indare/pcb_work/AudioV2.1/review/cursor_neg_01_power_fault.md

# v2.1 否定側査読 — ① 電源と故障の形（Cursor）

- 作成: 2026-09-26（Cursor 並行査読、読み取り専用）
- 対象: `origin/claude/vibrant-cray-axng64` 先端の `AudioV2.1/DECISIONS.md` / `NOW.md`
- 観点: 電源と故障の形
- 読んだもの: `/tmp/v21-claude/DECISIONS.md`（§1〜§6・§10 中心）、`NOW.md`、`design_eval_review.md`、`ds_facts/power.md`・`njw1194.md`・`verify_njw1194.md`、`review/power_budget_v21.md`・`power_budget_v21_review.md`・`ch_ldo_reverse_review.md`・`njw1194_power_impl.md`、リポジトリ側 `review/rail_detect_review.md`（ソケット短絡・22 Ω）、`datasheets/Recom_RS6.pdf`（OLP 字句）・`datasheets/tone/NJR_NJW1194.pdf`（p3・p6・p11）
- 読まなかったもの: `AudioV2/`・`Audio/` の文書、DECISIONS §4（ADC 経路の詳細）・§7 の大半、図を決定の証拠とする読み（図は v2 写し）
- 判定: **支持**／**修正**／**棄却**／**穴**（決定に無い／矛盾）／**確かめられず**
- 重さ: **損傷**／**聴こえる**／**無害**

## 0. 結論（表）
| # | 重さ | 指摘の一行 | 判定 | 確度 |
|---|---|---|---|---|
| 1 | 損傷 | トーン ±7 V に DS 応用の 100 µF 級を載せ、逆流ショットキーは DNP のままでは、主電源断でトーン LDO の OUT–IN が数 V 開く | 修正 | 一次資料＋計算 |
| 2 | 損傷 | 立ち下がりしきい値 ≈10.5 V のままでは、ソケット短絡を `MON` が取り逃しうる。design_eval B1 の整定後 ≈13 V は DECISIONS に無い | 穴 | 計算（design_eval 再現） |
| 3 | 損傷 | ソケット短絡時の 22 Ω は約 1 W で「2 W 連続で開く」帯に入らず、OLP 未測と組で連続過熱の窓が残る | 穴 | 計算＋推論 |
| 4 | 損傷 | 空ソケット禁止は運用のみ。違反時に ch LDO の OUT が +11.5〜12 V で秒残る経路にハードが無い | 穴 | シミュレーション（ch_ldo_reverse） |
| 5 | 損傷 | NJW1194 は「電源 OFF 前 MUTE」を採らず、無電源チップへの入力は未決のまま直列 1 kΩ だけ | 穴 | 一次資料 |
| 6 | 聴こえる | 電源断では Pico／`+5V_COIL` が ±15 V より先に死に、B2／`RAIL_OK` でラッチを戻せない（自覚済み・GND 落としは DNP） | 支持 | 計算（design_eval） |
| 7 | 損傷 | R1 の故障最悪 107 % は OLP 150 % の下で流れ続け、排他はファーム＋手順だけ。OLP の形は未測 | 確かめられず | 一次資料（字句）＋計算 |
| 8 | 損傷 | PD 12 V 枝のチップヒューズは I²t・協調未収集。コイル固着 560 mA 連続では切れないと本文が認める | 確かめられず | 二次（決定本文） |
| 9 | 損傷 | ch LDO「実効 ≈5 µF」は品種の DC バイアス無しでは数値にならない | 修正 | 推論（査読の前提） |
| 10 | 無害 | 1 ch 通電の R1 予算（設計点 63 %、悲観 ≈80 %）の算術自体は崩れていない | 支持 | 計算（査読再現） |

## 1. 指摘詳細

### [損傷] トーン ±7 V の大容量＋ショットキー DNP で、電源断のたびにトーン LDO が OUT–IN 絶対最大を数 V 越えうる
**何が** — DECISIONS §1-6（±7 V は TPS7A49／TPS7A30、逆流ショットキーは置き場のみ・実装しない）。NJW1194 DS 応用回路は V+/V− に各 100 µF〔DS p8、`ds_facts/njw1194.md`〕。TPS7A49 絶対最大 OUT–IN +0.3 V〔`ds_facts/power.md` p5〕。主電源断の ±15 V 傾き 0.26〜0.45 V/ms〔design_eval_review §1.1〕。
**なぜ効くか** — NJW1194 の電源電流 12 mA typ〔DS p3〕が 100 µF を抜く速さは 0.12 V/ms。傾き 0.45 V/ms のとき追随できる容量の上限は \(I/\mathrm{slew}=12\,\mathrm{mA}/0.45\,\mathrm{V/ms}=26.7\,\mu\mathrm{F}\)。100 µF のまま IN が OUT を下回ったあと、IN がさらに 7 V 落ちる間（15.6 ms）に OUT は 1.87 V しか下がらず、OUT–IN は約 +5.1 V。傾き 0.26 V/ms でも約 +3.8 V〔計算〕。ch LDO 側は実効 ≈5 µF に抑えたが、トーン側は ch と同じ「DNP」に寄せただけで、DS の 100 µF 級との両立が無い。
**確度** — 一次資料（NJW・TPS7A の DS）＋計算。傾きの数値は design_eval の〔計算〕を再利用。
**外れる条件** — トーンレール容量を実効 ≲25 µF（0.45 V/ms・12 mA）まで落とす、または OUT→IN ショットキーを実装する、または電源断で ±15 V が ±7 V より遅く落ちる実装になる。
**判定** — **修正**

### [損傷] ソケット短絡を立ち下がり ≈10.5 V が見逃しうるのに、整定後の高いしきい値が決定に無い
**何が** — §5-1 の立ち下がり案 ≈±10.5 V（帯 10.24〜10.79 V、0.1 %）。design_eval_review §0 B1／§1.4: ソケット短絡で娘レール ≈ 親 − 22 Ω × LDO 電流制限 min 0.22 A。
**なぜ効くか** — 親 15.0 V なら娘 10.16 V（帯の下で検出）。親 15.9 V なら娘 11.06 V（帯の上で**検出しない**）〔計算〕。正常整定の最悪は約 13.57 V なので、design_eval が勧めた「整定後 ≈13 V」なら短絡と 1.9 V 離れるが、DECISIONS §5-1・§6-2 のしきい値案は ≈12 / ≈10.5 V のまま。取り逃すと ch LDO は電流制限のまま、22 Ω に約 1 W が載り続ける（次項）。
**確度** — 計算（design_eval の式の再現）。電流制限 min 0.22 A は TPS7A49 DS〔`ds_facts/power.md`〕。
**外れる条件** — 整定後の第 2 しきい値（≈13 V）をファーム必須にする、または親の上限を 15.0 V 付近に縛る、またはソケット短絡を別経路で見る。
**判定** — **穴**

### [損傷] ソケット短絡 ≈1 W は「2 W 連続で開く」22 Ω の守りから外れる
**何が** — §2-4（ヒューズ抵抗、2 W 連続で開く）、§3-14（±15 V 側に枝ヒューズ無し、22 Ω と RS6 OLP・LDO 制限に頼る）。
**なぜ効くか** — design_eval §1.4: 短絡に回せる電流は常時負荷を差し引き約 0.21 A → 22 Ω で約 1 W。品の狙いが「2 W 連続で開く」なら 1 W は溶けずに熱くなる帯。OLP がヒカップなら切れる可能性はあるが形は V21-実測-01 未了。しきい値取り逃し（#2）と重なると、ファームもヒューズ抵抗も止めない連続過熱になる。
**確度** — 計算＋推論（品番の単発／溶断曲線は §10-1 どおり未収集）。
**外れる条件** — 1 W で開く品にする、整定後しきい値で短絡を落とす、OLP が短時間で出力を落とすと実測で分かる。
**判定** — **穴**

### [損傷] 空ソケット禁止が運用約束だけで、違反時の逆流エネルギーにハードが無い
**何が** — §3-7 の運用前提と §6-2「ファームは空ソケットを検出できない」。ch_ldo_reverse_review: 空だと OUT が +11.5〜12 V で 1〜10 s 残る。逆流ダイオードは実装しない（置き場のみ）。
**なぜ効くか** — 空を選ぶと石の電流が無く、COUT 実効 ≈5 µF でも帰還分圧だけで抜ける。主電源断・PRST で IN が先に落ちると OUT–IN が数 V（査読の空ケース）。決定は「選ばない」と書くが検知もインターロックも無い。
**確度** — シミュレーション（ch_ldo_reverse）＋決定本文。
**外れる条件** — ソケット有無の検知、空選択のハード禁止、または OUT→IN ダイオードを実装する。
**判定** — **穴**

### [損傷] NJW1194 の無電源入力は DS 上未規定のまま未決で、DS の予防（OFF 前 MUTE）を採っていない
**何が** — §1-6: 入力直列 1 kΩ 既定、電源の無いチップへの入力は**未決**。電源断前 MUTE は狙わない（3 線経由 ≈4 ms、Pico 停止 ≈2 ms）。DS: 絶対最大入力 VIM＝V+/V−〔p3〕、電源 ON 前の入力で初期状態異常、**電源 OFF 前に MUTE で防ぐ**〔p11〕。等価回路でクランプはパッド直下・200 Ω の手前〔p6〕。
**なぜ効くか** — 電源が 0 のとき字面どおりなら入力許容は 0 V。直列 1 kΩ・上限 2.3 Vrms（3.25 Vpk）ならクランプ電流 ≈(3.25−0.6)/1 kΩ＝2.65 mA〔計算〕。±7 V の 100 µF へ 20 ms で約 0.5 V 押し上げうる〔計算〕。§1-6 の「約 ±0.6〜0.8 V」と同桁。異常の中身は DS に無く、投入後の全レジスタ書き直しで足りるかは不明。0 Ω に替えられる足場がある。
**確度** — 一次資料。押し上げは推論＋計算。
**外れる条件** — 無電源時に入力をリレー等で切る、OFF 予告で MUTE が間に合う保持を足す、実測で異常が無害と出る。
**判定** — **穴**

### [聴こえる] 電源断でラッチが最後の状態のまま残る（決定が受容している故障の形）
**何が** — §2-10（電源断ポップ、GND 落としは足場・DNP）、§5-4 B2、§5-7。design_eval §1.1: `PD_12V_SW`／Pico 3V3 は約 2 ms で失われ、娘 ±15 V は 10.5 V まで 9〜15 ms、7 V まで 17〜29 ms。B2 の電源もコイルも先に死ぬ。
**なぜ効くか** — 音声リレーが SET のまま ±15 V が数十 ms かけて落ち、HP／LINE に過渡が出る。次の規則①全リセットまでラッチは残る。決定は戻さない側（B6）を採っているので矛盾ではないが、①の故障連鎖として閉じない。
**確度** — 計算（design_eval）。
**外れる条件** — 電源断用 GND 落としを実装し、検知立ち下がりから保持容量でリセットパルスを出し切る。
**判定** — **支持**（受容として記録は正しい。残リスク）

### [損傷] R1 の故障 107 % と OLP「150 % continuous」の関係は、OLP 未測のまま予算の外の前提になっている
**何が** — §3-13（故障 4 枚×1 ch で 107 %、OLP は働かない読み）、§3-1／V21-実測-01。RS6: "OLP 150% load, continuous, automatic recovery"〔p5〕。合計か出力ごとか、しきい値か耐量かは DS に無い〔`ds_facts/power.md`〕。
**なぜ効くか** — 1 ch 設計点 63 % は足りる（#10）。壊れる形は「基板またぎ排他が外れたとき」。ジャンパ重複・衝撃で電源リレーが複数 SET、などで 107 % が継続しうる。OLP が定電流なら熱で壊れるまで流れ、ヒカップなら可聴の断続。どちらも基板前実測待ちのまま R1・§3-14・22 Ω 電力が決まる。
**確度** — 一次資料（字句）＋予算の計算。動作形は確かめられず。
**外れる条件** — V21-実測-01 で OLP 形が分かり、107 % で保護が働く／働かないが確定する。ハードで電源 SET 1 本だけを保証する。
**判定** — **確かめられず**（決定の「働かない」読みは保守として支持できるが、実装判断の根拠には未測）

### [損傷] PD 12 V 枝ヒューズは定格未決で、コイル固着では切れない
**何が** — §3-14・§3-8（速断チップヒューズ、コイル最悪 560 mA・30 ms で切れない値、固着 560 mA 連続ではヒューズは切れず L7805C 過熱保護が先〔推論〕）。§10-1: チップヒューズ DS 未収集。
**なぜ効くか** — 短絡で切れることとパルスで生き残ることの窓は品番の I²t が無いと閉じない。クランプ＋ヒューズの協調（L7805 短絡で 12 V 素通し）も同じ。±15 V 側を「置かない」判断は #3・#7 に依存。
**確度** — 決定本文の自己申告。DS 無し。
**外れる条件** — 各枝のふつう／パルス／短絡電流を決めて DS 付きで選定する。固着検知でソフト遮断する。
**判定** — **確かめられず**

### [損傷] ch LDO「実効 ≈5 µF」は、セラミックの DC バイアスを決めないと 5 µF にならない
**何が** — §3-7（実効 ≈5 µF、公称 10 µF は 12 V で下がるので実効で選ぶ）。ch_ldo_reverse_review: OPA2140 相当 3.6 mA で COUT 10 µF なら主電源断 +2.8 V、PRST +1.9 V。実効 4.7 µF なら尾 +0.6 V 級。
**なぜ効くか** — 「約 5 µF」は目標で、品種・定格電圧・DC バイアス曲線が無い。公称 10 µF／16 V を載せて実効 7 µF なら低電流石で再び数 V 開く。逆流ダイオードは DNP のままなので、容量選定が唯一の常時手当て。
**確度** — シミュレーション＋推論（バイアス曲線は未収集）。
**外れる条件** — 実効容量の測り方／候補品のバイアス表を決定に書く、またはショットキーを実装する。
**判定** — **修正**

### [無害] R1 の 1 ch 通電予算そのものは否定できない
**何が** — §3-13（設計点最悪 +127/−125 mA、定格 63 %）。power_budget_v21_review が算術を再現、漏れ・二重は 1〜5 mA、悲観重ねでも ≈80 %。
**なぜ効くか** — 容量不足で R1 を棄却する材料は無い。壊れるのは故障・電源断・短絡・逆流の形（#1〜#8）。
**確度** — 計算（査読再現）。
**外れる条件** — HP ソケットに重い石、同時多 ch、ADC を ±15 V に戻す、など前提崩壊。
**判定** — **支持**

## 2. 見たが問題を見つけられなかったところ
- EN を LDO の IN 分圧から作り FET で落とす形（§2-9）— USB のみ起動で EN>IN を構造で避ける筋は、読んだ範囲で崩れていない。
- B1（レール無の娘は音声 SET 不可）と音声 SET 共通 1 本（§2-6）の組み合わせ — 指令経路では電源無の娘をバスに繋がない、という主張は一貫している（衝撃・ARST 単一故障は別）。
- `PD_12V_SW` 検知＋規則①（起動時に既に検知あり）②③（§5-7）— 09-25 の「USB 先挿しで全リセットが走らない」「`MON` 兼用の誤良」への書き換えは、読んだ範囲で穴を塞いでいる。
- 娘バルク削除＋直列 22 Ω（§3-5・§2-4）— 共振・突入の議論は査読どおりで、電源故障の新しい主因にはなっていない。
- ch LDO の CNR/SS 必須（§3-7）— 起動落ち込みでしきい値を殴る経路を抑える判断は、今回の否定材料では覆らない。

## 3. 確かめられなかったこと
- RS6 OLP／SCP の実動作（出力ごと／合計、定電流／ヒカップ、短絡時入力電流）— V21-実測-01。#3・#7・22 Ω の連続電力がここに懸かる。
- NJW1194「初期状態の異常」の中身と、投入後の全書き直しで消えるか — DS に現象の定義が無い。
- トーン ±7 V を何 µF で実装するか — 決定に値が無く、DS 応用 100 µF との差分が未記入。
- チップヒューズ・22 Ω ヒューズ抵抗・B1 の PMOS／ツェナーの品番 DS（I²t・溶断・しきい値）。
- 電源断時に入力クランプが ±7 V をどこまで押し上げるか（1 kΩ・結合 C・源 Z の実測）。
- 図の現物ネット（写しの v2）を決定の証拠にする読み — 依頼どおり未使用。
