indare/pcb_work/AudioV2.1/review/cursor_neg_03_audio_path.md

# v2.1 否定側査読 — ③ 音声の経路の品質（Cursor）

- 作成: 2026-09-26（Cursor 並行査読、読み取り専用）
- 対象: `/tmp/v21-claude/DECISIONS.md` §1-5, §1-6, §2-3, §2-8〜2-11, §2-14, §4-*、`NOW.md`；`review/njw1194_io_review.md`, `direct_bypass_review.md`, `njw1194_alternatives_review.md`, `design_eval_review.md`；`ds_facts/njw1194.md`, `verify_njw1194.md`, `tap.md` / `verify_tap.md`, `switch_control.md`（必要箇所）
- 観点: ③ ライン入力〜NJW1194〜娘選択〜ch〜`AMP_SEL`〜ポット〜DEST/HP/LINE、DIRECT/スルー、結合C、ポップ・クリック、バス負荷、ADCタップが本線を汚すか、レベル整合。否定側。結論防衛しない
- 図: 文書上「写したまま（v2）」と明記。本査読は決定・査読・DS事実に限定（`AudioV2/`・`Audio/` 文書は未読）

## 0. 結論（表）

| # | 論点 | 判定 | 重さ | 一行 |
|---|---|---|---|---|
| 1 | 入口直列 1 kΩ（既定） | **支持**（代償は記録不足） | 無害〜聴こえる | クランプがパッド直下〔verify〕で外側だけが電流を決める。平坦 −0.42〜−0.56 dB、L/R 差最大 0.14 dB〔io査読〕 |
| 2 | 入口・出口 4.7 µF フィルム | **支持** | 聴こえる（段の角）／無害（低域） | 出口オフセット規定無し・入口は DC 利得 1。20 Hz 最悪 −0.10 dB。角は C でも残る |
| 3 | DIRECT＝スルー、MUTE→TSW | **修正** | 聴こえる | 音楽の硬い端は消えるが、TSW は音量**後ろ**。MUTE は出力 DC を消さない〔io査読〕。全リセット控えの条件が未実測 |
| 4 | 無電源チップへ源が来る | **穴** | 損傷（LDO）／聴こえる（投入異常） | §1-6 未決のまま 1 kΩ・ショットキー置き場（実装しない）で先へ進んでいる。源無しでも電源断の OUT–IN が越えうる〔io査読 §6.3〕 |
| 5 | `TONE` 100 kΩ | **支持**／値は**修正候補** | 聴こえる（待ち） | DC 基準は要る。4.7 µF×100 kΩ の 5τ≈2.4 s。TSW を全リセットに下げると ch 切替 0.25〜0.75 s の 3〜10 倍 |
| 6 | ch 入力 220 kΩ | **支持**（役割は変わった） | 無害 | IS(OFF) 漂流の保険は妥当。入出力同時切替では「聴こえる前に吸収」は取れず、全リセット待ちに吸収〔§2-14〕 |
| 7 | `AMP_SEL OUT`→DEST 直前（§4-14） | **支持** | 無害 | ミュート足場の内側。計測タップは前のまま。足場が 0 Ω/DNP なら端子も切替過渡を見うる（全リセット中は `AMP_SEL` は 100 kΩ で GND） |
| 8 | 差動 ADC（Q2）・本線汚れ | **支持（保険）**／本線副作用は**確かめられず** | 無害〜聴こえる | 本線に触るのはバッファだけ〔§4-1〕。グランド差の実効は未測（V21-実測-07）。縦積みの段間降下はセンスしない |
| 9 | 公称 2 / 上限 2.3 Vrms | **修正** | 聴こえる | 数字の算術は合う。2.3 の出自は旧 PT の THD=1% min。NJW 後は天井が ADC/石/TMUX に移ったが「きれいに通る上限」としては根拠が薄い |
| 10 | TMUX／リレー接点・47 Ω・コールド | **穴**（継-17）／構造は**支持** | 損傷（故障時）／聴こえる（ラッチ残） | コールド＋境目リレーは筋が通る。`V21-継-17`（出力 47 Ω）は理由が空。電源断で音声 SET 残存→無電源 TMUX へ源〔旧 DIRECT 査読の筋がラッチに残る〕 |

## 1. 指摘詳細

### [穴] 無電源の NJW1194 に源が来ることを「未決」のまま、入口 1 kΩ・ショットキー未実装で経路を固定している

**何が** — §1-6 状態欄末尾「未決: 電源の無いチップの入力に源が来ることを受けるか」。同時に入口直列 1 kΩ 既定・±7 V LDO の OUT→IN ショットキーは「置き場・実装しない」。DS: 電源断時の入力扱い無し；クランプはパッド直下でチップ内直列制限無し〔`verify_njw1194` 行 97・118〕。p11 は投入前入力→初期異常の注のみ。  
**なぜ効くか** — (a) 源あり: 1 kΩ でもレール押し上げは約 ±0.6〜0.8 V 見込みで LDO の OUT–IN 絶対最大 +0.3/−0.3 V を越える〔io査読〕。(b) **源無しでも** ±15 V が ±7 V より速く落ちれば毎回 OUT–IN が数 V まで開きうる〔同 §6.3〕。ショットキー未実装なら (b) は未決と無関係に残る。(c) 投入前信号は p11 どおり乱れうる；規則①の全レジスタ書き直しは「乱れのあと」の回復で、壊れ・ラッチアップを保証しない。  
**確度** — DS・絶対最大は一次；押し上げ電圧・落ち方の速さは推論＋要実測。  
**外れる条件** — ショットキーを実装し Vf≤0.3 V を使う電流で満たす／源を電源断中に切る／実測で OUT–IN が常に内側。  
**重さ** — 損傷（LDO・場合によりチップ）／聴こえる（投入時の異常状態）。

### [修正] 「MUTE してから TSW」は音楽の切断端だけを消し、DIRECT⇄トーンの DC 段と切替点のクリックは残しうる

**何が** — §1-6: DS p8「TSW 切替時は MUTE」、音量 MUTE→TSW。TSW は減衰器の**後ろ**〔njw1194 p8／io査読〕。出口オフセット規定無し；MUTE は DCCAP による DC 利得 1 のオフセットを消さない〔io査読〕。出口 4.7 µF は「居座らない」だけで、動いた瞬間の角はバスへ出る。  
**なぜ効くか** — 聴取中（音声リレー SET）に TSW すると、角は `TONE`→娘→利得 2→`AMP_SEL`→ポットへ出る。控えの「全リセットの中で書く」は段の実測待ちで、手順・待ち（§5 の 2.4 s 問題）が未固定。初期値 TSW=0（スルー）〔p11〕なので電源投入直後は DIRECT 側。  
**確度** — ブロック図の並びは DS；段の大きさは DS に無く未測。  
**外れる条件** — 実測で段が聴感下／常に全リセット窓で TSW＋十分な整定。  
**重さ** — 聴こえる。

### [修正] 上限 2.3 Vrms は NJW1194 採用後も数字だけ引き継ぎ、「経路品質の天井」としては根拠が腐っている

**何が** — §1-5: 公称 2・上限 2.3、両経路共通。旧 `direct_bypass_review`: 2.3＝PT2314E VOMAX（THD=1% min）で、typ では 2 Vrms でも約 0.1 % 級。§1-5 自身「NJW スルー max 3.6 Vrms min はもう天井にならず、先に頭を打つのは ADC 2.73 → 石 2.8〜 → TMUX 2.9〜3.5〔仮定〕」。V21-継-08 は 2.3×2＝4.6 Vrms を ADC FS の −1.5 dB に合わせるだけ。  
**なぜ効くか** — (1) 2.3 は「きれいに通る」上限ではない（旧査読の修正が DECISIONS 本文に残っていない）。(2) 本線の最初の制約は ADC より石の出力（約 2.8 Vrms）に近く、2.3 運用でも石しだいで肩に乗る。(3) スルーとトーン 0 dB の THD/雑音差はグラフ typ（約 0.005/0.01 %、1.41/2.2 µV）で、保証は最大出力・利得・分離だけ〔§1-6 前提〕—「両経路で同じ上限」は振幅の話であって品質の等価を意味しない。  
**確度** — 算術は再現済み；2.3 のユーザー判断は文書上の決定。  
**外れる条件** — 2.3 を「運用の都合（ADC VU の余白）」と明示し、本線品質の物差しから外す。  
**重さ** — 聴こえる（歪みの肩・経路差の誤読）。

### [修正／穴] 出口 4.7 µF × `TONE` 100 kΩ の整定を 5τ≈2.4 s に置くと、DIRECT 切替を全リセットに下げた瞬間に手順が破綻する

**何が** — §1-6.7: 100 kΩ のまま、長ければ 47 kΩ。io査読: 5τ=2.35 s；§6-2 の ch 切替 0.25〜0.75 s。投入時の支配は出口 C より DCCAP 100 µF 側の可能性〔io査読〕。  
**なぜ効くか** — TSW 段が聞こえて控えに落とすと、DIRECT 一回ごとに数秒無音になり、ch 聴き比べのテンポと噛み合わない。固定 5τ は段／許容から決めるべき〔同〕。  
**確度** — τ の算術は計算；DCCAP 支配は推論。  
**外れる条件** — 聴取中 MUTE+TSW で段が無視できる／47 kΩ＋実測待ちで 1 s 未満。  
**重さ** — 聴こえる（操作ギャップ）。UX としては損傷に近い。

### [穴] `V21-継-17`「出力側スイッチは 47 Ω の後ろ」が理由空のままコールド設計の前提に残っている

**何が** — §7 継-17 は決定文だけで理由・出典・ネット位置の再記述が無い。`design_eval_review` は「47 Ω 越しに娘の容量を充電」「ミュート時 τ＝2.2 µF×(R+47 Ω)」等で図の 47 Ω を引用するが、v2.1 の「入力も切る TMUX×2・全リセット」での役割の再確認が DECISIONS に無い。  
**なぜ効くか** — 47 Ω は (a) 出力 TMUX の容量負荷・短絡電流、(b) 無電源クランプ時の電流制限、(c) 雑音／分圧、のどれを主目的にしたかが不明だと、コールド故障（音声リレーが SET のまま電源喪失）で IIK ±30 mA〔TMUX DS〕を割るか判断できない。旧 DIRECT リレー案では Zs 50 Ω で越えうる〔direct_bypass_review #24〕— NJW スルー後も**ラッチ残存＋源**の形は娘側に残る。  
**確度** — 継項目の空疎は文書事実；電流超過は条件つき推論。  
**外れる条件** — 継-17 を v2.1 回路で再記述し、SET 残存時の制限抵抗として足りると示す。  
**重さ** — 損傷（故障・電源断の窓）／通常聴取では無害。

### [支持（条件つき）] 入口 1 kΩ・両側 4.7 µF 自体の低域・駆動は問題になりにくい

**何が** — 中域負荷約 40.7 kΩ、DS p24 は約 400 Ω まで振幅維持〔io査読〕。20 Hz −0.10 dB（最悪直列 0 Ω）。端子側 1 MΩ 置き場で浮き対策。  
**なぜ効くか（否定しきれない点）** — 容量負荷安定は DS に無し（出口直列 0 Ω 置き場は保険）。film 4.7 µF×4 の外形は未確認〔io査読〕。1 kΩ の L/R 差 0.14 dB はステレオ像では境界、ch 比較（共通経路）では無害。  
**確度** — 計算＋DS グラフ。  
**重さ** — 無害（低域・駆動）／聴こえる（L/R 差・安定は未確認）。

### [支持] `TONE`/`AMP_SEL` の NC 10 kΩ・バス 100 kΩ・全リセット無音の骨格

**何が** — §2-3 COM＝娘／NO＝バス／NC＝抵抗→GND。逆向きはバスを並列負荷〔査読〕。§2-10 は全リセット中に TMUX・LDO・結合整定を閉じ込め、ポット前 GND 落としは切替に使わない。  
**否定側の残り** — 「SET 瞬間が静か」は推論・未査読〔§2-10〕で V21-実測-12 待ち。電源断ポップと HP バッファ自身の崩れは消えない〔同〕。音声 SET 共通 1 本＋衝撃ラッチで別娘の電源が入る形はバスには出ないが RS6 負荷は増える〔§2-6〕。  
**重さ** — 通常切替は無害〜聴こえる（実測待ち）；電源断は聴こえる。

### [支持] ch 入力 220 kΩ（役割変更を明示せよ）

**何が** — §2-14: IS(OFF) max 0.15 nA で結合 C が 9 mV/分漂流→220 kΩ で 33 µV。入出力 TMUX 同時切替では旧「入力先閉じ待ち」は取れず、段差は全リセット整定へ〔§2-14〕。  
**否定側** — 選中は `TONE` 負荷に 220 kΩ が並ぶが、中域 40.7 kΩ 支配で駆動余裕は残る〔io査読〕。  
**重さ** — 無害。

### [支持／確かめられず] ADC タップは本線負荷としては軽い設計。差動は未実証の保険

**何が** — §4-1/4-2: 触るのは OPA1656 フォロワ；品質より本線非汚染優先。§4-3 Q2: INA1650、センスは娘→母の `A_GND` ピン際。§4-6: ADC 手前 47→100 Ωは**計測枝**（本線外）で電源断窓のクランプ電流対策。§4-7: `±15V_AFE` 22〜33 Ωでリップルの `A_GND` 注入を抑える。  
**否定側** — (1) グランド差の実効未測（V21-実測-07）；効かなければ Q2 は部品増のみ。(2) 縦積みで段間コネクタ降下はセンス外〔§4-3〕。(3) I²S／ADC デジが音声に漏れるかは V21-実測-06。(4) 100 Ω は ADC 精度 −0.09 dB と DS 推奨からの逸脱—本線には非該当。  
**重さ** — 本線汚れ: 確かめられず（設計意図は無害側）。計測の誤表示: 聴こえないが運用ノイズ。

### [支持] §4-14 `AMP_SEL OUT` を DEST 直前へ

**何が** — ポット前ミュート足場の後ろ、DEST 直前；HP/LINE ポット入口と同じ。タップは従来どおりミュート前。  
**否定側** — 足場直列が 0 Ω の間は端子インピーダンス＝`AMP_SEL`。ミュート実装時は 470 Ω〜1 kΩ で −0.17 dB（50 kΩ ポット）〔§2-10〕。外出しを「常時クリーンなラインアウト」と読むと、DEST/ポット前の信号であることの説明不足。  
**重さ** — 無害。

### [修正] DIRECT＝チップ内スルーにした結果、「トーンを通さない経路」の語義が変わったまま品質比較に使われている

**何が** — §1-5 見出しは「トーン段を通さない」。実装は音量段＋スルースイッチは通る（トーン EQ のみバイパス）。`njw1194_alternatives_review`: 同等単体は他に無く、代替は音量 IC 追加か旧リレー形。  
**なぜ効くか** — 石の差を聴く目的に対し、共通床が NJW の音量／スルー雑音・THD（typ／グラフ）になる。旧リレー DIRECT の「硬い端が本質」問題は消えたが、代わりに全 ch 共通の IC 床が乗る（PT 却下理由と同型）。  
**確度** — 構成は決定事実；床が聴き比べを潰すかは未測。  
**外れる条件** — ユーザーが「EQ 以外は共通でよい」と明示（NOW はそれに近い）。  
**重さ** — 聴こえる（比較の分解能）。

## 2. 見たが問題なし

- **COM＝娘／NO＝バス／NC＝抵抗**（§2-3）— 逆向きよりバスを汚さない。音声 10 kΩ・レール 2.2 kΩの算術は査読と一致。
- **娘の TMUX は切られた ±15 V、ソケットだけ ±12 V LDO**（§2-8・§3-3）— 膝を下げない／電源無し石をバスに繋がない、の筋は DS（入力保護・スイッチクランプ）と整合。
- **選んだ娘の TMUX は ch EN で切らない**（§2-8・継-16）— バス接続中の通電要求と一致。
- **NJW 中域駆動余裕**（約 40.7 kΩ vs 400 Ω級）— 出口バッファ不要の判断は DS グラフと整合。
- **ADC 前 100 Ω・AFE 直列 22〜33 Ω・RCOM 0 Ω** — 本線ではなく計測枝の自己防衛／戻り電流の話として一貫（本線汚染の主因にはならない）。
- **DEST＝機械スイッチ、音量＝手回しポット**（継-02〜04）— ファーム接点を出口に増やさない方針は経路品質にプラス。
- **PT2314E 却下＋スルー無し DSP 却下** — 全 ch 共通歪み／常時クロックを避ける否定側理由は妥当（NJW 床は上の修正で別問題）。

## 3. 確かめられず

- TSW／音量段切替の**実段電圧**、MUTE 中でも残る出力 DC、ゼロクロス有無の効き（Features 名のみで仕様無し〔verify 足すべき項目〕）
- 電源断時の ±15 V 対 ±7 V の落ち方、OUT–IN 最大、源あり／無しの入力電流（§1-6 実測リスト・io査読）
- 音声 SET 瞬間のポップ実測（V21-実測-12）、バウンス時間（AZ850 DS に無し）
- 縦積み 4 段の `TONE`/`AMP_SEL`/`A_GND` の接触抵抗・容量・段間降下が聴感・ADC に効くか
- Q2 が Q1 より本線／表示を良くするか（V21-実測-07）；I²S 漏れ（V21-実測-06）
- film 4.7 µF×4 の実装可能性；出口 C を入口のみに落とせるかのオフセット実測
- 公称 2 Vrms の出典（旧査読「リポジトリに無い」）；手持ち最悪石の実出力天井
- `V21-継-17` の 47 Ω の正確なネット位置と、v2.1 コールド故障電流での必要性
- NJW 3 線を UI MCP 3.3 V 直結で VIH 2.5 V を満たすか（余裕 0.1 V、AHCT 置き場）— 制御だが書き込み失敗は MUTE/TSW 失敗＝聴こえる経路事故

---

**総評（否定側）**: 結合 C・1 kΩ・バスプルダウン・全リセット無音・コールド＋境目リレーは、文書と DS が噛み合っている限り**本線を意図的に汚す決定ではない**。壊れているのは (1) **無電源入力／LDO 逆バイアスが未決・未実装のまま経路が固定されていること**、(2) **MUTE+TSW＝クリック無しという読み過ぎ**、(3) **2.3 Vrms と「DIRECT」語義が NJW 後に更新不足**、(4) **継-17 と整定待ちが手順と衝突しうること**。実装前に潰すべきは (1) と TSW 段の実測→手順分岐の固定。
