indare/pcb_work/AudioV2.1/review/cursor_neg_06_mech_stack.md

# v2.1 否定側査読 — ⑥ 機械・縦積み・筐体・手の届き（Cursor・追加観点）
- 作成: 2026-09-26（Cursor 並行査読、読み取り専用）
- 対象: `/tmp/v21-claude/DECISIONS.md` §1-4・§2-5・§2-13・§10（V21-未決-20 ほか）／同 NOW の装置・PCB 節。写しの PCB・配置スクリプトは現況の参照のみ（決定の証拠にしない）。`AudioV2/`・`Audio/` 文書は未読。

## 0. 結論（表）

| 重大度 | 件数 | 要旨 |
|---|---|---|
| 重大 | 2 | 装置目的の制約（DIP 手の届き）を未検証のまま 4 枚縦積みをいったん決めている／手の届きと「電源断してから抜き挿し」がサービス手順として衝突しうる |
| 要確認 | 5 | 2×12 のピン配置・キーイング未決／段間 5 mm＋部品高さ＋基板間距離が未設計／ラッチ誤動作の機械経路がソフト頼み／スタック接点定格未収集／シャーシ 1 点とパネル閉路が未決 |
| 軽微 | 2 | 写し PCB は横 3 スロットのまま／ジャンパ重複は「聴こえる」止まりで機械対策が後回し |

**総評:** 電気の木（縦積み・2×12・4 枚）は先に閉じ、機械の成立条件は §10 と統合リスト C3 に残したまま。装置の定義（DIP 差し替えで音を楽しむ）に対し、機械側が先に破綻する形になっている。

## 1. 指摘詳細

### [重大] 4 枚縦積み（§2-13）を、DIP 手の届き（V21-未決-20）の前にいったん決めた

**何が** — V21-継-22 は「DIP ソケットに手が届くこと」を装置目的上の最大の制約とし、縦積みでの確認を V21-未決-20 に委ねる。§2-13 は娘 4 枚をいったん決め、前提に「手が届くかは段の数で決まる（V21-未決-20）」と書くだけ。NOW も「残る未決: -20（縦積みの DIP の手の届き、模型）」と残す。統合リスト C3 は原寸模型を「先に測る」に置き、重さを「無害」とする。  
**なぜ効くか** — 1 枚 4 ch・4 枚＝16 ソケットが縦に重なる。下段の DIP に指・抜去具が届かなければ、採用した電気構成（1 種類・縦積み・§1-4）が装置目的と両立しない。枚数決定は接続ピン数（PSET×4）の帰結であり、手の届きの帰結ではない。  
**確度** — 一次資料（DECISIONS・NOW・design_eval_review C3）。到達可否の実測は無い。  
**外れる条件** — 原寸模型で 4 段まっすぐでも全ソケットに届く／階段・引き出し・上から抜く手順で届きが保証される、のいずれかが先に閉じた場合。

### [重大] 「DIP を挿し替える」運用と「活線で抜かない」運用が、積み上げたままでは両立しにくい

**何が** — §6-2 運用: 娘は電源を切ってから抜き挿しし、挿したら起動し直す（V21-未決-25 をいったんの決め）。装置はソケット差し替えが主作業（NOW 装置節・V21-継-22）。下段に届かないなら板を外す必要があり、外すたびに電源断＋再起動が必須。  
**なぜ効くか** — サービス 1 回のコストが「石を抜く」から「スタックを解体 → 電源断 → 再組立 → 全リセット起動」に膨らむ。目的が「切替で聴き比べ」なら、機械手順が比較の頻度を律速する。  
**確度** — 一次資料（§6-2・§2-13・V21-未決-20）。手順の所要時間は未計測。  
**外れる条件** — 積んだまますべての DIP に届く／差し替え専用の抜き出し機構が決まる、のいずれか。

### [要確認] 2×12 は本数だけ閉じ、ピン配置・キーイング・音声 2×5 との関係が未決のまま PCB 前提になっている

**何が** — §2-5: 制御・電源コネクタは 2×12（24 本）いったんの決め。内訳は並べたが「ピン配置は未確定」。V21-未決-22 は内訳を閉じた扱い。NOW PCB 節は「本数は v2.1 で 2×12」としつつ、写しは 2×8＋2×5・キーイング規則を「維持」。査読記録側には「電源・制御は 2×12、音声は 2×5（今のまま）」の整理案があるが、§2-5 本文は音声コネクタを明示しない。  
**なぜ効くか** — 4 段素通しでは 1 ピンの取り違えが全段に効く。キー無し・配置未決のまま外形・M3・南北辺だけ引き継ぐと、引き直しで電気決定と噛み合わない穴あけになる。音声と電源を別コネクタにするなら、両系の芯出し・嵌合順序・誤挿入も機械要件になる。  
**確度** — 一次資料（§2-5・NOW）。写し PCB は v2 幾何の参照のみ。  
**外れる条件** — ピンマップとキーイング（電源／音声の取り違え不可）が DECISIONS に決まり、外形規則がそれに合わせて書き直された場合。

### [要確認] 段間リレー 5 mm・部品高さ・基板間距離・冷却が、どの決定にも寸法として閉じられていない

**何が** — §2-1／V21-未決-19: 上下・隣のリレーは 5 mm 以上。AZ850 本体高さは約 5 mm（ds_facts）。写し生成コメントは基板間 15 mm・ロングテール約 11 mm（決定ではない）。v2.1 娘は電源用＋音声用で 1 枚 3 個のラッチ、DIP-8×4、LDO・デコーダ等が乗る。箱の外形・通風・ヒートシンクは未決。  
**なぜ効くか** — 基板間を狭めると (a) 上下リレーの 5 mm、(b) DIP／変換モジュールの背丈、(c) 指の侵入空間が同時に競合する。広げるとスタック全高が筐体に入らない。冷却は板間で対流が止まり、親の L7805C（パルス時 (12−5)×約 0.56 A ≈ 3.9 W 級〔計算〕）と HP バッファ（別査読で箱内熱が論点）の熱経路が未設計のまま残る。  
**確度** — DS・決定の制約は一次。15 mm は写しスクリプトの仮定。熱の箱内分布は未実測。  
**外れる条件** — 段間クリアランス表（リレー／DIP／電解／コネクタ嵌合）と筐体高さ・通風が決まり、模型で干渉ゼロが示された場合。

### [要確認] ラッチ誤動作の機械経路を、ファーム全リセットと B1 に寄せすぎている

**何が** — §2-1: 衝撃・前歴で状態が変わりうる（根拠は主に G6K・TQ。AZ850 本体 DS にラッチ反転の明文は無い〔bnd〕）。採用石は AZ850P2-5（§2-2）。§2-6: 聴取中に別娘の電源リレーが衝撃でラッチすると、その娘のレールと共通 ch 選択で LDO まで入り、「厳密に 1 ch」が電気的に破れる（音声はバスに出ない）。対処は次の切替の全リセット。同一パネル上の他リレー振動を警告するのは G6K 系。4 枚×3＝12 個が近接。  
**なぜ効くか** — 縦積みはリレー動作の衝撃・磁気が隣段に伝わりやすい。電気的ミュート／B1 は「バスに音が出ない」を守っても、「同時に温まる ch が 2 つ」や RS6 負荷の一時悪化は残る。機械ダンパ・スペーサ剛性・動作タイミングの分散が無い。  
**確度** — 一次資料＋DS。AZ850 での衝撃反転は「同種ラッチの一般論」〔推論〕。  
**外れる条件** — AZ850 実機でスタック実装の衝撃試験が通り、または非ラッチ／間隔・固定法で機械誤動作が消える場合。

### [要確認] スタックヘッダの接点定格（突入 0.68 A・コイル 560 mA パルス）が §10 の「DS を取るもの」のまま

**何が** — V21-継-23: 挿抜寿命は制約にしないが、電流は縦積みで上記パルスが乗るので品番 DS で確かめる。§10 本文も 2.54 mm スタックヘッダの接点定格を未収集と列挙。  
**なぜ効くか** — 4 段直列の接点は抵抗と劣化が段数で積む（spice 仮定 HOP_R 等）。電源メイクの繰り返しは接点溶着・接触圧低下の機械故障モード。電気の 22 Ω 設計が接点側で破綻しうる。  
**確度** — 決定・§10 の一次。品番未定のため数値は未照合。  
**外れる条件** — 採用ヘッダの DS でパルス電流・接触抵抗が余裕込みで合格し、金メッキ音声側の方針が固定された場合。

### [要確認] シャーシ 1 点（V21-継-20）の落とし先（V21-未決-15）が未決のまま、パネル配線が先行している

**何が** — NOW: FP は垂直実装→パネルネジ止め、HP/LINE は XH でパネルジャックへ、GND は XH 系統分離。§3-9: 木が成り立つのはシャーシを 1 点で落とすときだけ（パネル金属・ジャックスリーブ・PD シェルの閉路）。V21-未決-15 は未決のまま。  
**なぜ効くか** — パネル部品を先に仮組みすると、意図せず 2 点アースやスリーブ経由ループができ、電気決定（b-1・ADC の木）が筐体配線で壊れる。サービス（パネル脱着）のたびに再現しうる。  
**確度** — 一次資料。現物箱は未製作。  
**外れる条件** — 落とし先と絶縁／導通の部品表が決まり、パネル図がそれに従う場合。

### [軽微] 写し PCB は「横 3 スロット」のまま。縦積み 1 塔の親ラフが無い

**何が** — `place_a2_slot_connectors.py` は母板スロット 3 口横並び。NOW も中央＝娘タイルと書く。v2.1 決定は縦積み 4 枚・親スロット 1 系統。  
**なぜ効くか** — 決定と写しが食い違うと、ゾーン・ Edge・配線の教訓を「維持」と読んだ実装が横並び前提に戻る。  
**確度** — 写しは現況参照。決定の証拠ではない。  
**外れる条件** — 親を 1 塔用に引き直す前提が NOW／生成方針に明示された場合（すでに「引き直し」と書いてあるなら、横並び維持を明示的に捨てること）。

### [軽微] ジャンパで段選択（§2-5）の重複事故を、機械では潰していない

**何が** — §2-6 前提: ジャンパ重複で 2 枚が同じ段を選ぶ弱点は残る。design_eval C3: 階段にすれば線の回しでジャンパ不要、まっすぐならジャンパのまま。重さは「無害（ジャンパの重複は聴こえる）」。  
**なぜ効くか** — サービス時の設定ミスが電気排他（§1-2）を破る。聴こえる／電源余裕の話に落とすと、組み立て検査項目が消える。  
**確度** — 一次資料。  
**外れる条件** — 物理キー・1 箇所しか挿さらないジャンパ・段ごとに配線をずらす階段実装などで重複が構造的に不可能な場合。

## 2. 問題なし

- **§1-4（1 種類・1 枚 4 ch・切替素子の聴き比べなし）** — 機械的には同一カードの縦積みを可能にする方向。2 種 PCB の嵌合差を増やさない。否定側から見て、ここ自体が機械破綻の原因ではない。
- **音声／デジ／電源の XH 分離と FP 集約（NOW）** — パネル配線の系統分離方針は、シャーシ落とし先さえ決めれば機械と整合しうる。方針自体は機械否定の材料にならない。
- **活線挿入を運用で禁じる（§6-2／旧 V21-未決-25）** — コネクタ溶着・前歴持ち込みを避ける向きは機械・接点の安全側。禁じること自体は妥当（届き問題との衝突は別指摘）。
- **リレー隣接 5 mm を DS 制約として文書化したこと（§2-1／V21-未決-19）** — 制約の認識はある。未充足なのは寸法設計の側。

## 3. 確かめられず

- 原寸 4 段スタックで、下段 DIP-8（および変換モジュール）に指・工具が届くか（V21-未決-20・模型未実施）。
- 採用する基板間距離・スタッキングヘッダ品番・嵌合長・M3 スペーサの有無と剛性。
- AZ850P2-5 を 12 個近接実装したときの、動作衝撃によるラッチ誤遷移の有無（AZ850 DS に反転明文なし）。
- 2×12／2×5 の最終ピンマップ・キーイング・誤挿入試験。
- スタック接点の許容パルス電流・接触抵抗の段数積み（§10 未収集 DS）。
- 筐体外形・通風・L7805C／HP バッファ／RS6 の熱経路と箱内気温。
- シャーシ落とし先とパネル金属部の実配線（V21-未決-15）。
- 「階段積み」案のコネクタ芯ずれ・ケーブル／ピン曲げ応力（C3 の代替案の機械成立）。
