indare/pcb_work/AudioV2.1/review/adc_gnd_retree.md

# AudioV2.1 — ADC グランドの木の組み替え（回路図レベルの提案）

- 作成: 2026-09-25（エージェント。**リポジトリのファイルは変えていない**。出力はこのファイルだけ）
- 対象: `AudioV2.1/`（`MeasureControl` とルート `AudioV2Case`）。v2（`AudioV2/`）は見ていない
- ユーザーの決定（前提。ここでは蒸し返さない）: タップは `AMP_SEL_L/R` のまま／結合は Q2（`U1611` の後ろに INA1650、0 Ω・ジャンパで Q1 に戻せる）／
  ADC 経路は絶対品質不要、**本線を汚さないのが最優先**／ADC の LDO（`U1603`→`+3V3_A`、`U1606`→`+5V_A`）は PD 12 V から取る

## 出典の記号

| 記号 | 意味 |
|---|---|
| **[SF all]** / **[SF pin X]** / **[SF nets N]** / **[SF bom]** | このセッションで回した `python3 AudioV2.1/scripts/sch_facts.py all / pin X / nets --net N / bom --json` の出力 |
| **[SF gnd]** | `sch_facts.Design` を読み取り専用で回し、グランド 5 ネット（`A_GND` `D_GND` `PD_GND` `ADC_GND` `GND_COIL`）の 2 つ以上にピンを持つ部品を列挙したもの |
| **[G MC]** / **[G root]** | `MeasureControl.kicad_sch` / `AudioV2Case.kicad_sch` を読んだもの（シンボルの Description・図上の座標・テキスト注記・`lib_symbols` のピン名・シートピン一覧） |
| **[PCB]** | `AudioV2.1/AudioV2Case.kicad_pcb` のフットプリント座標（親ラフ段階） |
| **[RB]** / **[RB-pd]** | `python3 AudioV2.1/scripts/rail_budget.py`（無印）/ `--adc-from-pd` の出力 |
| **[tap:L]** **[pow:L]** **[sc:L]** **[op:L]** | `AudioV2.1/ds_facts/tap.md` / `power.md` / `switch_control.md` / `opamps.md` の行（照合済み） |
| **[PDF ファイル pN]** | このセッションで `pdftotext -layout` で開いた一次資料のページ（PDF ページ番号） |
| **[DEC:L]** / **[NOW]** | `AudioV2.1/DECISIONS.md` / `NOW.md` の記録（履歴であって事実の正ではない。引くときはそう書く） |
| **[計算]** | 上の出典の数値からの算術 |
| **〔推論〕** | 出典から直接は言えない、このエージェントの判断 |

---

## 0. 結論と、前提の照合結果

### 0.1 提案の木（要約）

```
Q2（差動・既定）                                   Q1（片側・戻し）
GND_COIL ─NT101─ D_GND ─NT1602─ PD_GND            GND_COIL ─NT101─ D_GND ─NT1602─ PD_GND
                  ├──NT1603── A_GND ─NT102─ AGND_SNS               ├──NT1603── A_GND ─NT102─ AGND_SNS
                  └──JP1601(2-3)── ADC_GND                         │            └──JP1601(1-2)── ADC_GND
                                                                   （ADC_GND–D_GND の直結は無い）
```

- **`NT1601`（`ADC_GND`–`A_GND`）を消し、3 ピンの選択子 `JP1601`（1=`A_GND` / 2=`ADC_GND` / 3=`D_GND`、1×3 ピンヘッダ＋シャント 1 個）に置き換える。**
  Q2 は 2-3、Q1 は 2-1。シャントは 1 個しか載らないので**両方同時（＝閉路）は機械的に起きない**。
  シャント無し（＝`ADC_GND` 浮き）は `ADC_GND`–`D_GND` の逆並列ショットキ（`D1612`/`D1613`）で受ける
- **GND センスは新ネット `AGND_SNS`**。ルートで `J_ANA101` pin 9（`AMP_SEL_L` の隣の `A_GND` ピン）に `NT102` で 1 点だけ結び、
  `MeasureControl` に新しいシートピンで入れて INA1650 の両 ch の IN− へ
- INA1650（新 `U1612`）の **REF は `ADC_GND`**（`VCOM` ではない）、COM は 1 MΩ で `ADC_GND`、電源は ±15 V、出力は既存の鎖（`U1602` 反転＋10 µF＋`U1608`/`U1601` の VCOM 基準反転ドライバ）の入口へ。**`U1602` は残し、+IN を `A_GND` → `ADC_GND` へ固定で移す**
- ADC 側のオペアンプ（`U1612`/`U1602`/`U1601`/`U1608`）の ±15 V デカップリングは**全部 `ADC_GND` に揃える**（RC で分けた `±15V_AFE` 経由を推奨）。`U1611` だけは `A_GND` のまま
- LDO の入力は `PD_12V_SW`（シートピン `ADC_V_IN` として既に `MeasureControl` に来ている）から **新しい PPTC＋RC** を通した `PD_12V_ADC`

### 0.2 前提の照合（ユーザーの記述 vs 回路図）

| 前提 | 回路図 | 判定 | 出典 |
|---|---|---|---|
| 今の木 `ADC_GND─NT1601─A_GND─NT1603─D_GND─NT1602─PD_GND`、`GND_COIL─NT101─D_GND` | `NT1601` = `ADC_GND`/`A_GND`、`NT1602` = `PD_GND`/`D_GND`、`NT1603` = `A_GND`/`D_GND`、`NT101` = `GND_COIL`/`D_GND` | **一致** | [SF pin NT1601/NT1602/NT1603/NT101] |
| グランドを跨ぐ部品は NetTie だけ | NetTie 4 個・コネクタ（ピンごとに別ネット）・`U201`（`A_GND`/`PD_GND`、絶縁 DC-DC）だけ | **一致**（5 ノード・4 辺の木） | [SF gnd] |
| ±15 V の帰りは `A_GND`（DC-DC） | `U201`（REC20K-2415DZ）: .6=`+15V`、.5=`A_GND`、.4=`-15V`、.2=`PD_GND`、.1=`F201` の後 | **一致** | [SF pin U201]、[SF bom] |
| DC-DC は RS6-1215D（±200 mA） | **回路図の `U201` はまだ `REC20K-2415DZ`**。RS6-1215D は [NOW] の「第一候補」で未実装。±200 mA は [pow:L25] | 注記 | [SF bom]、[pow:L25] |
| ADC の LDO の上流は `F1601` | `F1601`（**T1A slow 5x20**）は `J1602`（MC の予備 12 V 端子）→`PD_12V_SW` の間。**本線の給電 `J202`→`SW402`→`PD_12V_SW` にヒューズは無く**、枝ごとに `F201`（F2A fast→`U201`）・`F202`（PPTC 0.4 A→コイル）・`F1602`（PPTC 0.5 A→`U1607`）がある | **修正**: `F1601` は J202 経由の給電の上流ではない。PD 12 V から LDO を取ると**ヒューズの無い唯一の枝**になる | [SF pin F1601/J1602/J202/SW402/F201/F202/F1602]、[SF nets PD_12V_SW] |
| ADC 枝の帰り 最大 約 87 mA | `--adc-from-pd`: LDO 入力 typ 60.9 / max 86.9 mA を PD 12 V 側へ | **一致** | [RB-pd] |
| LDO は今 `+15V` 直結 | `U1603` .8(IN)/.5(SHDN)=`+15V`、`U1606` .8(IN)=`+15V`・.5(SHDN)=`+3V3_A`、GND=.3/.6/.7=`ADC_GND` | **一致** | [SF pin U1603/U1606]、[G MC lib_symbols ピン名] |

---

## 1. 部品の棚卸し（MeasureControl の ADC 経路と周辺）

「今」は [SF pin <REF>] の出力そのもの。**「提案」は本提案の変更**（変更なしは「—」）。
デカップリングの帰属（どの IC のためのコンデンサか）は Description があるものはそれ、無いものは [G MC] の図上の近さで書いた（**図上の近さは電気的な事実ではない**。PCB で確かめること）。

### 1.1 能動部品

| 部品 | ピン → 今のネット | 提案 | 理由 |
|---|---|---|---|
| **U1611** OPA1656（計測タップの＋側バッファ、ユニティフォロワ） | .3=`AMP_SEL_L`、.1/.2=`ADC_BUF_L`、.5=`AMP_SEL_R`、.6/.7=`ADC_BUF_R`、.8=`+15V`、.4=`-15V` | **±15 V・`A_GND` 側のまま。変更なし**（`ADC_BUF_x` に INA の IN+ と `JP1602`/`JP1603` の 1 番が足されるだけ） | 本線（`AMP_SEL`）に直接触る唯一の石。入力バイアス `R1659`/`R1660` も `A_GND`。Q2 での負荷は INA の入力（同相 212.5〜287.5 kΩ [tap:L102]）だけになり、今（4.7k∥6.19k の鎖）より軽い |
| **U1612（新）** INA1650（TSSOP-14） | — | 2 節。VCC(1)=`+15V_AFE`、VEE(14)=`-15V_AFE`、IN+A(2)=`ADC_BUF_L`、IN−A(4)=`AGND_SNS`、COM A(3)→1 MΩ→`ADC_GND`、REF A(12)=`ADC_GND`、OUT A(13)=`INA_OUT_L`。B 側は IN+B(7)=`ADC_BUF_R`、IN−B(5)=`AGND_SNS`、COM B(6)→1 MΩ→`ADC_GND`、REF B(9)=`ADC_GND`、OUT B(8)=`INA_OUT_R`。VMID(IN)(11)・VMID(OUT)(10) は no_connect | ピン番号は [PDF TI_INA1650.pdf p3]。両電源なら VMID は接続不要 [PDF TI_INA1650.pdf p16 §7.3.2] |
| **U1602** OPA1656（逆相を作る反転 −1、4.7k/4.7k） | .3/.5=`A_GND`（+IN）、.2←`R1601`、.1→`C1602`、.6←`R1612`、.7→`C1626`、.8=`+15V`、.4=`-15V` | **.3/.5 を `ADC_GND` へ（固定）**。.8/.4 を `±15V_AFE` へ | Q2 では入力（INA 出力）が `ADC_GND` 基準なので、反転の基準も `ADC_GND` でないと `A_GND`–`ADC_GND` の差が差動に乗る（2.3 節の式）〔推論〕。Q1 に戻したときの差は 3.4 節 |
| **U1608** OPA1656（L の VCOM 基準反転ドライバ ×2） | .3/.5=`VCOML`、.1→`R1613`→`VINL−`、.7→`R1617`→`VINL+`、.8=`+15V`、.4=`-15V` | .8/.4 を `±15V_AFE` へ。信号側は変更なし | ADC を直接駆動する石。負荷の帰りは ADC（`ADC_GND`）なので、電源の HF ループも `ADC_GND` で閉じるべき（4 節） |
| **U1601** OPA1656（R の同上） | .3/.5=`VCOMR`、.1→`R1602`→`VINR−`、.7→`R1608`→`VINR+`、.8=`+15V`、.4=`-15V` | 同上 | 同上 |
| **A1601** ADC1804_F（PCM1804 モジュール） | .1 `VINL+`、.2 `VCOML`、.3 `VINL−`、.4 `VINR−`、.5 `VCOMR`、.6 `VINR+`、.7 `ADC_MCLK`（SCKI）、.8 `ADC_LRCK`、.9 `ADC_BCK`、.10 `ADC_DATA`、.11 `ADC_nRST`、.12 `+5V_A`、.13 `+3V3_A`、.14 `ADC_GND` | 変更なし（`ADC_GND` の島の中心） | グランドピンは .14 の 1 本だけ [SF pin A1601]。モジュール内に PCM1804 のデカップリングとジャンパが載っている旨の注記 [G MC テキスト]。マスターモード（S/M=L）の注記 [G MC テキスト] |
| **Y1601** ASFL1 12.288 MHz | .1(ST)/.4(VDD)=`+3V3_A`、.2=`ADC_GND`、.3→`R1604` | 変更なし | ADC の島で閉じる。MCLK は Pico へ行かない（`ADC_MCLK` は `A1601.7`・`R1604.2`・`TP1601.1` だけ [SF pin R1604/TP1601/A1601]） |
| **U1603** LT1763-3.3 → `+3V3_A` | .1/.2=`+3V3_A`、.3/.6/.7=`ADC_GND`、.4→`C1608`(BYP)、.5(SHDN)=`+15V`、.8(IN)=`+15V` | **.8 と .5 を `PD_12V_ADC` へ**。GND は `ADC_GND` のまま | SHDN は未使用なら VIN へ [PDF ADI_LT1763.pdf p14]。IN・SHDN の絶対最大 ±20 V [pow:L389, L391] |
| **U1606** LT1763-5 → `+5V_A` | .1/.2=`+5V_A`、.3/.6/.7=`ADC_GND`、.4→`C1623`(BYP)、.5(SHDN)=`+3V3_A`、.8(IN)=`+15V` | **.8 を `PD_12V_ADC` へ**。SHDN は `+3V3_A` のまま（3V3 先行） | PCM1804 の絶対最大「VCC − VDD < 3 V」[sc:L338]、[PDF TI_PCM1804.pdf p5] のための既存の順序。組み替えで変えない |
| **U1605** TPS3307-33 | .1=`+5V_A`、.2/.3/.8=`+3V3_A`、.4=`ADC_GND`、.5=`ADC_nRST`、.7=`ADC_nMR`、.6 NC | 変更なし | `ADC_nMR` は Pico GP15（`A1602.20`、OD）から来る境界線 [SF pin A1602/U1605] |
| U1607 BP5293-50（`+5V_D`） | .1=`PD_12V_MEAS`、.2=`D_GND`、.3=`+5V_D` | 変更なし | Pico/LCD 用。ADC 側ではない |

### 1.2 受動部品（ADC 側の電源・基準）

| 部品 | 値 | 今 | 提案 | 備考 |
|---|---|---|---|---|
| C1605 | 100nF | `+15V`/`ADC_GND` | `PD_12V_ADC`/`ADC_GND` | U1603 の IN（図上 (316,37)、U1603 (340,37) の隣）[G MC] |
| C1606 | 10uF 50V X7R | `+15V`/`ADC_GND` | 同上 | Description「LT1763 IN bulk」[G MC]。IN のバイパスは 1〜10 µF で足りる [PDF ADI_LT1763.pdf p14] |
| C1618 | 100nF | `+15V`/`ADC_GND` | `PD_12V_ADC`/`ADC_GND` | U1606 の IN |
| C1619 | 10uF 50V X7R | `+15V`/`ADC_GND` | 同上 | Description「LT1763 IN bulk」 |
| C1603 / C1604 | 10uF 10V X7R / 100nF | `+3V3_A`/`ADC_GND` | — | U1603 OUT（Description「LT1763-3.3 OUT bulk」） |
| C1608 | 10nF | U1603.4(BYP)/`ADC_GND` | — | CBYP |
| C1616 / C1617 | 10uF 16V X7R / 100nF | `+5V_A`/`ADC_GND` | — | U1606 OUT |
| C1623 | 10nF | U1606.4(BYP)/`ADC_GND` | — | CBYP |
| C1624 / C1625 | 100nF / 100nF | `+5V_A`/`ADC_GND`、`+3V3_A`/`ADC_GND` | — | Description「A701 local bypass」（旧番号のまま） |
| C1614 | 100nF | `+3V3_A`/`ADC_GND` | — | U1605 VDD |
| C1601 | 10nF | `+3V3_A`/`ADC_GND` | — | Y1601 VDD（ASFL1 DS 指定の 0.01 µF） |
| R1611 | 10k | `+3V3_A`/`ADC_nRST` | — | リセットのプルアップ |
| **C1607 / C1615** | 100nF / 100nF | `VCOML`/`ADC_GND`、`VCOMR`/`ADC_GND` | — | VCOM のバイパス（Description「VCOML/VCOMR bypass to ADC_GND」）。DS は VCOM–AGND に 0.1 µF を推奨 [PDF TI_PCM1804.pdf p29] |
| **R1602 / R1608 / R1613 / R1617** | 47 | ドライバ出力→`VINR−`/`VINR+`/`VINL−`/`VINL+` | —（6 節で値の見直しの選択肢） | DS Figure 44 の R5/R6 = 47 Ω と同じ [PDF TI_PCM1804.pdf p30] |
| R1604 | 33 | Y1601.3→`ADC_MCLK` | — | ADC の島の中 |
| TP1601 | ADC_MCLK | `ADC_MCLK` | — | 同上 |

### 1.3 受動部品（アナログ鎖）

| 部品 | 値 | 今 | 提案 |
|---|---|---|---|
| C1628 / C1613 | 10uF 25V NP | .2=`ADC_BUF_L` / `ADC_BUF_R` | **.2 を新ネット `ADC_IN_L` / `ADC_IN_R` へ**（`JP1602`/`JP1603` の 2 番） |
| R1612 / R1601 | 4.7k 0.1% | .2=`ADC_BUF_L` / `ADC_BUF_R`（U1602 反転の入力抵抗） | **.2 を `ADC_IN_L` / `ADC_IN_R` へ** |
| R1615 / R1606 | 4.7k 0.1% | U1602 帰還 | — |
| C1626 / C1602 | 10uF 25V NP | U1602 出力→ | — |
| R1618 / R1614 / R1609 / R1603 | 6.19k 0.1% | ドライバ入力 | — |
| R1619 / R1616 / R1610 / R1607 ＋ C1632 / C1627 / C1620 / C1609 | 1k 0.1% ＋ 1.8nF C0G | ドライバ帰還 | — |
| R1659 / R1660 | 100k | `AMP_SEL_L`/`AMP_SEL_R` → `A_GND` | **— （`A_GND` のまま）**。U1611 の入力バイアス（Description）。`AGND_SNS` に付けると 77 µA pk 級の信号電流がセンス線に乗る〔計算: 7.74 V/100 kΩ〕ので付けない |

鎖の利得（参考、回路図の値から）: ドライバは 1k/6.19k の反転、差動で 2×1k/6.19k = 0.323 [計算]。PCM1804 のフルスケールは差動 ±2.5 V [PDF TI_PCM1804.pdf p7] → `AMP_SEL` 換算 7.74 Vpk（5.47 Vrms）[計算]。INA1650 は利得 1 [PDF TI_INA1650.pdf p6「Gain 1 V/V」] なのでフルスケールは変わらない。

### 1.4 デカップリング（±15 V）

| 部品 | 今 | 帰属（出典） | 提案 |
|---|---|---|---|
| C1646 / C1647 | `+15V`/`A_GND`、`A_GND`/`-15V` | U1611（Description「U1611 の ±15V_A デカップリング」） | **— （`A_GND` のまま）** |
| C1636 / C1641 | `+15V`/`A_GND`、`A_GND`/`-15V` | U1602（図上 x=72.4、U1602 電源ユニット x=81.3）[G MC] | **`+15V_AFE`/`ADC_GND`、`ADC_GND`/`-15V_AFE`** |
| C1637 / C1642 | 同上 | U1601（x=104.1 / 電源ユニット x=113.0） | 同上 |
| C1638 / C1643 | 同上 | U1608（x=135.9 / 電源ユニット x=144.8） | 同上 |
| C1634 / C1639 ＋ C1635 / C1640（10uF 50V、Description「+15V_A / -15V_A」） | 同上 | 入口のバルク（x=34〜42）。注記「バルクはアナログフロントエンドの電源入口付近に」[G MC テキスト] | **`±15V_AFE`/`ADC_GND` へ（RC の出口側のバルク）** |
| 新 C1653/C1654（1 µF）＋ C1655/C1656（100 nF） | — | U1612 | `+15V_AFE`/`ADC_GND`、`ADC_GND`/`-15V_AFE`。DS は各電源ピン–グランドに 1.0 µF＋0.1 µF [PDF TI_INA1650.pdf p29] |

**±15 V に残る石と、そのデカップリングの落とし先**:
`U1611` は ±15 V・`A_GND`（本線側）。`U1612`/`U1602`/`U1601`/`U1608` は ±15 V のまま（`+5V_A` 単電源化は 6.3 の選択肢）で、デカップリングは `ADC_GND`。
理由は 4 節（負荷の帰りが `ADC_GND` にある石は、電源の HF ループも `ADC_GND` で閉じる）。

### 1.5 コネクタ・NetTie・電源入口

| 部品 | 今 | 提案 |
|---|---|---|
| **NT1601** `A_GND-ADC_GND` | .1=`ADC_GND`、.2=`A_GND` | **削除**（役目は `JP1601` の 1-2 へ） |
| NT1602 `ADC_GND_IN-D_GND` | .1=`PD_GND`、.2=`D_GND` | — （Value の `ADC_GND_IN` はシートピン名で、ネットは `PD_GND` [SF all 別名]） |
| NT1603 `A_GND-D_GND` | .1=`A_GND`、.2=`D_GND` | — |
| NT101（ルート） | `GND_COIL`/`D_GND` | — |
| **NT102（新、ルート）** | — | `A_GND`（`J_ANA101` pin 9 のパッド際）–`AGND_SNS` |
| **JP1601（新）** 1×3 ピンヘッダ＋シャント | — | 1=`A_GND`、2=`ADC_GND`、3=`D_GND` |
| **D1612 / D1613（新）** ショットキ（例: 既存の `RB160M-30` を 2 個、逆並列） | — | `ADC_GND`↔`D_GND`（シャント忘れの保険。3.3 節） |
| **J1601** AUDIO（2P） | .1=`AMP_SEL_R`、.2=`AMP_SEL_L`（**グランド極が無い**） | **3P（L / `AGND_SNS` / R）にするか外す**。MC を別基板にしてケーブルで受ける案（`J1602`/`J1603` の Description「残すか外すかは B5 のハーネス判断」）を残すなら、センスの極が要る |
| J1602 V_IN | .1=`PD_GND`、.2→`F1601` | — |
| J1603 15_V_IN | .1=`+15V`、.2=`A_GND`、.3=`-15V` | — |
| C1610 / C1611 / C1612 | `PD_12V_SW`/`PD_GND` | — （Description は旧 U1604 時代の「ADC_V_IN bulk / Return on ADC_GND_IN」のまま。ネットは `PD_12V_SW`/`PD_GND`） |

---

## 2. INA1650 の置き方

### 2.1 位置と入出力

```
AMP_SEL_L ─ U1611A(フォロワ) ─ ADC_BUF_L ─┬─ JP1602.1 ─┐
                                          └─ U1612 IN+A │        ┌─ C1628 ─ R1618 ─ U1608B ─ 47Ω ─ VINL+
AGND_SNS ────────────────────────────────── U1612 IN−A  ├─ JP1602.2 = ADC_IN_L ┤
ADC_GND ─ U1612 REF A /  COM A ─1MΩ─ ADC_GND           │        └─ R1612 ─ U1602B(−1, +IN=ADC_GND) ─ C1626 ─ R1614 ─ U1608A ─ 47Ω ─ VINL−
                     U1612 OUT A = INA_OUT_L ─ JP1602.3 ┘
```

- INA1650 の伝達は VOUT = (VIN+ − VIN−) + VREF [PDF TI_INA1650.pdf p15 Eq.1]。IN+ に `ADC_BUF`、IN− に `AGND_SNS` なので**極性は Q1 と同じ**（鎖の後段はそのまま）[計算]
- **`U1602` は残す。** PCM1804 は差動入力で、逆相脚を作るのが `U1602`（+IN が今は `A_GND` [SF pin U1602]）。INA1650 は 2 ch（[PDF p3]）で L/R に 1 ch ずつ。逆相まで INA で作るとパッケージが 2 個（IQ も倍）になる〔推論〕
- 出力負荷: `R1612` 4.7k（`U1602` の仮想接地へ）∥ `C1628`＋`R1618` 6.19k（`U1608` の仮想接地へ）≈ 2.67 kΩ [計算]。DS の表の既定負荷 RL = 2 kΩ [PDF p6]、出力振幅は 2 kΩ で＋側 350 mV・−側 430 mV までレールに寄る [PDF p7]。フルスケール 7.74 Vpk は ±15 V の内側 [計算]

### 2.2 REF は `ADC_GND`（`VCOM` にしない）

- REF は「低インピーダンスで駆動すること」[PDF TI_INA1650.pdf p3 Pin Functions]、レイアウトは「低インピーダンス・低雑音の基準点（アナロググランドや VMID(OUT)）へ最短で」[PDF p29]
- 内部は 10 kΩ ×4 の差動アンプ [PDF p15]。利得 1 で REF ピンに流れる電流は (VREF − VIN+)/20 kΩ、フルスケール 7.74 Vpk で **約 0.39 mA pk/ch** [計算]
- `VCOM` は PCM1804 の出力（2.5 V、[PDF TI_PCM1804.pdf p29]）で、**出力インピーダンスの規定値は DS に無い**（p29 は VCOM–AGND に 0.1 µF を置けとだけ言う）。ここへ 0.39 mA pk の信号電流を入れると ADC の基準そのものを揺らす〔推論〕。
  VCOM は今どおりドライバ（`U1608`/`U1601`）の +IN（電流ゼロ）だけに使う
- REF を `ADC_GND` にすると INA 出力は `ADC_GND` 基準で、鎖の AC 結合（10 µF）はそのまま要る。DC 結合化はしない

### 2.3 `U1602` の基準をなぜ `ADC_GND` へ移すか（式）

`ADC_GND` を 0、`U1602` の +IN の電位を Vr、鎖の入口を x（`ADC_GND` 基準）、ドライバの利得を k = 1k/6.19k とする。

- `U1602` 出力 = 2Vr − x。VINL+ = −k·x、VINL− = −k(2Vr − x)（AC 分）→ **差動 = −2k(x − Vr)** [計算]
- Q2 で x = INA 出力（`ADC_GND` 基準）のとき、Vr = `A_GND` の局所電位のままだと、`A_GND`–`ADC_GND` の差 Vr がそのまま差動に乗る → **Q2 の意味が消える**。Vr = `ADC_GND`（= 0）にすれば差動 = −2k·x
- Q1（x = `ADC_BUF`、`AMP_SEL` そのもの）では、Vr = `A_GND` の局所なら `A_GND`–`ADC_GND` の差は同相に落ちる（ここは否定側査読 `review/tap_compare_review.md` §2.1 の表と同じ結論）。Q1 での扱いは 3.4 節

### 2.4 電源と IQ

- ±15 V（DS の推奨 4.5（±2.25）〜36（±18）V の内側 [tap:L90]、[PDF p5]）。**表の性能値（CMRR 85/91 dB など）は VS = ±18 V 条件** [tap:L97]。±15 V での CMRR の規定値は無い
- IQ（INA1650、IOUT = 0）: 8 / 10.5 / 12 mA（MIN/TYP/MAX）、全温度 max 14 mA [tap:L106]、[PDF p7]。両電源なので V+ から V− へ流れ、グランドには流れない〔推論〕
- 供給は `±15V_AFE`（4 節の RC の出口）

### 2.5 同相入力範囲 vs この回路が INA に見せる電圧

| 項目 | 値 | 出典 |
|---|---|---|
| 規定の同相範囲 | (V−)+0.25 〜 (V+)−2 V → ±15 V で **−14.75 〜 +13 V** | [PDF TI_INA1650.pdf p6]、[計算]。本文 §8.1.1 は下側を「負電源から 350 mV」と書いていて表（0.25 V）と食い違う [PDF p18] — 安全側の 0.35 V でも −14.65 V |
| 入力の絶対最大 | (V−)−0.5 〜 (V+)+0.5 V、±10 mA | [PDF p5] |
| IN+（`ADC_BUF`） | ADC フルスケール 7.74 Vpk。過大入力でも `U1611` は ±15 V 上なので絶対最大の内側 | [計算]、〔推論〕 |
| IN−（`AGND_SNS`）と REF の差 = グランドのずれ | **mV 級**（NetTie 間の IR 降下）〔推論〕。実測は無い | — |
| 同相分 | ≈ (IN+ + IN−)/2 ≈ 信号の半分 ＋ グランドのずれ | [計算] |

**グランドのずれは同相範囲に対して 3 桁以上小さい。** 範囲で詰まるのは信号の上側だけで、`AMP_SEL` が +13 V を超えるほど振れたとき（ADC はとうにクリップしている）。
しかも INA は `U1611` の後ろなので、INA 側で何が起きても `AMP_SEL`（本線）には返らない〔推論〕。

### 2.6 COM ピン

- COM は内部の 500 kΩ ×2（入力バッファのバイアス）の中点 [PDF p15, p16]。両電源では「グランドへ」[PDF p16]
- COM と「システムのグランド」の間に RCOM = 1 MΩ を入れると、20 Ω の信号源不整合での CMRR が 83.7 dB → 89.6 dB [tap:L101]、[PDF p18]。両電源＋AC 結合では立ち上がり時間を延ばさない [PDF p19]
- **提案: COM A/B それぞれ 1 MΩ（新 R1624/R1625）で `ADC_GND` へ。** センス線が切れても IN− は 500k＋1M で `ADC_GND` に引かれ、Q1 相当の片側測定に落ちるだけ（壊れない）〔推論〕
- この経路（`AGND_SNS`–500 kΩ–COM–1 MΩ–`ADC_GND`）は `A_GND` と `ADC_GND` の間の**高インピーダンスの第 2 経路**（1.5 MΩ）。グランドのずれ mV なら nA [計算]。NetTie の意味での閉路ではない

---

## 3. NetTie の木（Q2 / Q1）と、ジャンパで壊れないこと

### 3.1 Q2（既定、`JP1601` = 2-3）

| 辺 | 結ぶもの |
|---|---|
| NT101 | `GND_COIL`–`D_GND` |
| NT1602 | `PD_GND`–`D_GND` |
| NT1603 | `A_GND`–`D_GND` |
| **JP1601 2-3** | `ADC_GND`–`D_GND` |
| **NT102** | `A_GND`–`AGND_SNS` |

ノード 6（`A_GND` `D_GND` `PD_GND` `ADC_GND` `GND_COIL` `AGND_SNS`）、辺 5、全部つながる → **木（閉路なし）**。
`ADC_GND` と `AGND_SNS` はどちらも**葉**（辺が 1 本）なので、よその電流が通らない。

ADC の 12 V 枝の電流の経路: `PD_12V_SW`→F1604→R1621→`PD_12V_ADC`→LDO→ADC→`ADC_GND`→**JP1601**→`D_GND`→**NT1602**→`PD_GND`→`J202`。
**`A_GND` を通らない。** 今（`+15V` から）は `ADC_GND`→`NT1601`→`A_GND`→`U201.5` で、PCB の親ラフの座標では `NT1601`（86.8, 68.6）から `U201`（334.4, 41.4）まで `A_GND` の面を横切る [PCB]。

**`D_GND` に付けるか `PD_GND` に付けるか**（どちらでも木で、`A_GND` を通らない）:

| | `ADC_GND`–`D_GND`（推奨） | `ADC_GND`–`PD_GND` |
|---|---|---|
| I²S（ADC→Pico、Pico は `D_GND` [SF pin A1602]）の帰り | **1 ホップ**（今は `NT1601`→`A_GND`→`NT1603` の 2 ホップ） | 2 ホップ（`NT1602` 経由） |
| ADC の 87 mA の帰り | `D_GND` の短い区間（JP1601→NT1602）を通る | `PD_GND` へ直行 |
| `ADC_GND` の電位が乗るもの | `D_GND` の雑音（Pico/LCD、`NT101` 経由のコイル枝） | `PD_GND` の雑音 |
| Q2 での効き | どちらも INA の同相として除去（85 dB min @±18 V [tap:L97]） | 同じ |

〔推論〕 3 つの NetTie（NT1602・NT1603）と JP1601 を**1 か所に寄せる**なら差は小さい。I²S の帰りが短くなる `D_GND` を推奨する。

### 3.2 Q1（戻し、`JP1601` = 2-1）

| 辺 | 結ぶもの |
|---|---|
| NT101 / NT1602 / NT1603 / NT102 | 同上 |
| **JP1601 2-1** | `ADC_GND`–`A_GND` |

ノード 6・辺 5 → 木。今の図（`NT1601`）と同じ位相。
**違い**: LDO が PD 12 V なので、ADC の帰りは `ADC_GND`→JP1601→`A_GND`→NT1603→`D_GND`→NT1602→`PD_GND` になり、**JP1601 の 1 番と NT1603 の間の `A_GND` を横切る**。
Q1 は戻し用なので飲むとして、**JP1601 と NT1603 を隣接させ、その間の `A_GND` を短い島（音声の `A_GND` 面へは 1 点）にする**と、横切るのはその島だけになる〔推論・PCB〕。
（DECISIONS も「PCB では `NT1601` と `NT1603` を隣に置く」と書いている [DEC:222]。**今の親ラフでは `NT1601`（86.8, 68.6）・`NT1602`（181.8, 297.0）・`NT1603`（286.0, 440.0）で、離れている** [PCB]）

### 3.3 ジャンパの組み合わせで閉路・浮きが起きないこと

**グランドを選ぶのは `JP1601` の 1 個だけにする**（信号の切り替え `JP1602`/`JP1603` はグランドを選ばない。`U1602` の基準も切り替えない ← 2.3 / 3.4）。

| JP1601 の状態 | 結果 | 対策 |
|---|---|---|
| 2-3（Q2） | 木 | — |
| 2-1（Q1） | 木 | — |
| **1-2 と 2-3 を両方** | `ADC_GND`–`A_GND` と `ADC_GND`–`D_GND` が同時 → `NT1603` と並列の閉路 | **1×3 ピンヘッダ＋シャント 1 個なら物理的に起きない**（2 番ピンを 2 個のシャントが共有できない）〔推論〕。3 パッドのはんだジャンパだと起きうる |
| **どちらも無し** | `ADC_GND` が浮く。ADC の 87 mA が行き場を失い、I²S 出力ピンや INA の REF の ESD ダイオード経由で帰る〔推論〕 | **`D1612`/`D1613`（逆並列ショットキ、`ADC_GND`↔`D_GND`）**で浮きを 1 V 未満に抑え、87 mA を受ける。ダイオードは 87 mA を連続で流せる品（例: 既存 BOM の `RB160M-30` [SF bom]。DS はリポジトリに無いので定格は要確認） |

**ダイオードは Q1 のときに第 2 経路になるか**: Q1 では `ADC_GND`–`D_GND` のずれ ＝ JP1601＋`A_GND` の島＋NT1603 の IR 降下（87 mA × 数十 mΩ で数 mV 〔推論〕）。ショットキはこの電圧ではほぼ切れていて、流れるのは µA 級〔推論。リーク電流の DS 値なし〕。NetTie の意味の閉路ではない。
**Q2 では**ダイオードは JP1601 と並列（両端が同電位）で何もしない。

**信号の選択子 `JP1602` / `JP1603`**（1=`ADC_BUF_x`、2=`ADC_IN_x`、3=`INA_OUT_x`）も 1×3 ヘッダ＋シャントを推奨:

- 両方同時だと `U1611` の出力と INA の出力がぶつかる。`U1611` が電流制限に入ると帰還を失い、その入力（＝本線 `AMP_SEL`）の振る舞いが保証できない〔推論〕。**本線に触る唯一の失敗モードなので、グランドと同じく機械的に排他にする**
- 選び忘れ（シャント無し）は鎖の入口が浮くだけ（ADC 経路が止まる。本線に害なし）〔推論〕

**混在（グランドは Q2・信号は Q1、など）**: どれも木のまま。性能が落ちるだけ（例: 信号 Q1＋グランド Q2 だと `A_GND`–`ADC_GND` の差が `D_GND` の雑音込みで差動に乗る。2.3 の式）。壊れる組み合わせは無い〔推論〕。

一括で切り替えたいなら 3 回路のスライドスイッチ（ブレーク・ビフォア・メーク）で JP1601〜1603 を 1 個にまとめる手もある（「両方」も「無し」も電源断中の遷移だけ）〔推論〕。

### 3.4 Q1 の再現度（`U1602` の基準を `ADC_GND` に固定した場合）

今の Q1 は `U1602` の +IN が `A_GND` で、`A_GND`–`ADC_GND` の差 Vg は同相に落ちる（2.3）。
提案では +IN を `ADC_GND` に固定するので、Q1 に戻すと **Vg が差動に乗る**。ただし Q1 では `ADC_GND` と `A_GND` は JP1601（1-2）で直結なので、Vg は JP1601 自身と周りの銅箔の降下だけ（DC は 10 µF で切れる。残るのは ADC の電源電流の AC 分 × mΩ）〔推論〕。
一方、Q1 の支配的な誤差「ch 側グランド ↔ MC 側 `A_GND`」は、今の図でも 0 dB（信号と直列）[`review/tap_compare_review.md` §2.1]。**この固定で Q1 に足される誤差は、もともと Q1 にある誤差より小さい**〔推論〕。
それでも今の Q1 と厳密に同じにしたいなら、`U1602` の +IN も 1×3 ヘッダ（`A_GND`/`ADC_GND`）で選ぶ。ただしこれは **2 個目のグランド選択子**になり、JP1601 と食い違うと（例: JP1601=Q2 で `U1602`=`A_GND`）性能が落ちる（閉路にはならない。+IN に電流は流れない）。推奨はしない。

---

## 4. ±15 V のオペアンプの電流はどこを流れるか

前提（事実）: ±15 V の帰りは `U201.5` = `A_GND` [SF pin U201]。ADC 側の石（`U1612`/`U1602`/`U1601`/`U1608`）の出力の基準は `ADC_GND` 側（REF・VCOM・+IN）。

| 電流 | 大きさ | 経路（Q2） | `A_GND`↔`ADC_GND` を跨ぐか |
|---|---|---|---|
| 静止電流 | INA 10.5 typ / 12 max mA [tap:L106]、OPA1656 3.9 / 4.6 mA per ch [op:L127] | `+15V`→石→`-15V`（両電源） | **跨がない**（正負の電流が等しい限りグランドに流れない）〔推論〕 |
| INA の REF ピン電流 | 約 0.39 mA pk/ch（フルスケール）[計算、2.2] | `+15V`/`-15V`（`A_GND` 基準）→INA 出力段→内部 10k→REF→`ADC_GND` | **跨ぐ**: `ADC_GND`→JP1601→`D_GND`→NT1603→`A_GND`→`U201.5` |
| ドライバ→ADC 入力 | PCM1804 入力 10 kΩ（片側）[PDF TI_PCM1804.pdf p7]、1.25 Vpk/ピン（フルスケール）→ 0.125 mA pk/ピン [計算] | 同上→`VINx±`→ADC 内部→`ADC_GND` | VIN+ と VIN− は逆相なので大半は ADC の中で打ち消す。残り（不整合分）が跨ぐ〔推論〕 |
| 鎖の中の帰還・入力抵抗の電流（数 mA pk） | 例: 7.74 V/4.7k + 7.74 V/6.19k ≈ 2.9 mA pk/ch [計算] | オペアンプの出力 → 抵抗 → 別のオペアンプの出力（仮想接地）→ 電源ピン | グランドに入らない（出力どうしでレール経由で閉じる）〔推論〕 |
| ADC のスイッチトキャパシタ入力のキックバック（MHz 帯） | DS に数値なし | ADC→`ADC_GND`→ドライバのデカップリング→ドライバ電源ピン→出力→VIN | **デカップリングが `A_GND` なら跨ぐ**。`ADC_GND` なら島の中で閉じる |
| DC-DC のリップル電流 | RS6 は内部動作周波数 min 200 kHz [pow:L45]。リップル＆ノイズ 50 / 75 mVp-p（typ / max、1 µF MLCC 条件）[pow:L47] | `+15V`→デカップリング→そのグランド→…→`U201.5` | デカップリングが `ADC_GND` なら跨ぐ（→ RC で絞る） |

**結論〔推論〕**:

1. オーディオ帯の電流は、デカップリングをどちらに置いても DC-DC から来るので、跨ぐ量は変わらない（サブ mA、信号相関）。今（ADC の 60〜87 mA が全部 `NT1601`→`A_GND` を通る）より 2 桁小さい
2. HF（ADC のキックバック）は、**ドライバのデカップリングを `ADC_GND` に置けば島の中で閉じる**。`A_GND` に置くと MHz 帯の電流が `A_GND` の面（NT1603 から先）へ出る。本線を汚さない方向は `ADC_GND`
3. その代わり DC-DC のリップル電流が `ADC_GND` のコンデンサを通って跨ぐ。**`+15V`→R1622→`+15V_AFE`、`-15V`→R1623→`-15V_AFE` の直列抵抗（例 4.7 Ω、値は未決）**で絞る。
   4.7 Ω なら ADC 側 4 石の IQ 合計 max 39.6 mA/レール（INA 12 ＋ OPA1656 3 個 × 9.2 [RB の表]）で降下 0.19 V [計算]、C1635/C1640（10 µF）と組んで角 3.4 kHz、200 kHz で約 35 dB（理想）[計算]。フェライトビーズでもよい
4. `U1611` は `A_GND` デカップリングのまま（入力も負荷も `A_GND` 側。Q2 での負荷は INA 入力の µA 級）
5. 一貫性: **「負荷の帰りがどの島にあるか」で落とし先を決める**。ADC 側 4 石 → `ADC_GND`、`U1611` → `A_GND`。1 個の石の V+ と V− を別の島に落とさない

---

## 5. GND センス線

### 5.1 `AMP_SEL` はどこで作られ、何を基準にしているか

- `AMP_SEL_L` のピン: `U311`/`U312`（TMUX7612 の D）、`K301`〜`K304` の .7（リレー）、`J_ANA301`/`J_ANA302`/`J_ANA101` の .7、`J_PNL_A1601_1`/`J_PNL_A1602_1`（FrontPanel へ）、`SW501`（DEST）、`J_RAIL501.1`、`J1601.2`、`R1659`、`U1611.3` [SF nets AMP_SEL_L]
- 作っているのは娘（`AmpBankSwitch` の TMUX、`AmpBankRelay` のリレー）。その手前の AmpChannel の出力は 2.2 µF の後に 220 kΩ で `A_GND`（例 `C601`/`R603`、`C1001`→`R1003`）[SF pin R603/C601/R1003]
- 娘 → 母板は `J_ANA101`（2×5）: .7=`AMP_SEL_L`、.10=`AMP_SEL_R`、.1/.2/.4/.5/.8/.9=`A_GND`、.3/.6=`TONE_L/R` [SF pin J_ANA101]。娘側の `J_ANA301` も同じ並び [SF pin J_ANA301]
- 2×5 の奇数列（1,3,5,7,9）と偶数列（2,4,6,8,10）で、**.9 は `AMP_SEL_L`（.7）の隣、.8 は `AMP_SEL_R`（.10）の隣**（ピン配置からの読み）〔推論: `Conn_02x05_Odd_Even` の番号付けから〕
- `J_RAIL501`（ルート、3P）: .1=`AMP_SEL_L`、.2=`A_GND`、.3=`AMP_SEL_R`。Description「選択された Amp 出力の取り出し端子…DEST スイッチの手前…A_GND 極を持つ唯一の音声取り出し口」[G root]。親ラフで (15, 264)、`J_ANA101` は (222.4, 97.8) [PCB]

### 5.2 どこで拾うか

**提案: `J_ANA101` pin 9 のパッド際に `NT102`（`A_GND`–`AGND_SNS`）。** 1 本のセンスを L/R で共有（INA の IN−A・IN−B を両方 `AGND_SNS`）。

| 候補 | 良い点 | 悪い点 |
|---|---|---|
| **`J_ANA101` pin 9（または 8）** | `AMP_SEL` と同じコネクタ・隣のピンで娘から入ってくるグランド。娘を差し替えても（Switch/Relay）同じ点 | 娘の中の ch ごとのグランド差（4 ch のどれを選んだか）は残る。コネクタ接点の降下（`A_GND` ピンは娘の戻り電流も運ぶ）も含む〔推論〕 |
| `J_RAIL501` pin 2 | 外部で測るときの基準と同じ | 源（娘）ではなく母板の出口。`J_ANA101` から遠い [PCB] |
| 娘の中（TMUX の D の足元） | 源に一番近い | `J_ANA` に専用ピンが要る → 生成シート（`build_daughter.py`）と両版の娘を変える。今回はやらない |

**⚠ センスの NetTie は 1 個だけ。** 2 か所で `A_GND` に結ぶと、センス線が `A_GND` の並列経路になり、主電流が流れる（センスでなくなる）。場所を変えるときは「移す」であって「足す」ではない。

### 5.3 シートを跨ぐ経路

- `AGND_SNS` はルートで生まれて `MeasureControl` へ入る → **新しい階層ラベル `AGND_SNS`（MC 側、input）と、ルートの MC シートシンボルに同名のシートピン**が要る。今の MC のシートピンは `+15V_A` `-15V_A` `ADC_GND_IN` `ADC_V_IN` `AUDIO_L_IN` `AUDIO_R_IN` `A_GND` `I2C_SDA` `I2C_SCL` `3V3` `D_GND` `+5V_D` ほか LCD/TP/ENC 系 [G root シートピン一覧] で、`AGND_SNS` に当たるものは無い
- 片方だけ足すと `hier_label_mismatch`（CLAUDE.md）。足したら `sch_facts.py iface` で 0 件を確かめる
- **12 V と `PD_GND`/`D_GND` はシートピンが既にある**（`ADC_V_IN`＝`PD_12V_SW`、`ADC_GND_IN`＝`PD_GND`、`D_GND`）[SF all 別名]。電源側の組み替えに新しいシートピンは要らない
- 物理: `MeasureControl` は母板の上（[NOW] の PCB ゾーン）。コネクタは要らない。`J1601`（予備のケーブル受け、2P）を使う構成を残すなら 3P にしてセンスの極を足す（1.5）

### 5.4 バッファは要るか、電流はいくらか

- INA1650 の入力は内部でバッファされている（入力バッファ＋500 kΩ のバイアス、[PDF TI_INA1650.pdf p16 Figure 39 と本文]）。**外付けのバッファは不要**〔推論〕。足すとそのオペアンプ自身の基準・雑音・オフセットが IN− に乗る
- CMRR と信号源不整合: 20 Ω 不整合で 84 dB typ [tap:L99]、RCOM 1 MΩ なら 89.6 dB [tap:L101]。IN+ の源は `U1611` の出力（閉ループで ≪1 Ω〔推論〕）、IN− の源はセンス線の銅箔＋NetTie（サブ Ω〜1 Ω 級〔推論〕）。**不整合は 20 Ω より 1 桁以上小さい** → DS の typ 付近〔推論〕
- センス線の電流: IN− のバイアス電流（**DS の表に規定値が見つからなかった**）＋ 500 kΩ＋RCOM 1 MΩ を通る (Vg)/1.5 MΩ。Vg が mV なら **nA 級** [計算]。2 ch で倍でも µA に届かない。センス線の抵抗 1 Ω でも降下は nV〜µV [計算] → 細線でよい
- 引き回し〔推論・PCB〕: `J_ANA101` から MC へ、`AMP_SEL_L`–`AGND_SNS`–`AMP_SEL_R` の 3 本を並べて（ループ面積を小さく）、INA の近くで IN− へ。保護・EMI 用の直列抵抗を入れるなら IN+ と IN− に同じ値（0.1 %）を対で入れる（片側だけだと不整合になる）

---

## 6. 保護と電源の順序

### 6.1 ADC 枝の PPTC

- 本線の給電 `J202`→`SW402`→`PD_12V_SW` にはヒューズが無く、既存の枝は全部自分の保護を持つ（`F201` F2A fast、`F202` PPTC 0.4 A、`F1602` PPTC 0.5 A）[SF pin/bom]。`F1601`（T1A slow）は `J1602` の予備入口専用（0.2）
- LT1763 の電流制限は **min 520 mA**（全温度）[PDF ADI_LT1763.pdf p6]。出力短絡時に 12 V 側から 0.52 A 以上をサーマルで間欠的に引く〔推論〕。この電流は `U201` と同じ `PD_12V_SW` から来るので、PD 源が弱ければ ±15 V まで巻き込む〔推論〕
- **[DEC:226–250]「ADC 枝の PPTC は戻さない（2026-09-07）」の前提は、LDO が `+15V`（`REC20K` の SCP の後ろ）にあること**だった（同節の表の 3 行目は「`REC20K` の SCP → ヒカップ・自動復帰」）。PD 12 V 直結ではこの前提が成り立たない。**判断はユーザー**。提案は新 `F1604`（PPTC）を `PD_12V_SW` と R1621 の間に
- 定格: 枝の max 86.9 mA [RB-pd]。[DEC:1377] の記録は「LDO を 12 V から取るなら 0.15 A → 0.25 A、60 ℃ で 0.15 A 品の hold 105 mA」— **この温度ディレーティングは PPTC の DS がリポジトリに無く、未照合**。hold 0.25 A 級（RXEF 系の一段上）を候補とし、DS を取ってから確定

### 6.2 LDO の前の RC / LC

- LT1763 の入力リップル除去（グラフ、COUT 10 µF・IL 500 mA）: 100 kHz 約 37〜41 dB、**200 kHz 約 28〜32 dB**、1 MHz 約 21〜22 dB [pow:L414]
- `PD_12V_SW` には `U201`（DC-DC）の入力が載っている [SF nets PD_12V_SW]。RS6 の内部動作周波数は min 200 kHz [pow:L45]
- **提案: `PD_12V_SW`→F1604→`PD_12V_ADCP`→R1621（例 3.3 Ω）→`PD_12V_ADC`、C1651（47 µF）＋C1652（100 nF）を `PD_12V_ADC`–`PD_GND`**。LDO 足元の C1605/C1606/C1618/C1619 は `PD_12V_ADC`–`ADC_GND`
  - 数値〔計算〕: 降下 86.9 mA × 3.3 Ω = 0.29 V、損失 25 mW。角 1/(2π·3.3 Ω·57 µF) ≈ 0.85 kHz、200 kHz で理想 47 dB（電解の ESR で頭打ち。10 µF MLCC 級を並べれば 200 kHz で約 30 dB は残る〔推論〕）＋ LDO の 28〜32 dB
  - **フィルタのコンデンサの帰りは `PD_GND`**: `U201` のリップル電流を PD 側で閉じ、`ADC_GND`（→JP1601→`D_GND`→NT1602）へ回さない〔推論〕。U1607 の CIN の Description が同じ理屈（「PD_GND に落とすと入力の脈流ループが NT1602 を通ってしまう」の逆向き）[G MC C1645]
  - LC にしないのは、減衰がコンデンサの ESR と共振のダンピングで決まり、RC のほうが 87 mA では損失なく素直だから〔推論〕
  - `PD_12V_ADC` はパッシブ（R）の後なので、LT1763 の IN（power in）のために **PWR_FLAG が要る**〔推論: KiCad ERC の規則〕
- **COUT/ESR の安定域**（組み替えとは独立だが、入力を変えるついでに確認）: CBYP ≥ 1000 pF なら COUT 6.8 µF 以上、ESR 3 Ω 以下 [pow:L419–420]、[PDF ADI_LT1763.pdf p16]。ここの CBYP は 10 nF（C1608/C1623 [SF pin]）。COUT は `+3V3_A` が 10 µF **10 V** X7R（C1603）、`+5V_A` が 10 µF **16 V** X7R（C1616）[SF bom]。DS 自身が「16 V・10 µF の Y5V は 5 V で 1〜2 µF まで落ちうる」と書いている [pow:L420]。**X7R の DC バイアス後の実効容量が 6.8 µF を切らないかは部品の特性表で確かめること**（DS 値なし）
- 12 V 入力での LDO 損失: `U1603` (12−3.3) V × 35 mA ≈ 0.30 W、`U1606` (12−5) V × 45 mA ≈ 0.32 W、S8 の θJA 70 °C/W で +21〜22 °C [計算、pow:L416、負荷は [RB] の出典行（PCM1804 VCC 45 / VDD 20、発振器 15 mA max）]。`+15V` 入力時の記録 0.41 / 0.45 W [DEC] より下がる

### 6.3 PCM1804 のアナログ入力の絶対最大 vs ドライバ

- 絶対最大: VINx±・VCOMx・VREFx は **−0.3 V 〜 VCC+0.3 V**、ピン電流 **±10 mA** [PDF TI_PCM1804.pdf p5]（この行は `ds_facts` に無いので PDF から直接）
- **ADC を直接駆動するのは INA1650 ではなく `U1608`/`U1601`**（INA → `U1602`/10 µF → ドライバ → 47 Ω → VIN）[SF pin]。ドライバは ±15 V
- ドライバの +IN は VCOM（ADC の出力）。**ADC の電源が無い／立ち上がり中は VCOM ≈ 0 V**〔推論〕なので、ドライバ出力は 0 V を中心に信号 ±1.25 Vpk（フルスケール）で振れる [計算]
- VIN ピンのクランプ（VCC 側・GND 側の ESD）で受けると、47 Ω で制限される電流は (1.25 − 約 0.5) V / 47 Ω ≈ **16 mA pk** [計算。ダイオードの 0.5 V は仮定] → **±10 mA を超える**。過大入力（`AMP_SEL` ±13 V → ドライバ ±2.1 V）なら約 34 mA [計算]
- **組み替えで新しく起きるのは「±15 V はあるが ADC の電源が無い」状態**: 今は LDO が `+15V` から取るので、±15 V と ADC 電源は一緒に来る。PD 12 V から取ると、`F1604` が切れた・LDO が落ちた・PD が 12 V 以外を出した、などで起きる〔推論〕。起動時の順序も保証されない（RS6 の起動 2 ms typ [pow:L38]、LT1763 の起動は CBYP に比例する旨の本文のみ）
- 逆（ADC の電源はあるが ±15 V が無い）も新しく起きる: `F201` 断・`U201` 故障・**PD が 5 V を出したとき**（CH224K モジュールは 5/9/12/15/20 V をジャンパで選ぶ [`datasheets/StrawberryLinux_50224_CH224K.md`、メーカー記載]。RS6 は 9〜18 V [pow:L23] なので止まるが、LT1763 の `+3V3_A` は 5 V 入力でも出る〔推論〕）。このとき VCOM 2.5 V が無電源のドライバの +IN の ESD ダイオードへ流れる。OPA1656 の入力の絶対最大は (V−)−0.5〜(V+)+0.5 V・±10 mA [op:L135]
- ⚠ PD を 20 V にジャンパすると LT1763 の IN は絶対最大 ±20 V [pow:L389] ちょうど、RS6 は入力範囲外 [pow:L23]。これは `U201` 側も同じ事故

**対策の選択肢**（どれも未決）:

| 案 | 中身 | 得 | 損 |
|---|---|---|---|
| (a) 直列抵抗を上げる | 47 Ω → 100〜220 Ω | フルスケールの信号なら 10 mA 未満に〔計算: 0.75 V/100 Ω = 7.5 mA〕 | DS の推奨回路は 47 Ω（R5/R6「低インピーダンス駆動と雑音除去」[PDF p29–30]）。ADC 入力 10 kΩ と分圧で −0.1〜−0.2 dB〔計算〕。過大入力は守れない |
| (b) ドライバ（`U1608`/`U1601`）を `+5V_A`/`ADC_GND` の単電源にする | ドライバの出力が ADC の電源レールを超えられなくなる（構造的） | ±15 V の負荷が各レール max 18.4 mA 減る [RB の OPA1656 行 × 2] | `+5V_A` の負荷が同じだけ増え（PD 側 86.9 → 約 105 mA〔計算〕）、ADC の VCC にドライバの信号電流が乗る。OPA1656 の同相範囲 (V−)〜(V+)−2.25 V [op:L134] は 5 V で 0〜2.75 V、VCOM 2.5 V は余裕 0.25 V。出力振幅は 2 kΩ で (V−)+0.25〜(V+)−0.25 V [op:L128]、ここの負荷は約 0.9 kΩ（帰還 1k ∥ ADC 10k）でもっと狭いはず〔推論〕 |
| (c) 事故の窓だけと割り切る | 何もしない | 部品が増えない | `F1604` が切れた状態で音を出し続けると ADC の入力に 10 mA 超が流れ続ける〔推論〕 |
| (d) VCOM とドライバ +IN の間に 1 kΩ | 「ADC はあるが ±15 V が無い」側の電流を 2.5 mA に制限〔計算〕 | 部品 2 個 | +IN の雑音が増えるが L/R の 2 石とも同じ VCOM を見るので同相（除去される）〔推論〕 |

〔推論〕 本線への影響はどの案でも無い（ADC 入力で何が起きても `U1611` で止まる）。優先は ADC を壊さないこと。**(a) のフットプリント（値を後で上げられる）＋(d) を推奨**、(b) は ±15 V を削りたいときの選択肢として残す。

### 6.4 Pico への I²S が `ADC_GND` とグランドを共有すること

- 境界を渡る線: `ADC_DATA`・`ADC_BCK`・`ADC_LRCK`（`A1601`→`A1602` の GP0/GP1/GP2）、`ADC_nMR`（Pico GP15 → `U1605.7`）。`ADC_nRST`・`ADC_MCLK` は ADC 側で閉じる [SF pin A1601/A1602/U1605/R1604]
- ADC はマスター（「S/M=L…ADCマスタ 48k/256fs」の注記 [G MC テキスト]）→ BCK/LRCK/DATA は ADC の出力で、Pico は受けるだけ。Q2 の木（JP1601 2-3）で帰りは **`ADC_GND`→JP1601→`D_GND` の 1 ホップ**（今は 2 ホップ）
- `D_GND` の雑音は `ADC_GND` 全体を一緒に動かす（葉なので島の中に電位差は作らない）。INA から見れば同相 → 除去〔推論〕
- **ADC の電源が落ちて Pico が生きている**とき（USB だけ挿したときもこれ。`D1601` の注記「USB だけ挿すと Pico は動き LCD は消える」[G MC テキスト]）: GP0〜2 を入力で、内部プルアップ無しにしておけば ADC へ電流を押し込まない〔推論。RP2350 の既定のパッド状態は ds_facts に無い → ファームで確認〕。BCK/LRCK/DATA の絶対最大は −0.3〜VDD+0.3 V [PDF TI_PCM1804.pdf p5]
- 保険: `ADC_DATA`/`ADC_BCK`/`ADC_LRCK` に ADC 側で直列抵抗のフットプリント（0 Ω 既定、必要なら 330 Ω で 3.3 V/330 Ω = 10 mA に制限〔計算〕）。DS のデジタル出力負荷は max 10 pF [PDF p5]、330 Ω × 15 pF ≈ 5 ns で BCK 3.072 MHz の半周期 163 ns に対して小さい〔計算。BCK = 64 fS は `review/tap_compare_review.md` 1-4 の DS p23 読み〕。ネット名は分ける（例 `ADC_BCK` / `ADC_BCK_P`）
- `ADC_nMR` は Pico 側がオープンドレイン（「H は駆動しない」[G MC テキスト]）なので、ADC 側の電源が無くても押し込まない

---

## 7. 回路図の変更一覧と、残る決定

### 7.1 変更（回路図の言葉で）

**`MeasureControl.kicad_sch`（手編集可のシート）**

| # | 種類 | 中身 |
|---|---|---|
| M1 | 削除 | `NT1601`（`ADC_GND`–`A_GND`） |
| M2 | 追加 | `JP1601` 1×3 ヘッダ（1=`A_GND`、2=`ADC_GND`、3=`D_GND`）。シルクに Q1/Q2 |
| M3 | 追加 | `D1612`/`D1613` 逆並列ショットキ `ADC_GND`↔`D_GND` |
| M4 | 追加 | `U1612` INA1650（シンボルと TSSOP-14 FP を用意）。ピンは 1.1 表 |
| M5 | 追加 | `R1624`/`R1625` 1 MΩ（COM A/B → `ADC_GND`）。`U1612` の 10/11 に no_connect |
| M6 | 追加 | `C1653`/`C1654` 1 µF、`C1655`/`C1656` 100 nF（`U1612` の ±15V_AFE → `ADC_GND`） |
| M7 | 新ネット・分割 | `ADC_IN_L`（`C1628.2`・`R1612.2`）、`ADC_IN_R`（`C1613.2`・`R1601.2`）、`INA_OUT_L`/`INA_OUT_R`、`AGND_SNS` |
| M8 | 追加 | `JP1602`/`JP1603` 1×3 ヘッダ（1=`ADC_BUF_x`、2=`ADC_IN_x`、3=`INA_OUT_x`） |
| M9 | ネット変更 | `U1602.3`/`.5`：`A_GND` → `ADC_GND` |
| M10 | 追加・ネット変更 | `R1622`（`+15V`→`+15V_AFE`）、`R1623`（`-15V`→`-15V_AFE`）、PWR_FLAG ×2。`U1602`/`U1601`/`U1608` の .8→`+15V_AFE`・.4→`-15V_AFE`。C1634〜C1643 の `A_GND` 側 → `ADC_GND`、`+15V`/`-15V` 側 → `±15V_AFE` |
| M11 | そのまま | `U1611`・`C1646`/`C1647`・`R1659`/`R1660`（`A_GND`） |
| M12 | 追加・ネット変更 | `F1604`（PPTC、`PD_12V_SW`→`PD_12V_ADCP`）、`R1621`（`PD_12V_ADCP`→`PD_12V_ADC`）、`C1651`/`C1652`（`PD_12V_ADC`/`PD_GND`）、PWR_FLAG。`U1603.8`・`U1603.5`・`U1606.8`・`C1605/C1606/C1618/C1619` の `+15V` 側 → `PD_12V_ADC` |
| M13 | 追加 | 階層ラベル `AGND_SNS`（input） |
| M14 | 任意 | `ADC_DATA`/`ADC_BCK`/`ADC_LRCK` の直列抵抗（0 Ω）、VCOM–ドライバ +IN の 1 kΩ（`U1608.3/.5`、`U1601.3/.5` 側を新ネットに） |
| M15 | 任意 | `J1601` を 3P（`AMP_SEL_L`/`AGND_SNS`/`AMP_SEL_R`）に、または削除 |
| M16 | 注記の更新 | GND の注記（「NT1601=A_GND─ADC_GND（A1601 近傍・アナログ星点）…」）と電源系の注記（「+15V ─ U1603…」）が古くなる [G MC テキスト] |

**`AudioV2Case.kicad_sch`（ルート、手編集所有）**

| # | 種類 | 中身 |
|---|---|---|
| R1 | 追加 | `NT102`（`A_GND`–`AGND_SNS`）を `J_ANA101` pin 9 のそば |
| R2 | 追加 | MC シートシンボルにシートピン `AGND_SNS` |

**娘シート（生成物）は変えない。** `build_*` スクリプトも変えない。

### 7.2 検証（実装したとき）

- `python3 Audio/scripts/check_sexpr.py -q AudioV2.1`（CLAUDE.md の手順。v2.1 を対象に）
- `python3 AudioV2.1/scripts/sch_facts.py iface`（シートピンの不一致 0）、`pin U1612`、`nets --net ADC_GND` / `AGND_SNS` / `PD_12V_ADC`
- `kicad-run.sh erc AudioV2.1/AudioV2Case.kicad_sch`（[NOW] のとおり v2.1 は明示）。PWR_FLAG の要否はここで出る
- ネットリストで「グランド 6 ノードを結ぶのは NetTie・JP だけ」を `sch_facts` の同じ列挙（[SF gnd]）で再確認
- 部品数・ERC 件数の期待値は変わる（CLAUDE.md の表の更新は回路図を変えたコミットで）

### 7.3 ±15 V の負荷（RS6-1215D ±200 mA に対して）

[RB-pd] の固定側（ソケット以外）は `+15V` 71.1 / 90.8、`-15V` 35.9 / 42.6 mA（typ / max）。これに INA1650 の IQ 10.5 / 12 mA（両レール [tap:L106]）を足す [計算]:

| シナリオ（[RB-pd] の行） | `+15V` typ / max | `-15V` typ / max | RS6 ±200 mA に対する max |
|---|---|---|---|
| 固定側のみ（＋INA） | 81.6 / 102.8 | 46.4 / 54.6 | 51 % / 27 % |
| 1 ch・NE5532 | 87.6 / 118.8 | 52.4 / 70.6 | 59 % / 35 % |
| 1 ch・在庫の最悪 | 101.6 / 122.8 | 66.4 / 74.6 | 61 % / 37 % |
| 2 ch・NE5532 | 93.6 / 134.8 | 58.4 / 86.6 | 67 % / 43 % |
| 2 ch・在庫の最悪 | 121.6 / 142.8 | 86.4 / 94.6 | 71 % / 47 % |
| 8 ch・NE5532 | 129.6 / **230.8** | 94.4 / 182.6 | **115 %** / 91 % |
| 8 ch・在庫の最悪 | 241.6 / **262.8** | 206.4 / **214.6** | **131 % / 107 %** |

比較: ADC を `+15V` のまま（[RB] 無印）だと 2 ch・在庫の最悪で `+15V` max 217.7 mA（**109 %**）。PD へ移すと max 86.9 mA 減り [RB-pd]、INA で 12 mA 戻る [計算]。
**全 ch 通電は RS6 では足りない**（`rail_budget.py` の表は REC20K/REC10K だけで RS6 の列が無い。上の % は手計算）。何 ch まで同時に生かすかはファームの決定（[NOW]）。
信号電流（帰還網・負荷）は `rail_budget.py` 自身が積んでいない（出力の注記）。6.3 (b) を採るとさらに各レール max 18.4 mA 減る。

### 7.4 残る決定・PCB が要るもの

| # | 決めること | 選択肢 | 何で決まるか |
|---|---|---|---|
| 1 | `ADC_GND` の Q2 の相手 | **`D_GND`（推奨）**／`PD_GND` | I²S の帰りを取るか、ADC の帰りを `D_GND` に通さないほうを取るか（3.1）。星を 1 か所に寄せるなら差は小さい |
| 2 | JP1601〜1603 の形 | **1×3 ヘッダ＋シャント**／3 パッドはんだジャンパ（「両方」を物理的に防げない）／3 回路スライドスイッチ | 排他性（3.3） |
| 3 | `D1612`/`D1613` の品と、そもそも入れるか | `RB160M-30` ×2／他 | 87 mA を連続で受けられるか（DS がリポジトリに無い） |
| 4 | センス点 | **`J_ANA101` pin 9**／pin 8／`J_RAIL501.2`／娘に専用ピン（生成シートの変更） | ch ごとの差をどこまで追うか。1 点だけにすること（5.2） |
| 5 | RCOM | **1 MΩ**／0 Ω | DS §8.1.2（1 MΩ で不整合に強い） |
| 6 | `±15V_AFE` の RC | 4.7〜10 Ω／フェライト／入れない | DC-DC の実リップル（RS6 か REC20K か）。入れないなら ADC 側 4 石のデカップリングを流れるリップル電流が JP1601→NT1603 を跨ぐ |
| 7 | LDO 前の RC と PPTC の定格 | R 2.2〜4.7 Ω、C 47 µF＋MLCC、PPTC hold 0.25 A 級 | PPTC の DS（温度ディレーティング）を取ってから。**[DEC]「PPTC は戻さない」の前提が変わる点をユーザーが判断** |
| 8 | ADC 入力の保護 | 6.3 の (a)〜(d) | ADC を壊さない優先度 |
| 9 | I²S の直列抵抗 | 0 Ω／33〜330 Ω | ファームのパッド設定の確認と、ADC 電源断時の運用 |
| 10 | `J1601` | 3P 化／削除 | B5 のハーネス判断（MC を別基板にする可能性を残すか） |
| 11 | DC-DC | `REC20K`（図）／`RS6-1215D`（候補） | 同時通電 ch 数。RS6 なら全 ch は不可（7.3） |
| 12 | INA1650 の ±15 V での CMRR | 規定値なし（表は ±18 V） | 必要なら実測 |
| 13 | **PCB** | JP1601・NT1602・NT1603 を 1 か所に（今の親ラフでは離れている [PCB]）／`ADC_GND` の島の境界に INA1650（入力側ピン 1〜7 を `U1611` 側へ、REF/OUT 側 8〜14 を島の中へ [PDF p3 のピン配置]）／`AMP_SEL_L`–`AGND_SNS`–`AMP_SEL_R` の 3 本並走／`PD_12V_ADC` を星の近くを通して島へ（LDO の DC ループを小さく）／`ADC_GND` の島は 1 か所（JP1601）でしか外とつながらないゾーンにする（[NOW]「ベタ GND は 1 枚にできない。系統ごとに別ゾーン」） | 配線段階（B5） |

### 7.5 使わなかった／確かめられなかったもの

- INA1650 の入力バイアス電流: `TI_INA1650.pdf` の電気的特性表（p6〜7）の抽出に見つからなかった
- PCM1804 の VCOM の出力インピーダンス・CMRR: DS に無い（p7 と p29 を見た範囲）
- PPTC（RXEF 系）・ショットキ（RB160M-30）の DS: リポジトリに無い
- REC20K のリップル・起動時間: `ds_facts/power.md` に REC20K の節が無い（[NOW] の「265 kHz・100 mVp-p」は記録であって照合していない）
- ADC 側の電流の実測値（グランドのずれ Vg）: 無い（`review/tap_compare_review.md` 4-5 も同じ）
