indare/pcb_work/AudioV2.1/review/adc_gnd_retree_review.md

# 否定側査読: `AudioV2.1/review/adc_gnd_retree.md`（ADC グランドの木の組み替え）

- 作成: 2026-09-25（査読エージェント）。**リポジトリのファイルは変更していない**。書いたのはこのファイルだけ
- 対象: `AudioV2.1/review/adc_gnd_retree.md`（以下「提案」）。回路図は `AudioV2.1/`
- 前提（ユーザー決定。蒸し返さない）: タップは `AMP_SEL_L/R`／結合は Q2（`U1611` の後ろに INA1650、Q1 に戻せる）／ADC 経路に絶対品質は不要、本線を汚さないのが最優先／ADC の LDO は PD 12 V から
- 追加の前提（コーディネータ経由のユーザー前提）: PD → DC-DC の給電は主電源スイッチで切り替わり、ADC の LDO の枝もそのスイッチの後ろから取る。→ **回路図で確認した**（下の 1 行目・§7）

## 出典の記号

| 記号 | 意味 |
|---|---|
| [SF pin X] / [SF nets N] / [SF rails] / [SF iface] / [SF aliases] | このセッションで回した `python3 AudioV2.1/scripts/sch_facts.py pin X / nets --net N / rails / iface / aliases` |
| [SF gnd] | `sch_facts.Design` を読み取り専用で回し、`A_GND` `D_GND` `PD_GND` `ADC_GND` `GND_COIL` の 2 つ以上にピンを持つ部品を全シートから列挙したもの（スクリプトはスクラッチパッド） |
| [RB-pd] | `python3 AudioV2.1/scripts/rail_budget.py --adc-from-pd` |
| [PCB] | `AudioV2Case.kicad_pcb` のフットプリント座標（親ラフ） |
| [INA pN] [PCM pN] [LT pN] [REC20K pN] [CH224 pN] [RP2350 pN] | `pdftotext -layout` で開いた PDF のページ（`datasheets/tap/TI_INA1650.pdf`、`TI_PCM1804.pdf`、`ADI_LT1763.pdf`、`Recom_REC20K-Z_Rev3-2025.pdf`、`WCH_CH224.pdf`、`RaspberryPi_RP2350.pdf`） |
| [tap:L] [pow:L] [op:L] [sc:L] | `AudioV2.1/ds_facts/tap.md` / `power.md` / `opamps.md` / `switch_control.md` の行（照合済み） |
| [計算] | 上の数値からの算術 |
| 〔推論〕 | 出典から直接は言えない判断 |

---

## 0. 結論

**骨格は覆らなかった。** `NT1601` を消して `ADC_GND` を Q2 では `D_GND` の葉にする、グランドの選択は 1×3 ヘッダ 1 個だけ、INA1650 の REF を `ADC_GND`、`U1602` の基準を `ADC_GND` へ、という形は回路図と DS に照らして成立する。`F1601` の読みも提案が正しく、以前の 2 本の査読が間違っている。

**ただし、次の 8 点は直す必要がある**（詳細は §9）:

1. **センス線の電流は「nA 級」ではない。** RCOM = 1 MΩ だと IN− から約 6.2 µA pk/ch の信号電流が出る（2 ch で ≈12 µA pk）。影響は無視できる大きさ（−120 dB 以下）だが、根拠の式が違う
2. **センス線が切れたときの「Q1 相当に落ちる」は誤り。** RCOM = 1 MΩ だと利得は 1/3（−9.5 dB）になる。Q1 相当になるのは RCOM = 0 のときだけ
3. **`±15V_AFE` の RC は「電流を絞る」ものになっていない。** 35 dB はレールの電圧の減衰で、`ADC_GND`→`NT1603`→`A_GND` を渡る電流は ≈ Vripple/R。4.7 Ω だと 265 kHz で最大 ~10〜21 mA p-p を**新たに** `A_GND` の星点へ入れる〔推論〕。提案の「フェライトビーズでもよい」は 265 kHz では効かない
4. **LDO 前の RC は「リップル電流を PD 側で閉じる」になっていない。** LDO 足元の MLCC（`ADC_GND` 側）のほうが `C1651`（`PD_GND` 側、電解）より 265 kHz でインピーダンスが低いので、R を通るリップル電流の大半は `ADC_GND` を回る〔推論〕
5. **「今は ±15 V と ADC 電源は一緒に来る」は誤り。** LT1763 は CBYP 10 nF で起動に 15 ms かかる [LT p15] ので、今の図でも電源投入時は ADC 電源が ±15 V より遅れる。組み替えで**新しく起きるのは電源断のときの窓**（ADC が先に落ちる。≈15〜40 ms〔推論〕）
6. **「木」はガルバニックな話に限られる。** `U201` の絶縁容量（2000 pF typ [REC20K p6]）で AC の閉路は今もある。そのうえ提案では `±15V_AFE` の R∥R ≈ 2.4 Ω が、高い周波数で `ADC_GND`–`A_GND` を直接つなぐ第 2 経路になる（**新規**）
7. **20 V の PD で「`U201` も同じ事故」になるのは RS6 のときだけ。** 図の REC20K は 9〜36 V。LT1763 は公称 20 V の時点で絶対最大 ±20 V ちょうどで、PD の電圧許容差の分だけ超える
8. **Q1 モードの 87 mA は、PCB 次第で今より長く `A_GND` を横切る**（今の親ラフでは `NT1603` が MC から約 400 mm 離れている [PCB]）

---

## 1. 検証の表

| 項目 | 提案の記載 | あなたの確認 | 支持/修正 | 出典 |
|---|---|---|---|---|
| **F1601 の位置** | `J1602`→`F1601`→`PD_12V_SW` だけ。本線の `J202`→`SW402`→`PD_12V_SW` にヒューズは無く、枝ごとに `F201`/`F202`/`F1602` | `F1601.1`=(`J1602.2` だけ)、`F1601.2`=`PD_12V_SW`。`J202.2`=`PD_12V`→`SW402.2`、`SW402.1`=`PD_12V_SW`。`PD_12V_SW` の 11 ピン: `C1610/1611/1612`、`F1601.2`、`F1602.1`、`F201.1`、`F202.1`、`J_PNL_P1602.1`、`J_PNL_P1612.1`、`R401.1`、`SW402.1`。`PD_12V`（4 ピン）にヒューズは無い | **支持** | [SF pin F1601/J1602/J202/SW402]、[SF nets PD_12V/PD_12V_SW] |
| 本線の各枝の保護 | F201 F2A fast、F202 PPTC 0.4 A、F1602 PPTC 0.5 A | Value はそのとおり（`F201` "F2A fast 5x20"、`F202` "PPTC 0.4A hold"、`F1602` "PPTC 0.5A hold"）。**`R401`（LED 1k）と `J_PNL_P1602/1612`（FP への 12 V）もヒューズの外**だが、R 1k と LED なので実害は小さい | 支持（補足） | [SF pin F201/F202/F1602/R401/D403] |
| 主電源スイッチの後ろから LDO を取る（前提） | `ADC_V_IN`＝`PD_12V_SW` | `ADC_V_IN` は `PD_12V_SW` の別名。`U1607` の枝（`F1602`→`PD_12V_MEAS`）と `U201` の枝（`F201`）も同じ `PD_12V_SW` から | **前提どおり** | [SF aliases]、[SF nets PD_12V_MEAS] |
| 今の木 | `ADC_GND─NT1601─A_GND─NT1603─D_GND─NT1602─PD_GND`、`GND_COIL─NT101─D_GND` | NetTie 4 個はそのとおり | 支持 | [SF pin NT1601/NT1602/NT1603/NT101] |
| グランドを跨ぐ部品 | NetTie・コネクタ・`U201` だけ | 全シートを列挙: `J_PWR101/301/302`（ピンごとに別ネット）、NetTie 4、`U201`（.5=`A_GND`、.2=`PD_GND`）だけ。FrontPanel・Pico・LCD・娘の中に跨ぐ部品は無い。※ `AmpBankSwitch` 側の `GND_COIL`（`J_PWR301.6`）は 1 ピンだけの別ネット（どこにもつながらない） | 支持 | [SF gnd]、[SF nets] |
| `U201` = ±15 V の帰り | .5=`A_GND`、REC20K のまま | .1=F201 の後、.2=`PD_GND`、.4=`-15V`、.5=`A_GND`、.6=`+15V`。lib は `AudioV2:REC20K-2415DZ`。RS6 は未実装 | 支持 | [SF pin U201] |
| INA1650 のピン | VCC1 IN+A2 COMA3 IN−A4 IN−B5 COMB6 IN+B7 OUTB8 REFB9 VMID(OUT)10 VMID(IN)11 REFA12 OUTA13 VEE14 | 一致 | 支持 | [INA p3] |
| REF の駆動 | 低インピーダンスで駆動すること | "This pin must be driven from a low impedance." `ADC_GND` 直結で満たす | 支持 | [INA p3、p29] |
| REF 電流 | 約 0.39 mA pk/ch | REF→10 kΩ→＋ノード→10 kΩ→IN+ のバッファ出力 [INA p15 ブロック図]。7.74 V/20 kΩ = 0.387 mA pk | 支持 | [INA p15]、[計算] |
| 入力構造・「センスにバッファ不要」 | 入力は内部バッファ付き | 各入力に 500 kΩ→COM、EMI フィルタ、入力バッファ、10 kΩ×4 の差動アンプ [INA p16 Fig.39]。入力インピーダンスは差動 850/1000/1150 kΩ、同相 212.5/250/287.5 kΩ [INA p7]。**バッファ不要は支持** | 支持 | [INA p7、p16]、[tap:L102] |
| センス線の電流 | 「(Vg)/1.5 MΩ、nA 級」 | **RCOM = 1 MΩ だと COM = 0.4·V(IN+) になり、IN− から 0.4·Vs/500 kΩ = 6.2 µA pk/ch が流れる**（フルスケール 7.74 Vpk）。L/R 共用なので最大 ≈12 µA pk が `NT102` から `A_GND` へ。nA 級になるのは RCOM = 0 のときだけ | **修正**（結論＝影響なし、は残る） | [INA p15–16]、[計算] |
| センス断線時 | 「IN− は 500k＋1M で ADC_GND に引かれ、Q1 相当」 | IN− が開くと V(IN−) = V(COM) = Vs·1M/(500k+1M) = 0.667 Vs → 出力 0.333 Vs（**−9.5 dB**）。Q1 相当になるのは RCOM = 0 のときだけ | **修正** | [計算] |
| CMRR と源インピーダンスの不整合 | 不整合は 1 Ω 未満 → typ 付近 | 20 Ω の不整合で 84 dB typ、RCOM 1 MΩ なら 89.6 dB [INA p6、p18]。不整合 1 Ω なら CM→差動の変換は ≈1 Ω/250 kΩ（−108 dB）で、素子の CMRR（85 min）が支配〔推論〕。**±15 V での規定値は無い**（表は ±18 V） | 支持 | [INA p6、p18]、[tap:L97–101] |
| 同相入力範囲 | (V−)+0.25〜(V+)−2 | 表どおり。本文 §8.1.1 は 350 mV（食い違いの指摘も正しい）。`±15V_AFE` で V+ が 13.7 V（R 33 Ω）に下がっても上限 11.7 V > 7.74 Vpk | 支持 | [INA p6、p18]、[計算] |
| IQ | 8/10.5/12 mA（全温度 14） | 一致（1 ch あたりの字句は無い＝パッケージ値として使うのが正しい） | 支持 | [INA p7]、[tap:L106] |
| 出力負荷 | 4.7k∥6.19k ≈ 2.67 kΩ | `R1612.2`/`C1628.2`=`ADC_BUF_L`、`R1612`→`U1602` 反転入力、`C1628`→`R1618`→`U1608` 反転入力。一致 | 支持 | [SF pin R1612/C1628/R1618] |
| `U1602` の基準を `ADC_GND` へ | +IN が今 `A_GND` | `U1602.3/.5`=`A_GND`。式（差動 = −2k(x−Vr)）も正しい | 支持 | [SF pin U1602] |
| ADC ドライバの 47 Ω | DS Fig.44 の R5/R6 と同じ | **値は同じだが位置が違う。** DS は R5(R6) を「帰還ループの中」に置く [PCM p29]。この図は `U1608.1`=`R1613.2`=`R1616.1`（帰還は 47 Ω の手前から）で**ループの外**。過電流の見積もり（47 Ω で制限）はこの形だから成り立つ（ループの中だと出力がレールまで振れて制限にならない） | 支持（注記） | [SF pin U1608/R1613/R1616]、[PCM p29] |
| センス点 `J_ANA101` pin 9 | 9 は `AMP_SEL_L`（7）の隣、8 は R（10）の隣 | `J_ANA101`: .7=`AMP_SEL_L`、.8/.9=`A_GND`、.10=`AMP_SEL_R`。2×5 Odd_Even では {7,8,9,10} が 2×2 の塊で、**9 は 7 と同じ列の隣、10 と同じ行の隣**。8 も 7・10 の両方に隣接。どちらでも同じ | 支持（補足） | [SF pin J_ANA101]、〔推論: 番号付け〕 |
| MC のシートピン | `AGND_SNS` に当たるものは無い | MC のシートピン 24 本に無い。今の界面不一致は 0 件 | 支持 | [SF iface]、sheet pin 一覧 |
| 参照番号の衝突 | `U1612`、`R1621–1625`、`C1651–1656`、`D1612/13`、`F1604`、`JP1601–1603`、`NT102` | どれも未使用（`C1650` は使用中、`C1644/1648/1649` は空き） | 支持 | 3 シートの `Reference` を grep |
| ±15 V 負荷（RS6 ±200 mA） | 固定＋INA 102.8、1 ch 最悪 122.8、2 ch 最悪 142.8、8 ch NE5532 230.8 / 最悪 262.8 mA（+15V max） | [RB-pd] の固定 71.1/90.8・35.9/42.6 に INA 10.5/12 を足すと表の全 14 セルが一致。% も一致。**8 ch は回路図のソケット数（Switch 4＋Relay 4）で、スロットは今 1 つ**。同時に何 ch が物理的に通電するかは娘の積み方次第 | 支持（注記） | [RB-pd]、[計算] |
| LT1763 の電流制限 | min 520 mA | "Current Limit … ● 520 mA"（MIN のみ） | 支持 | [LT p6] |
| LT1763 の IN 絶対最大 | ±20 V、20 V PD で「ちょうど」 | ±20 V [pow:L389]。**PD の公称 20 V は許容差の分だけ超えうる**（USB PD の電圧許容差は ±5 % 程度〔推論: 一般則、リポジトリに一次資料なし〕）。RC の降下 0.29 V では足りない | **修正**（「ちょうど」→「超えうる」） | [pow:L389] |
| 20 V で `U201` も同じ事故 | RS6 は範囲外 | RS6 は 9〜18 V（サージ 25 V/1 s）[pow:L23]。**図の REC20K-2415DZ は 9〜36 V** [REC20K p2]。事故になるのは LT1763 だけ（RS6 に替えたら両方） | **修正**（条件付き） | [REC20K p2]、[pow:L23] |
| PCM1804 入力の絶対最大 | −0.3〜VCC+0.3 V、±10 mA | 一致 | 支持 | [PCM p5] |
| ADC 入力の過電流 16 mA pk | (1.25−0.5)/47 | 式は正しい（0.6 V なら 14 mA）。**ただし「組み替えで新しく起きる」は電源断側だけ**（§7） | 修正（発生条件） | [PCM p5、p7]、[計算] |
| 今は ±15 V と ADC 電源は一緒に来る | 6.3 節 | **誤り。** LT1763 の起動は CBYP 0.01 µF・COUT 10 µF で 15 ms [LT p15]。この図は CBYP 10 nF（`C1608`/`C1623`）、`U1606` は `+3V3_A` を待つ。今の図でも ADC 電源は ±15 V より 15 ms 以上遅れる〔推論〕 | **修正** | [LT p15]、[SF pin U1603/U1606] |
| PD 12 V 直結での PPTC | 前提（REC20K の SCP でヒカップ）が崩れる。PPTC hold 0.25 A 級 | 支持。上流に保護は無く、CH224K モジュールにも過電流保護は無い（メーカー記載）。保護は PD 充電器の OCP だけ〔推論〕 | 支持 | [SF nets PD_12V_SW]、`datasheets/StrawberryLinux_50224_CH224K.md` |
| LDO 前の RC 3.3 Ω/47 µF | 角 0.85 kHz、降下 0.29 V、帰りは `PD_GND` で「PD 側で閉じる」 | 数値は正しい（1/(2π·3.3·57 µF) = 846 Hz）。**「PD 側で閉じる」は成立しない**（§6.2） | **修正** | [計算]、〔推論〕 |
| `±15V_AFE` 4.7 Ω | 降下 0.19 V、角 3.4 kHz、200 kHz で 35 dB、「直列抵抗で絞る」「フェライトでもよい」 | 数値は正しい（`C1635`/`C1640` は 10 µF 固体電解、`C1634` 等は 100 nF）。**35 dB はレール電圧の話で、跨ぐ電流は減らない**（§6.1） | **修正** | [SF pin C1634/C1635]、[計算] |
| REC20K のリップル | ds_facts に無く未照合 | PDF で確認: 内部動作周波数 265 kHz、出力リップル＆ノイズ 100 mVp-p（"others"、nom. VIN 24 V、全負荷、20 MHz BW）、起動時間 20 ms typ / 50 ms max、絶縁容量 2000 pF typ（100 kHz/0.1 V、p6）、UVLO OFF 6.5〜8 V | 追加 | [REC20K p2、p6] |
| Q1 の 87 mA の横切り | `JP1601`–`NT1603` 間の `A_GND` だけ | 部品配置次第。今の親ラフでは `NT1601`(86.8, 68.6)、`NT1603`(286, 440)、`U201`(334.4, 41.4) [PCB]。今は `NT1601`→`U201` で約 250 mm、提案の Q1 は MC→`NT1603` で約 430 mm | **修正**（PCB の条件を明記） | [PCB]、[計算] |
| I²S の帰り | Q2 で 1 ホップ | `A1602` の GND は全部 `D_GND`、`ADC_DATA/BCK/LRCK` は `A1601`→`A1602` の GP0–2。Q2 で 1 ホップになるのは正しい | 支持 | [SF pin A1602/A1601] |

---

## 2. F1601 の決着と、間違っている文書

**ネットリストの答え**: `F1601` は **`J1602`（MC の予備 12 V 端子）と `PD_12V_SW` の間だけ**にある。`J202`（PD モジュール）からの本線は `PD_12V` → `SW402` → `PD_12V_SW` で、ヒューズを通らない [SF pin F1601/J1602/J202/SW402]、[SF nets PD_12V/PD_12V_SW]。
`F1601` は箱のマスターではない。**PD 12 V から取る ADC の LDO の上流に保護は何も無い**（ある保護は PD 充電器自身の OCP だけ〔推論〕）。

副作用（どこにも書かれていない）: `J202` から給電しているとき、`J1602` は `F1601`（T1A）越しに**スイッチ後の 12 V が出ている端子**になる。`J1602` から給電すると `SW402` を迂回する。両方つなぐと電源が並列になる〔推論〕。

経緯（回路図と文書から）: DECISIONS の電源ツリー図（`PD入力 ─ F1601(1A) ─── PD_12V_SW`）は MC が別基板で `J1602` からしか給電されなかったころの図。MC が母板に載って `ADC_V_IN` がルートの `PD_12V_SW` と同じネットになった時点で、`F1601` は予備入口のヒューズになった〔推論: 2026-09-09 の MotherBoard 廃止・09-15 の再配置の後と読める〕。

**間違っている／古い文書**（書き換えはしていない。ユーザーの判断で）:

| 文書 | 箇所 | 何が違うか |
|---|---|---|
| `AudioV2.1/review/rejected_review.md` | #7（33 行）、202 行 | 「PD 12 V 給電だと上流は `F1601`」「`F1601` が切れて U201・コイル・Pico まで全部止まる」→ **誤り**。上流にヒューズは無い。**「PPTC を戻す価値あり」という結論は、別の理由（上流が無保護）でむしろ強まる** |
| `AudioV2.1/review/rejected_review_review.md` | #7（23 行）、71 行 | 「`F1601`→`PD_12V_SW`、その下流に `F201`/`F202`/`F1602`。つまり `F1601` は箱全体のマスター」「さらに `F1601` は `F201`/`F202`/`F1602` すべての上流」→ **誤り**（`F1601.1` の相手は `J1602` だけ。ピン 2 側に `PD_12V_SW` があるのを上流と読み違えた）。同じ行の「`PD_12V_MEAS` から取れば PPTC を足さずに済む」と「充電器の OCP が先に効くかもしれない」は正しい |
| `AudioV2.1/review/decisions_audit_1_review.md` | 73 行 | 「上流は `F1601` か PD 側」「`F1601` は計測基板全体のバックストップなので Pico ごと落ちる」→ **誤り** |
| `AudioV2.1/review/decisions_audit_1.md` | 78 行 | 「短絡を受けるのは PD 側（F201／F1601 の系）」→ **誤り**（F201 は U201 の枝、F1601 は J1602 の枝。どちらも LDO の枝の上流ではない） |
| `AudioV2.1/NOW.md` | 10 行 | 「上流が `F1601` になる、と査読」→ 誤った査読をそのまま載せている |
| `AudioV2.1/DECISIONS.md` | 244 行（`F1601` を「枝ごとに PPTC」に含める）、1792・1806・1816 行（「基板全体のバックストップ」）、1918 行の図 | 今の図に対しては**古い**（履歴としては当時正しかった） |
| `AudioV2.1/AGENT_HANDOFF.md` | 209–218 行 | 同上（`F1601` は「PD 入力直後」「基板全体のバックストップ」） |
| `AudioV2.1/PARTS.md` | 347 行 | 「`J1602` 計測側の 12V 入口（`F1601` 経由で `U1607` へ）」→ 不完全。`F1601` の先は `PD_12V_SW` で、`U201` を含む全部の枝に行く |
| 提案（`adc_gnd_retree.md`）0.2 表・6.1 | — | **正しい** |

---

## 3. 木の検討（閉路は本当に無いか）

### 3.1 ガルバニック（回路図）

[SF gnd] で全シートを列挙した結果、グランドを 2 つ以上持つ部品は `J_PWR101/301/302`（ピンごとに別ネット）、`NT101`、`NT1601`〜`NT1603`、`U201` だけ。

- **`D_GND`/`PD_GND` と `A_GND` が会う場所は、ガルバニックには `NT1603` だけ**（`U201` は絶縁）。PD モジュールは `J202` の 2 ピンだけで入る。コイル（`U403` の GND=`GND_COIL`、`U321` の GND=`GND_COIL`）は `NT101` を経て `D_GND`。LCD／FrontPanel は `D_GND` と `A_GND` と `PD_GND` を別々の XH で受けていて、跨ぐ部品は無い。`J_PNL*` もピンごとに別ネット [SF pin J_PNL_P1601/1602/1611/1612]
- **提案の Q2・Q1 の木（ノード 6・辺 5）は正しい。** `JP1601` が 1×3 ヘッダ＋シャント 1 個なら、1-2 と 2-3 の同時は物理的に起きない（2 番ピンを 2 個のシャントで共有できない）。**支持**
- `AGND_SNS`–500 kΩ–COM–1 MΩ–`ADC_GND` の 1.5 MΩ の経路は提案どおり高インピーダンスの第 2 経路（ただし流れるのは nA ではなく µA。§4）

### 3.2 AC とガルバニック以外（提案に無いもの）

| 経路 | 新規か | 中身 |
|---|---|---|
| `A_GND`–(`U201` Ciso)–`PD_GND`–`NT1602`–`D_GND`–`NT1603`–`A_GND` | 既存 | 絶縁容量 2000 pF typ（100 kHz/0.1 V）[REC20K p6]。265 kHz で約 300 Ω、10 MHz で約 8 Ω [計算]。DC-DC の同相の変位電流がこの輪を回る。MC の図上注記も「U201 の Ciso 経由 CM が全部ここ（NT1601/1602/1603）を通る」と書いている。Q2 の `ADC_GND` は葉なのでこの電流を運ばないが、`JP1601` をこの輪の上に置くと `ADC_GND` の電位がこの IR 降下で動く（INA から見れば同相）〔推論〕 |
| **`ADC_GND`–(AFE のデカップリング)–`±15V_AFE`–R–`±15V`–(`A_GND` 側のデカップリング)–`A_GND`** | **新規** | 数 kHz より上では 2 本の R の並列（4.7 Ω なら ≈2.35 Ω）で `ADC_GND` と `A_GND` がつながる。Q2 では `JP1601`–`D_GND`–`NT1603` と合わせて閉路になる。§6.1 |
| ショットキ `D1612`/`D1613`（Q1 のとき） | 新規 | §3.3 |
| USB（Pico）→ PC のグランド | 既存 | Pico の USB は `D_GND`。PC が接地されていて、入出力の音響機器も接地されていると、`D_GND`–`NT1603`–`A_GND`–ジャックの輪になる。PD 充電器の Y コンデンサの漏れ電流も `PD_GND`–`NT1602`–`D_GND`–USB を流れる〔推論〕。**組み替えで増えも減りもしない**。Q2 では `ADC_GND` がこの電流の流れる `D_GND` にぶら下がるが、INA の同相で除かれる |
| `J_RAIL501.2`（`A_GND`）に接地した外部測定器 | 既存 | USB と同時だと上と同じ輪 |
| **筐体・パネル（未決の C1）** | 既存（図の外） | `ENC1601.MP`（エンコーダの金属フレーム）は `D_GND` に接続されている [SF pin ENC1601]。パネルが金属で、パネルジャックのスリーブ（`A_GND`）やポットのボディ、PD モジュールの USB-C シェル（`PD_GND`〔推論: モジュールの一般的な作り〕）がパネルに触れると、`NT1603`/`NT1602` をまたぐ閉路ができる〔推論〕。**提案の「木」はシャーシを 1 点で落とす前提でしか成り立たない**。提案に無い |
| 娘の `A_GND` を `J_ANA`（.1/.2/.4/.5/.8/.9）と `J_PWR`（.2/.4）の両方で渡す | 既存 | `A_GND` の中の並列路（A↔D の混ざりではない）。センスを `J_ANA101.9` で取ると、娘の電源の帰り電流のうち `J_ANA` 側に分かれた分の接点降下がセンスに入る（提案も触れている） |

### 3.3 `JP1601` と逆並列ショットキ

- **Q1（1-2）でショットキは実質的な第 2 経路にならない。** 両端の電位差は `JP1601`–`A_GND` の島–`NT1603`–`D_GND` の降下（mV）。ゼロバイアス近くのショットキの小信号抵抗は ≈ nVT/Is で、Is が µA〜10 µA 級なら 2.6〜26 kΩ〔推論: RB160M-30 の DS はリポジトリに無い〕。mΩ の経路と並べると分流は 1e-6 級。**支持**
- ただし接合容量（数十 pF 級〔推論〕）が VHF では効く。100 MHz で 50 pF は約 32 Ω、`A_GND` の島＋`NT1603` の 20 nH は約 13 Ω で同じ桁〔計算〕。EMI の話で、音声帯には関係しない
- Q2（2-3）ではシャントと並列で何もしない。**支持**
- シャント無しのとき: 87 mA が片方のダイオードを通り、`ADC_GND` が `D_GND` から 0.3〜0.4 V 程度ずれる〔推論〕。I²S の受け側は RP2350 の VIL 0.8 V（[NOW] の記録）に対して余裕が少なくなるが、壊れはしない〔推論〕。「壊れない・動作は怪しい」という提案の評価は正しい
- 1×3 ヘッダの 1 番（`A_GND`）と 3 番（`D_GND`）は 5.08 mm 離れている。クリップやプローブで 1-3 を短絡すると `NT1603` と並列の輪になるが、害は輪ができることだけ〔推論〕

---

## 4. INA1650（DS と照合）

- ピン・REF・VMID・COM・CMRR・同相範囲・IQ は §1 の表のとおり**支持**
- **センス線の電流**（修正）: COM ノードは IN+（Vs）と IN−（≈0）にそれぞれ 500 kΩ、`ADC_GND` に RCOM でつながる。
  - RCOM = 1 MΩ: V(COM) = Vs·(1/500k)/(2/500k + 1/1M) = 0.4 Vs。I(IN+) = 9.3 µA pk、**I(IN−) = 6.2 µA pk（センス線へ）**、I(RCOM) = 3.1 µA pk（フルスケール 7.74 Vpk）[計算]
  - RCOM = 0: V(COM) = 0。I(IN−) ≈ Vg/500 kΩ（nA）、I(IN+) = 15.5 µA pk [計算]
  - 影響: センス線を L/R で共用するので、センス線の抵抗 Rs が L→R のクロストークになる。Rs = 0.1 Ω で −142 dB、1 Ω で −122 dB（7.74 Vpk 基準）[計算]。`NT102` から本線の `A_GND` へ入る信号電流は最大 ≈12 µA pk で、`A_GND` の mΩ では nV 級（−175 dB 級）[計算]。**無視できる**。ただし「nA」は RCOM = 0 のときの数字
- **センス断線**（修正）: RCOM = 1 MΩ で IN− が開くと、出力は Vs/3（−9.5 dB）。「Q1 相当に落ちる」は RCOM = 0 のときだけ。断線は測定レベルが 9.5 dB 下がることで見つかる
- **REF = `ADC_GND`**: 支持。VCOM の出力インピーダンスは DS に無い（Fig.45 は内部バッファの等価回路だけ [PCM p30]）ので、REF に VCOM を使わない判断は妥当
- 「センスにバッファは不要」: **支持**（入力バッファ内蔵 [INA p16]。IN− の源は銅箔と NetTie で 1 Ω 未満〔推論〕）

---

## 5. センス点（`NT102` @ `J_ANA101` pin 9）

- pin 9 = `A_GND`、pin 7 = `AMP_SEL_L`、pin 10 = `AMP_SEL_R` を確認 [SF pin J_ANA101]。pin 8 と 9 はどちらも L・R の両方に隣接するので、どちらでも同じ
- **娘ごと／切り替え点で取るべきか**: 親のスロットは今 `J_ANA101` 1 つで、`J_ANA301`（Switch）と `J_ANA302`（Relay）は同じネットに載っている [SF nets AMP_SEL_L]。**娘ごとにセンスを分ける意味は、娘を積み重ねて同時に挿す構成にしたときだけ**〔推論〕。
  切り替え点（TMUX の D ／リレーの COM）で取るには娘側にピンが要る。**`J_PWR` の 11〜16 は親・娘とも N.C.** [SF pin J_PWR101]（NOW にも「旧 ADDR/SEL、N.C.」）なので、コネクタを変えずに 1 本通せる。ただし `J_PWR` は I²C・コイル電源の隣で、IN− は 500 kΩ の高インピーダンスなので容量結合を拾う〔推論〕。生成シートの変更も要る。**今回は `J_ANA101` で妥当**（本線が受け取るのもコネクタの電位差なので、「聴いているもの」と揃う）
- **`AGND_SNS` の階層ラベル＋シートピン**: 必要（今の MC のシートピンに無い [SF iface]）。ルートは手編集所有なので KiCad で両方に足し、`sch_facts.py iface` で 0 件を確かめる、という提案の手順は CLAUDE.md どおり。支持
- センスの NetTie は 1 個だけ、という注意は正しい

---

## 6. 電源の組み替えで流れる HF 電流

### 6.1 `±15V_AFE`（問 6）

**あるか**: ある。ADC 側 4 石のデカップリングを `ADC_GND` に置くと、±15 V の帰りは `U201.5`（`A_GND`）なので、±15 V のリップル（`A_GND` 基準）が R→C→`ADC_GND`→`JP1601`→`D_GND`→`NT1603`→`A_GND` と流れる。今の図（デカップリングが `A_GND`）では、この電流は `NT1603` を通らない。

**大きさ**（R より上の周波数では C のインピーダンスが R よりずっと小さいので、渡る電流 ≈ Vripple/R）[計算]:

| R（各レール） | 降下（39.6 mA＋信号） | 渡る電流（Vr = 50〜100 mVp-p、265 kHz） | レールの角周波数（10 µF） |
|---|---|---|---|
| 4.7 Ω（提案） | 0.19 V | **10.6〜21 mA p-p** | 3.4 kHz |
| 22 Ω | 0.87 V | 2.3〜4.5 mA p-p | 0.72 kHz |
| 33 Ω | 1.31 V | 1.5〜3.0 mA p-p | 0.48 kHz |

- Vr の上限は DS の値（REC20K 100 mVp-p、RS6 50/75 mVp-p。どちらも DS の試験用コンデンサ条件）[REC20K p2]、[pow:L47]。この基板は ±15 V に約 290 / 271 µF [SF rails] があるので、実際はこれより小さい〔推論〕。**表は上限**
- `A_GND` 上の電圧に直すと、例えば 20 mA p-p × `NT1603`→`U201` 区間 10 mΩ ≈ 0.2 mV p-p（265 kHz）〔推論〕。音声帯の外だが、星点のそばに入る
- **フェライトビーズは 265 kHz ではほぼ効かない**（インピーダンスが意味を持つのは 10 MHz より上〔推論: 一般的な特性〕）。提案の「フェライトビーズでもよい」は削る。効かせるなら R を 22〜33 Ω に上げる（INA の同相上限は V+ − 2 = 11.7 V でまだ 7.74 Vpk の上）か、47 µH 級の本物のインダクタ＋ダンピング
- もう一つの手〔推論〕: ADC 側の石の電源ピンの間（V+–V−）に直接 100 nF〜1 µF を置き、グランドへのコンデンサを小さくする（グランドを通るリップル電流が減る）
- 静止電流は正負で打ち消し、音声帯の信号電流（REF 電流 0.39 mA pk/ch ほか）はどこにデカップリングを置いても渡る、という提案の結論は支持

**結論**: 「本線を汚さない」優先なら、4.7 Ω は小さい。**R = 22〜33 Ω を推奨**（値はユーザー判断。FP は同じでよい）。

### 6.2 LDO 前の RC（問 7 の一部）

- R1621 を通る `PD_12V_SW` のリップル電流（≈ Vr/3.3 Ω）は、`C1651`（→`PD_GND`）と LDO 足元の `C1605/C1606/C1618/C1619`（→`ADC_GND`）に**インピーダンスの逆比で分かれる**
- 265 kHz で 10 µF X7R（12 V の DC バイアス後）は約 0.06〜0.1 Ω、一般的な 47 µF アルミ電解は ESR 0.3〜1 Ω 級〔推論〕 → **75〜95 % が `ADC_GND` 側へ**〔推論〕。Q2 では `JP1601`→`D_GND`→`NT1602` を通り（`A_GND` は通らない）、Q1 では `A_GND` の島を通る
- 提案が引く `C1645` の Description の理屈は「レギュレータ自身の脈流を自分の GND で閉じる」話。LDO は脈流を引かないので、ここで問題なのは上流のリップルの行き先で、同じ理屈は当てはまらない
- 直し方〔推論〕: `C1651` を低 ESR（導電性高分子＋10 µF MLCC）にする／LDO 足元は DS の下限 1 µF まで小さくする（「1 µF〜10 µF で足りる」[LT p14]）／`C1651` と LDO 足元の間にもう 1 本 R（1〜2.2 Ω）を入れて 2 段にする
- **R1621 のパルス耐量**: LDO 入力側の短絡では 12 V/(3.3 Ω＋PPTC) ≈ 3 A 級が PPTC が切れるまで R1621 に流れる（≈30 W 級の瞬時電力）[計算]。パルス定格のある品が要る（提案に無い）
- RC は、`SW402` を入れたときの突入のリンギングを LDO の手前で鈍らせる働きもある（τ = 3.3 Ω × 57 µF ≈ 190 µs）[計算]。12 V 設定なら LT1763 の ±20 V に余裕がある。残す価値あり

---

## 7. リスクの再判定（コーディネータの前提で）

**前提の確認**: `PD_12V`（`J202.2`）→`SW402`→`PD_12V_SW` → `F201`（DC-DC）・`F202`（コイル）・`F1602`（→`U1607`→`+5V_D`→`D1601`→Pico VSYS `A1602.39`）・`F1601.2`・`R401`・`J_PNL_P1602/1612`。LDO の新しい枝も `PD_12V_SW` から。**すべて回路図どおり** [SF nets PD_12V/PD_12V_SW/PD_12V_MEAS]、[SF pin D1601/U1607]。
→ 定常状態で「ADC 電源なし・±15 V あり」（とその逆）は起きない。残るのは次の 3 つ。

### 7.1 立ち上がり・立ち下がりの時間差

使った値: REC20K の起動 20 ms typ / 50 ms max、UVLO OFF 6.5〜8 V [REC20K p2]。RS6 の起動 2 ms typ [pow:L38]。LT1763 の起動は CBYP 0.01 µF・COUT 10 µF で 15 ms [LT p15]（この図は CBYP 10 nF [SF pin U1603/U1606]、`U1606` は `+3V3_A` が SHDN 閾値 ≤2 V [pow] を超えてから）。`PD_12V_SW` 57.1 µF [SF rails]、`+15V`/`-15V` 290.9 / 270.7 µF [SF rails]。

| 場面 | 今の図（LDO は `+15V` から） | 提案（LDO は `PD_12V_SW` から） |
|---|---|---|
| **投入**（PD 交渉済みで `SW402` ON） | ±15 V が先、ADC は 15 ms 以上遅れる → **順方向の窓は今もある**〔推論〕 | REC20K: ±15 V 20〜50 ms、ADC 約 20〜30 ms〔推論〕→ **順序は保証されない**（どちらも起きる）。RS6: ±15 V 2 ms、ADC 20〜30 ms → 約 20 ms の順方向の窓 |
| **遮断**（`SW402` OFF） | `+5V_A` は `+15V` が 5.3 V を切るまで保つ → 窓は小さい | `PD_12V_SW` は約 0.5 A の負荷で ≈4 V/ms で落ち、U201 は約 1.4 ms で止まる。ADC 電源は約 3〜5 ms で落ちる。±15 V は 290 µF・80〜130 mA で 0.26〜0.45 V/ms → ±5 V まで 20〜40 ms。**順方向の窓 ≈15〜40 ms（新規）**〔推論・計算〕 |

- **電源投入時に音が出ているか**: `PT2314E` は電源投入後 50 ms は I²C に触れない [sc: PT2314E I2C 初期化時間]、ファームの起動も後。POR 直後の既定の音量（ミュートか）は ds_facts に無い → **要確認**。音が出ていなければ、投入時に流れるのは結合コンデンサの過渡（ポップ）だけ〔推論〕
- **遮断時の電流**: ドライバ出力がクランプ（≈0.5〜0.6 V）を超えるのは、`AMP_SEL` のピークが ≈3.1〜3.7 V（ADC のフルスケールの約 −6〜−8 dB）を超えたときだけ [計算: 0.55 V/0.1616]。レールが落ちている最中なので過大入力（±13 V）は起きない〔推論〕。**最悪はフルスケールで 14〜16 mA pk が最大数十 ms**。絶対最大 ±10 mA の 1.5 倍で、大音量で鳴らしながら電源を切るたびに起きる〔推論〕
- **逆方向（ADC が先）**: REC20K だと投入時に起きうる（最大 ~30 ms）。VCOM 2.5 V が無電源のドライバの +IN の ESD から `+15V` 網（290 µF）へ流れる。電流は VCOM の内部バッファの能力で決まり、DS に値が無い [PCM p29–30] → **不明**。OPA1656 の入力は ±10 mA [op:L135]

### 7.2 1 本の枝だけの故障

- `F1604`（PPTC）トリップ・LDO の故障 → 順方向が**電源を切るまで続く**（音を出し続ければ上の電流が続く）
- DC-DC のヒカップ（±15 V 側の短絡）→ 逆方向が続く
- LDO の出力短絡 → そのレールが 0 V なので ADC 入力はクランプ側（順方向と同じ）

### 7.3 USB だけで Pico を動かす（`SW402` OFF）

- `3V3` は立つ。ADC の島と ±15 V は無電源
- 島を渡る線: `ADC_DATA/BCK/LRCK`（Pico の入力）、`ADC_nMR`（Pico GP15、オープンドレイン）[SF pin A1602/U1605]
- RP2350 のパッドのリセット値は **ISO = 1、PUE = 0、PDE = 1**（プルダウン）[RP2350 p788 PADS_BANK0 GPIO0 Register]。ファームは GP0–2・GP15 を触っていない（`firmware/*.py` を grep）→ **無電源の ADC に電流を押し込まない**。OD の `ADC_nMR` は Low か Hi-Z しか出さないので、無電源の `U1605` を駆動しない
- → **USB だけの給電は ADC のリスクにならない**。娘の MCP（`J_PWR` pin 10 の `3V3` で動く）が起動直後に出力を駆動し、無電源の娘の部品（v2.1 の ch ごとの LDO の EN など）に入る件は、この提案の範囲外（ch ごとの電源ゲートを設計するときに、各 LDO の EN の絶対最大を VIN = 0 で確かめること）
- 既存の気がかり（組み替えとは無関係）: GP15 の既定プルダウンが TPS3307 の MR の内部プルアップと引き合う。TPS3307 の DS がリポジトリに無いので MR が確実に H になるかは**要確認**

### 7.4 保護案の再判定

| 案 | 前提を入れた評価 |
|---|---|
| (a) 47 Ω → 100 Ω | 遮断時の窓（フルスケールまで）なら (1.25−0.6)/100 = 6.5 mA で ±10 mA 以内 [計算]。代償は 10 kΩ 入力との分圧 −0.09 dB と DS の値からの逸脱。**値だけの変更で済み、絶対品質は要らないという前提に合う**。推奨 |
| (d) VCOM–ドライバ +IN に 1 kΩ（2 個） | 逆方向（REC20K での投入時・DC-DC ヒカップ）を ≤2.5 mA に抑える。VCOML は `U1608` の 2 つの半分、VCOMR は `U1601` の 2 つの半分だけが見る [SF pin U1608/U1601] ので、1 kΩ の雑音は各 ch の差動入力で同相になる（提案の「L/R の 2 石とも同じ VCOM」は言い方が違う。結論は同じ）。**REC20K のままなら推奨、RS6 なら故障時だけの保険** |
| (b) ドライバを `+5V_A` 単電源に | 構造的に解決するが `+5V_A` の負荷と ADC の VCC への信号電流が増える。今回の前提では過剰 |
| (c) 割り切る | 「事故の窓だけ」ではなく**電源を切るたびの窓**になる点を踏まえて判断すること |
| `F1604` PPTC | 上流が無保護なので**必要**（主に LDO 入力側の短絡対策。出力短絡は LT1763 自身が守る [LT p6]）。代案: `PD_12V_MEAS`（`F1602` の後ろ）から取る — PPTC は増えないが、短絡で Pico も落ち、`U1607` の入力脈流の隣になる |
| 20 V PD | LT1763 は絶対最大 ±20 V ちょうどで許容差の分超えうる。**12 V 以外に設定しないこと**（`CH224K` のメモには「将来 20 V PD」とある）。守るならツェナー／TVS |

**PD の 5 V の窓**: `CH224K` には出力ゲート（GATE/NMOS#）が無い（それを持つのは `CH224D`）[CH224 p2]。PD の充電器は交渉前に 5 V を出すので〔推論: USB PD の一般則〕、**`SW402` を入れたまま USB-C を挿すと**、交渉のあいだ `PD_12V_SW` は約 5 V になる。REC20K は UVLO（ON 8〜8.5 V）で止まり、`U1603` は 3.3 V を出し、`U1606` は ~4.5 V → 逆方向の状態になる〔推論〕。`U1605` はリセットを保持する見込み（閾値は DS 未照合）。`SW402` を切った状態で挿せば起きない。

---

## 8. 提案に抜けているもの

1. **筐体／パネルでの閉路**（§3.2）。`ENC1601.MP` が `D_GND`。シャーシを 1 点で落とす判断（C1、未着手）が決まるまで「木」は条件付き
2. **`±15V_AFE` が作る HF の第 2 経路**（§3.2、§6.1）
3. **遮断時の窓は電源を切るたびに起きる**（§7.1）
4. **PD の 5 V の窓**（§7.4）
5. **R1621 のパルス耐量**（§6.2）
6. **I²S と Pico の USB**: Q2 で I²S の帰りが 1 ホップになるのは利点。ADC 側のデジタル（BCK 3 MHz 級、発振器）の帰り電流が `A_GND` を通らなくなるのも利点（今は `NT1601`→`A_GND`→`NT1603`）で、提案はこの利点を書いていない。PC のグランドは `D_GND` に来て、Q2 の `ADC_GND` はその電位に乗るが、INA の同相で除かれる。組み替えで PC 経由の輪が増えることは無い
7. **`Y1601`**: `+3V3_A`/`ADC_GND` のまま、ST（1 番）は `+3V3_A`、MCLK（`R1604`→`ADC_MCLK`→`A1601.7`/`TP1601`）は島の外へ出ない [SF pin Y1601/R1604/TP1601]。PD の 5 V の窓でも `+3V3_A` は出るので発振する〔推論〕。変更不要
8. **`U1605` と `ADC_nMR`**: §7.3 のとおり USB だけのときは安全。GP15 のリセット時プルダウンと MR の関係は既存の要確認事項
9. **Q1 モードでも INA は通電したまま**（10.5 mA）。害は無い
10. `U1611` に IN+ だけがかかる負荷は、同相 250 kΩ ではなく 500 kΩ＋(500 kΩ∥1 MΩ) ≈ 833 kΩ（RCOM 1 MΩ）[計算]。結論（今より軽い）は同じ

---

## 9. 訂正の一覧（提案に対して）

| # | 節 | 提案 | 訂正 |
|---|---|---|---|
| C1 | 5.4 | センス線は (Vg)/1.5 MΩ で nA 級 | RCOM = 1 MΩ では 6.2 µA pk/ch（L/R 合わせて最大 ≈12 µA pk）。影響は −120 dB 以下で無視できる |
| C2 | 2.6 | センスが切れても Q1 相当に落ちる | RCOM = 1 MΩ では −9.5 dB。Q1 相当は RCOM = 0 のときだけ |
| C3 | 4 結論 3 | RC で絞る、200 kHz で 35 dB、フェライトでもよい | 35 dB は電圧。跨ぐ電流は ≈Vr/R（4.7 Ω で最大 10〜21 mA p-p）。フェライトは 265 kHz で効かない。R 22〜33 Ω かインダクタ |
| C4 | 6.2 | フィルタの帰りを `PD_GND` にしてリップル電流を PD 側で閉じる | LDO 足元の MLCC（`ADC_GND`）のほうが低インピーダンスで、大半は `ADC_GND` を回る。`C1651` を低 ESR にする／足元を 1 µF に／2 段 |
| C5 | 6.3 | 今は ±15 V と ADC 電源が一緒に来る | 今も投入時は ADC が 15 ms 以上遅れる。新しいのは遮断時の窓で、電源を切るたびに起きる |
| C6 | 6.3 (c) | 事故の窓だけ | 上と同じ（遮断のたび） |
| C7 | 6.3 | 20 V で LT1763 は絶対最大ちょうど、`U201` 側も同じ事故 | 許容差の分超えうる。`U201` が事故になるのは RS6 のときだけ（REC20K は 9〜36 V） |
| C8 | 0.2 / 3 | 5 ノード 4 辺の木 | ガルバニックには正しい。AC では `U201` Ciso の輪（既存）、提案の `±15V_AFE` の R∥R（新規）、筐体（未決）がある |
| C9 | 3.2 | Q1 の 87 mA は `JP1601`–`NT1603` 間の島だけ | 島にできるのは `JP1601`/`NT1603` を隣に置いたときだけ。今の親ラフのままだと今より長く `A_GND` を横切る |
| C10 | 1.2 / 6.3 | 47 Ω は DS Fig.44 と同じ | 値は同じ。DS はループの中、この図はループの外（そのおかげで 47 Ω が電流を制限する） |
| C11 | 5.1 | 9 は L の隣、8 は R の隣 | 8 も 9 も L・R の両方に隣接 |
| C12 | 6.1 | （記載なし） | R1621 はフォールト電流が流れるので、パルス定格のある品 |
| C13 | 7.5 | REC20K のリップル・起動時間は照合していない | PDF p2 で確認: 265 kHz、100 mVp-p、起動 20/50 ms、Ciso 2000 pF typ（p6） |

提案の外で直すべき文書（§2 の表）: `rejected_review.md` #7、`rejected_review_review.md` #7・71 行、`decisions_audit_1_review.md` 73 行、`decisions_audit_1.md` 78 行、`NOW.md` 10 行。`DECISIONS.md`・`AGENT_HANDOFF.md`・`PARTS.md` の `F1601` の記述は古い。

---

## 10. ユーザーに残る決定

1. **`±15V_AFE` の R の値**（4.7 Ω／22〜33 Ω／インダクタ）。§6.1。「本線を汚さない」優先なら大きいほう
2. **LDO 前のフィルタの形**（`C1651` の品種、足元の容量、2 段にするか）。§6.2
3. **ADC 入力の保護**: (a) 100 Ω（遮断時の窓）と (d) 1 kΩ（REC20K のままなら投入時の逆方向）のどちらを入れるか。電源を切るたびの窓を飲むか
4. **ADC の LDO の取り口**: 新しい PPTC（`F1604`、hold 0.25 A 級、DS 未照合）か、`PD_12V_MEAS`（`F1602` の後ろ）か
5. **PD の電圧を 12 V に固定することの明文化**（20 V は LT1763 の絶対最大を超えうる）
6. **RCOM**: 1 MΩ（CMRR 優先、断線で −9.5 dB）か 0 Ω（断線で Q1 相当、センスは nA）
7. **`J1602`/`F1601` を残すか**: 今はスイッチ後の 12 V が出ている端子で、そこから給電すると `SW402` を迂回する
8. **シャーシを 1 点で落とす先**（C1）: 木が成り立つかはここで決まる。`ENC1601.MP`=`D_GND` の扱いも含む
9. **PCB**: `JP1601`・`NT1602`・`NT1603` を 1 か所に寄せる（Q1 の横切りと Ciso の輪を小さくする）
10. **DC-DC**（REC20K のままか RS6 か）: 起動時間（20 ms vs 2 ms）が投入時の窓の向きを決める。同時通電数（RS6 は 8 ch 不可）も
11. 確かめるもの（データ待ち）: `PT2314E` の POR 直後の音量状態、PCM1804 VCOM の駆動能力、RB160M-30／RXEF の DS、TPS3307 の MR の内部プルアップ
