indare/pcb_work/AudioV2.1/review/arch_zero_base.md

# v2.1 制御・電源・切替の木 — ゼロベースの構成検討

- 作成: 2026-09-25（エージェント）。**リポジトリで変えたのは `AudioV2.1/datasheets/arch/` への DS（PDF）の追加だけ**。回路図・スクリプト・ドキュメントは触っていない。コミットしていない
- 目的: v2 の部品構成を既定として持ち込まず、「1 枚だけ給電 → その中で 1 ch だけバスへ」の 2 段の制御の木を、機能 → 最小部品 → 今の図への対応、の順に組み直す
- **ユーザーの決定（2026-09-25、本書のベースラインに入れた）**: DC-DC は `RS6-1215D`／**娘 1 枚 4 ch**／**(ii) 選んだ 1 ch だけ給電**（ch ごとの正負 LDO＋EN、EN 保護は要る）／**娘の中の ch 選択はラッチングリレー**（各 ch のリレーがそのまま ch のバス境界。リレー娘に別の境界リレーは置かない）。**TMUX 娘は耳の比較用に残すかどうか未決 → 任意の変種として扱う**

## 凡例（出典）

| 記号 | 意味 |
|---|---|
| [NOW:Lnn] | `AudioV2.1/NOW.md` の行 |
| [sw:Lnn] / [pow:Lnn] | `AudioV2.1/ds_facts/switch_control.md` / `power.md`（照合済み） |
| [bnd:Lnn] | `AudioV2.1/ds_facts/boundary.md`（**未照合**。照合エージェントが走っている最中） |
| [DCS:Lnn] / [BPS:Lnn] | `AudioV2.1/review/dcdc_2stage.md` / `bulk_parent_sim.md` |
| [SF …] | 自分で回した `python3 AudioV2.1/scripts/sch_facts.py tree / bom / pin <REF> / nets --net <N> / rails / iface` の出力 |
| [RB-pd] | 自分で回した `python3 AudioV2.1/scripts/rail_budget.py --adc-from-pd` |
| [TPS2660 pN] ほか | 本書のために取得して読んだ DS（§A の表。版・URL つき）。p は PDF ページ |
| [BP5293 pN] / [L78 pN] / [AZ850 p2 図] | 既存の `AudioV2.1/datasheets/` の DS を自分で開いて読んだもの（ds_facts に行が無い項目） |
| 〔計算〕〔推論〕〔仮定〕 | DS の数値どうしの算術／DS にも図にも無い判断／置いた前提 |

---

## 0. 結論（先に）

### 0.1 推奨ベースライン（機能ごとに 1 案・いちばん強い理由 1 つ）

| # | 機能 | ベースライン | いちばん強い理由 |
|---|---|---|---|
| 1 | 娘の制御方式 | **娘から MCP23017／I²C を外す。親から静的なレベル線だけ（EN×4・SET×4・RESET×1）。デコードは全部親** | 娘に載るロジックが **VCC ピンの無い TBD62083A だけ**になる（入力＝DMOS のゲート [sw:L227, L236]）。聴取中に娘へ来るのは DC の EN 1 本だけで、クロックもアドレスも無い |
| 2 | 1 段目のワンホット（スロットの給電） | 親に `CD74HC238`（3→8、選ばれた 1 本だけ High、無効時は全 Low）[CD74HC238 p1] | 1 石で「高々 1 本」が DS の真理値で保証され、無効（PWR_EN=0）で全スロット OFF |
| 3 | 2 段目の ch EN（(ii)） | 親に `CD74HC4514`（4→16、選ばれた 1 本だけ High、E=High で全 Low）[CD74HC4514 p1]。アドレス＝{スロット 2 bit, ch 2 bit} | NOW で娘に置くと決めた「1 ch だけ ON できるデコーダ」[NOW:L15] を親の 1 石に集約でき、娘にロジックが要らない。16 本＝4 枚×4 ch がちょうど 1 石 |
| 4 | SET の宛先 | 親に `CD74HC4514` をもう 1 石。**③ と同じアドレス線を共有**、E には SET ワンショットの Q̅ | 給電デコーダ・EN デコーダと同じスロット線を使うので、**SET は給電中のスロットにしか行けない**（配線で決まる） |
| 5 | リセット → セットの順序（BBM） | 親に `SN74LVC1G123` ×5（**スロットごとのリセット 4 段の連鎖**＋SET 1 個）。リセット中は SET ワンショットを CLR̅ で殺す | 32 コイル同時は 1.28〜1.45 A 〔計算〕で `+5V_COIL` の枝（PPTC 0.4 A 保持、BP5293 1 A）を超える。**1 枚ずつ（8 コイル・最悪 362 mA）なら両方に入る**。順次化で増える時間は 45 ms で、切替全体（出力カップリングの整定 ≥ 1.5 s）に比べて無視できる |
| 6 | 電源投入時の全リセット | 親に `TPS3808G01`（閾値を分圧で約 4.2 V に）→ その RESET̅ の**立ち上がりエッジ**で ⑤ の連鎖を起動 | コイル電源が感動電圧（3.75 V [sw:L165]）より上がってから、ファームに依らず 1 回走る。レベルではなくエッジで起動するので、監視 IC が張り付いてもコイルに連続通電しない 〔推論〕 |
| 7 | スロットの +15 V スイッチ | `TPS26600`（eFuse）。R_ILIM 120 kΩ（I(OL) 0.085〜0.115 A）、C_dVdT 220 nF（15 V まで約 26 ms）、**外付け UVLO 必須**、SHDN に 33〜47 kΩ のプルダウン、FLT を給電確認に | 候補中、**DS が RS6 の定格 200 mA より下の電流制限を数値で保証する唯一の石**（0.1 A 設定 [TPS2660 p7]）。ソケット短絡を 4 ms で遮断する回路ブレーカ動作がある [TPS2660 p9, p21] |
| 8 | スロットの −15 V スイッチ | **ディスクリート**: −15 V 線に NMOS、PNP のレベルシフト（ゲートを 3.3 V 論理から駆動）、ミラー容量でソフトスタート、NPN＋検出抵抗で約 60 mA の電流制限、分圧＋ショットキーで −15 V 有無を検知 | 負電圧 eFuse の候補 `LM5067` は **−15 V では VCC の推奨電流 2 mA を満たせない端**にいて〔計算、§3.5〕、どのみち同じレベルシフトが要る。`TPS7A30` を代用すると制限が 220〜500 mA で RS6 を守れない [pow:L316] |
| 9 | コイル電源（常時） | **`BP5293-50` を `L7805C`（PD 12 V からのリニア）に替える**。PPTC 0.4 A は残す | 今の `+5V_COIL` は全娘へ配線され、娘の上でリレーの間を L/R の近くに通る [NOW:L110, L114]。BP5293 は軽負荷で SLLM（間欠）に入り出力リプル 50 / 200 mVp-p [BP5293 p4, p5]。**聴取中はコイル電流 0 なので、スイッチングの無いリニアで十分**（パルス時の損失は (12−5) V × 0.36 A ≈ 2.5 W を 15 ms 〔計算〕） |
| 10 | 娘のコイル駆動 | `TBD62083A` ×1／枚（8 出力＝SET1〜4・RESET1〜4、各出力に入力用＋出力用の 2 コイルを並列）。入力ごとに 100 kΩ のプルダウン | VCC ピンが無く、入力電圧だけで動く → **電源の無い娘でもリセットが届く**（固定事項）。1 出力 80〜91 mA 〔計算〕は 1 回路 ON の 400 mA [sw:L209] の内側 |
| 11 | ch の選択素子（リレー娘） | ch ごとに 2 コイルラッチ DPDT ×2（入力 L/R・出力 L/R）＝**8 個／枚**。部品は `AZ850P2-5` のまま（v1/v2 と同じ）、置換候補は `TQ2SA-L2-4.5V` | 2 コイル型なら**シンク専用の 1 石で SET/RESET とも駆動できる**（1 コイル型は極性反転のハーフブリッジが要る）。AZ850 の P2 は SET/RESET のコイルの＋端子が別ピン [AZ850 p2 図] |
| 12 | ch の電源 | ch ごとに `TPS7A49`／`TPS7A30`（±12 V、NOW どおり）＋ EN 保護（直列 R＋EN→IN ショットキー＋プルダウン）[NOW:L15, L17] | (ii) なので DC-DC の負荷が n に依らない（RS6 で +15 V 75 %）[DCS:L33] |
| 13 | 切り離した入力のバイアス | 入力リレーの **ch 側の接点に 100 kΩ のブリーダ**（L/R、ch ごと）＋ **TONE バスに親で 100 kΩ のプルダウン**（L/R） | 今の TONE バスには DC の基準が無い（ネットの構成員がコンデンサとコネクタだけ [SF nets TONE_L]）。リレーの両側を 0 V に置かないと、閉じた瞬間に段差が出る 〔推論〕 |
| 14 | 親のレベル線の出どころ | **親に MCP23017 を 1 個**（I²C は親の中だけ）。出力 8 本・入力 5 本 | Pico の空き GPIO は 7 本〔§3.12〕で 13 本に足りない。娘から見れば出どころが何でも線は静的 |
| 15 | 娘の配置 | **バックプレーン（親にスロット 4 口を横に並べる）**。縦積みはやめる | スロットごとに固有の線（切った ±15 V、EN×4、SET×4、RESET）があるので、縦に数珠つなぎにするとスロット番号をずらす仕掛けが要る 〔推論〕 |
| 16 | DC-DC | **`RS6-1215D` のまま**。理由は変わらず、むしろ強くなる | (ii) で負荷が n に依らない [DCS:L33]。加えて ⑦ の 0.1 A 制限で、ソケット短絡の +15 V が「150〜301 % が続く」[DCS:L269] から「最大 108 % が 4 ms で止まる」〔計算、§3.5〕に下がる |
| 17 | PT2314E＋L7809 | **+15 V から取る今の形のまま**（決定はユーザー、§7-D6） | (ii) なら RS6 の +15 V は 75 % で余裕がある。PD 12 V へ移すと +15 V が約 24 ポイント下がるが、PT2314E の 30〜40 mA の帰りが PD_GND–D_GND–A_GND の星を通る（ADC の付け替えと同じ種類の判断が要る） |

**アドレス・ジャンパは不要になる**（§3.12）。娘の上に番地が無いので「ジャンパ 6 段 → 娘 4 枚まで」[NOW:L43–48] の制約は消える。残る上限は、親のデコーダの幅（`CD74HC4514` 1 石で 4 枚×4 ch）、スロットごとのスイッチの数（部品代）、リセットの順次化の時間（1 枚 15 ms 増え）で、**DC-DC は (ii) なので枚数に依らない**。

### 0.2 今の図の分類（要約。詳細は §5）

| シート（部品数 [SF bom]） | 残す | 置き換える | 古い前提のためだけにある（外せる） | 足りない |
|---|---|---|---|---|
| ルート `AudioV2Case`（59） | 55（トーン・HP・入出力・±15 V 出力コンデンサ・コイルの PPTC など） | 4: `U201` REC20K→RS6、`F201` の値、`U403` BP5293→L7805C、`J_PWR101` のピン割当（×4 口） | 0 | スロット 4 口ぶんの ± スイッチ、デコーダ 3 石、ワンショット 5 石、POR 監視、親の MCP、TONE バスのプルダウン、給電確認の線、`J_ANA`/`J_PWR` の 2〜4 口目 |
| `AmpBankRelay`（20） | 12（リレー 4、TBD62083A、コイル局所 C 2、`J_ANA302`、穴 4） | 3（`C_BULK_*` 2 → ダンパ、`J_PWR302` のピン割当） | **5（MCP23017、その 100 nF、番地ジャンパ 3）** | 入力用リレー 4、ch の LDO 一式 ×4、EN 保護 ×4、TBD 入力のプルダウン 8、入力ブリーダ 8、ダンパ |
| `AmpBankSwitch`（23） | 変種を残すなら 13 | 変種を残すなら 5（TMUX を ch あたり 1 個に組み直し、ダンパ、ピン割当） | **5（MCP、100 nF、番地ジャンパ 3）**。変種をやめるならシートごと | 変種を残すなら境界リレー 2＋その駆動、ch の LDO 一式 ×4 |
| `AmpChannel`（17 × 8） | 17 全部（回路は変えない） | 電源ピン・デカップのネットだけ（`+15V`/`-15V` → ch の LDO 出力） | 0 | ch の LDO 一式（置き場所はこのシートか娘のシート） |

### 0.3 ユーザーに残る決定（詳細と要るデータは §7）

D1 TMUX 娘の変種を残すか／D2 リレーの品種（AZ850P2-5 のまま／TQ2SA-L2-4.5V／1 コイル型）／D3 リセットの順次化（1 枚ずつ＝推奨／同時／1 ch ずつ）／D4 −15 V スイッチ（ディスクリート＝推奨／LM5067）／D5 コイル電源（L7805C＝推奨／BP5293 のまま／ゲート）／D6 PT2314E の電源／D7 親の線の出どころ（親 MCP＝推奨／Pico 直）／D8 親のバルク +100 µF／D9 ダンパの形／D10 SET 前の整定待ち時間／D11 給電確認をどこで取るか

---

## 1. 前提（固定事項と、今の図の事実）

### 1.1 固定事項（ユーザー、[NOW:L9, L15–17, L22, L24] と依頼）

- 制御の木は 2 段。1 段目＝**娘 1 枚だけ給電**（親のデコーダからスロットごとのレベル線で娘の ±15 V を切る。バルク／ダンパはそのスイッチの後ろ、ソフトスタート）。2 段目＝**その娘の中で 1 ch だけバスへ**（**全リセット → 1 つだけセット**）。排他は親のデコーダで構造的に。**セットは給電中の娘にだけ届く**。**全リセットは電源の無い娘にも届く**（コイル駆動は常時系統）。**電源投入時の全リセットはハードで**
- 厳密に 1 ch だけ生かす [NOW:L9]。ヘッドホン 32 Ω。ADC タップは `AMP_SEL_L/R` [NOW:L12]。ADC の LDO は PD 12 V（`SW402` の後ろ）[NOW:L10]。PD は 12 V 固定 [NOW:L11]
- ソケットは ch ごとの正負 LDO で ±12 V、TMUX は LDO の前の ±15 V [NOW:L17]
- ユーザーはラッチングリレーを好む（聴取中に音声の近くを制御電流が流れない）

### 1.2 今の図から降ろした事実（この検討の出発点）

| 事実 | 出典 |
|---|---|
| 階層は `AudioV2Case` → {`MeasureControl`, `AmpBankSwitch`（AmpChannel×4）, `AmpBankRelay`（AmpChannel×4）, `FrontPanel`}。部品 355、参照の重複 0 | [SF tree], [SF bom] |
| 親のスロットは `J_ANA101`（2×5）と `J_PWR101`（2×8）の 1 口だけ。2 枚の娘シートはどちらも同じネット（`TONE_L/R`、`AMP_SEL_L/R`、`+15V`、`-15V`）に載っている | [SF pin J_ANA101 J_PWR101], [SF nets TONE_L / AMP_SEL_L / +15V] |
| `J_PWR*` の割当: 1 `+15V` / 2,4 `A_GND` / 3 `-15V` / 5 `+5V_COIL` / 6 `GND_COIL` / 7 `I2C_SDA` / 8 `D_GND` / 9 `I2C_SCL` / 10 `3V3` / 11〜16 未接続 | [SF pin J_PWR101 J_PWR301 J_PWR302] |
| ±15 V は娘まで**切らずに**来ている（娘の `C_BULK_*`、TMUX、全ソケットが `+15V`/`-15V` に直結） | [SF nets +15V], [SF pin C_BULK_P302 C608 AMP601] |
| リレー娘: `AZ850P2-5` ×4（ch ごと 1 個＝**出力 L/R だけ**）、`TBD62083APG` ×1、`MCP23017`（GPA0〜7 が CHk_SET/RST）| [SF pin K301 U321 U_IO302] |
| TMUX 娘: `TMUX7612` ×2（1 個で 2 ch の出力 L/R）、`MCP23017`（GPB0〜3 が SEL_CH1〜4）| [SF pin U311 U312 U_IO301] |
| **ch の入力は切り替えていない**: 8 ch 全部の入力コンデンサが `TONE_L/R` に直結 | [SF nets TONE_L]（`C602.1` など 8 個＋`C405.2`＋`J_ANA`×3） |
| `TONE_L/R` のネットに抵抗が 1 本も無い（PT2314E の出力側 2.2 µF と ch の 1 µF の間で DC が浮いている） | [SF nets TONE_L], [SF pin C405 C602 R601] |
| `AMP_SEL_L/R` は `R1659`（100 kΩ）で `A_GND` へ（DC は決まっている） | [SF pin R1659] |
| 出力側: ch の出力フィルム 2.2 µF の後ろ（リレー側）に 220 kΩ（`R603` 型）で `A_GND` | [SF pin R603 C601] |
| `+5V_COIL` は `PD_12V_SW` → PPTC 0.4 A（`F202`）→ `BP5293-50`（`U403`）。`GND_COIL`–`D_GND` は `NT101` | [SF pin F202 U403 NT101] |
| `+15V` → PPTC 0.1 A（`F203`）→ `L7809CV`（`U202`）→ `VCC_TONE` → `PT2314E` | [SF pin F203 U202 U402] |
| I²C（`I2C_SDA`/`SCL`）は Pico・UI の MCP（`U1610`）・PT2314E 側レベルシフタ・**2 枚の娘のコネクタ**に載っている | [SF nets I2C_SDA] |
| `3V3` は 2 枚の娘の MCP とアドレスジャンパにも来ている（娘の ±15 V と無関係に常時） | [SF nets 3V3] |
| Pico（`A1602`）で何も繋がっていないピン: 5, 6, 12, 19, 29, 32, 33, 34, 37, 39, 40 | [SF pin A1602] |
| 親子のシート界面の不一致 0 | [SF iface] |

---

## 2. 機能一覧（制御・電源・切替の木の全体）

### 2.1 親（母板）側

| # | 機能 | 何をするか | 今の図 |
|---|---|---|---|
| P1 | スロットのワンホット | {SLOT_A0, SLOT_A1, PWR_EN} → SLOT_ON_1..4（高々 1 本 High） | 無い |
| P2 | ch の EN デコード（(ii)） | {SLOT, CH, CH_ON} → EN_{s,c}（16 本、高々 1 本 High、静的） | 無い（NOW は娘に置く案 [NOW:L15]） |
| P3 | SET デコード | {SLOT, CH, SET パルス} → SET_{s,c}（16 本、パルス） | 無い（娘の MCP が出していた） |
| P4 | リセット → セットの順序器 | RST 要求 → RESET_1..4 を 1 枚ずつ順に（各 ≥ 10 ms）。リセット中は SET を禁止。SET パルスの幅もハードで決める | 無い |
| P5 | 電源投入時の全リセット | コイル電源が立ってから P4 を 1 回起動 | 無い |
| P6 | ±15 V の給電確認 | スロットごとに「+15 V と −15 V が上がっている」を読む | 無い（NOW で娘に検知線を足す予定 [NOW:L15]） |
| P7 | スロットごとの ±15 V スイッチ | SLOT_ON_k で娘 k の ±15 V を入れる。ソフトスタート（RS6 で ≥ 26 ms [DCS:L176]）、電流制限 | 無い（±15 V は常時娘へ） |
| P8 | コイル電源 | 常時。全リセットの電流を 1 枚ぶん出せる | `F202`＋`U403` |
| P9 | 線の出どころ | P1〜P4 の入力を出し、P6 を読む（MCU の GPIO か親の I/O 拡張） | Pico＋娘の MCP |
| P10 | バスの DC 基準 | `TONE_L/R` を 0 V に置く | **無い** |

### 2.2 娘側（ベースライン＝リレー娘 4 ch、(ii)）

| # | 機能 | 何をするか | 今の図 |
|---|---|---|---|
| D1 | 電源の入口 | 切られた ±15 V_SW を受ける | `J_PWR30x`（±15 V は切られていない） |
| D2 | バルク／ダンパ | 娘の LDO 入力網を減衰させる（電荷の溜めではない [NOW:L19]） | `C_BULK_P/N` 100 µF |
| D3 | (i) の場合: 娘 1 組のレギュレータ | —（ユーザーは (ii) を選んだ。§3.9 に比較だけ残す） | — |
| D4 | (ii): ch ごとの正負 LDO＋EN 保護 | EN_{s,c} で ch の ±12 V を入れる。正 LDO の EN が IN を超えないよう保護 | 無い |
| D5 | ch の選択素子＝バス境界 | 入力リレー（TONE→ch）と出力リレー（ch→AMP_SEL）。ラッチ | 出力側だけ `K30x` |
| D6 | （TMUX 変種のみ）娘の境界リレー | 電源の無い TMUX をバスから切る | 無い |
| D7 | コイル駆動 | SET_{s,c}・RESET_s → コイルのシンク | `U321` |
| D8 | 切り離した入力のバイアス | オペアンプ入力（100 kΩ、既存）＋ 入力リレーの ch 側のブリーダ | 前者だけ |
| D9 | 局所デコード | **ベースラインでは無し**（M1 案でだけ要る） | 娘の MCP |

### 2.3 界面（スロットごとのコネクタ）とファーム

- **界面**: ±15 V_SW、A_GND、コイル電源と帰り、EN×4、SET×4、RESET×1、（任意で給電確認の戻り）、音声 4 本＋ガード。本数は §4
- **ファーム**: 切替手順（ミュート → 全リセット → 旧 ch の EN を落とす →（枚が変わるなら）旧スロット OFF → 新スロット ON・確認 → 新 ch の EN → 整定待ち → SET → ミュート解除）、故障の検出と表示、起動後のもう一度の全リセット。§3.13

---

## 3. 機能ごとの最小部品構成と選択肢（DS の事実つき）

### 3.1 P1 スロットのワンホット

| 案 | 部品 | 効く DS の事実 | 備考 |
|---|---|---|---|
| **P1-a（推奨）** | `CD74HC238` ×1（親） | 3→8、選ばれた出力だけ High、G2（正）・G̅0・G̅1（負）の 3 つのイネーブル、いずれかで無効にすると全出力 Low [CD74HC238 p1]。HC は 2〜6 V [p1] | A0/A1＝SLOT、A2＝0、G2＝PWR_EN（10〜100 kΩ でプルダウン 〔推論〕）。出力は TPS2660 の SHDN（≤ 4 V [TPS2660 p6]）と −15 V 側の PNP を直接駆動。VCC は 3.3 V にする（SHDN の推奨上限 4 V のため）〔推論〕 |
| P1-b | `SN74LVC1G139`（2→4、出力は Low 有効、イネーブル無し）[SN74LVC1G139 p10 Table 4] | 常にどれか 1 本が選ばれていて「全 OFF」が無い → PWR_EN で後段をゲートする部品が別に要る 〔推論〕 | 不採用 |
| P1-c | MCU の GPIO 4 本を直接 | ファームが 2 本立てれば 2 枚通電する（構造的排他にならない） | 固定事項に反する |

### 3.2 P2 ch の EN デコード（(ii)）と P3 SET デコード

| 案 | 部品 | 効く DS の事実 | 備考 |
|---|---|---|---|
| **P2/P3-a（推奨）** | `CD74HC4514` ×2（親）。#1＝EN（E̅＝CH_ON̅、プルアップで既定 OFF）、#2＝SET（E̅＝SET ワンショットの Q̅） | 4 bit のラッチ＋4→16 デコーダ、選ばれた出力が High、**E が High で全出力 Low** [CD74HC4514 p1]。LE が High でラッチは透過 [p1]。HC 2〜6 V [p1] | アドレス A0..A3 ＝{CH_A0, CH_A1, SLOT_A0, SLOT_A1}。**#1・#2・P1 がスロットの 2 本を共有**するので、EN と SET は給電デコーダが指すスロット以外へ出られない（配線で決まる）。アドレスは E を無効にしてから変える（ファームの順序）〔推論〕 |
| P2/P3-b | 娘ごとのデコーダ（M1 案、§3.12） | `SN74LVC1G139` は Ioff（VCC = 0 で ±5 µA）あり [SN74LVC1G139 p6] だがイネーブル無し。`SN74LVC138A` はイネーブルあり・**Ioff の記載が DS に無い** [SN74LVC138A 全文検索] | 電源の無い娘の入力を生きた線が駆動するので Ioff が要る 〔推論〕。条件を両方満たす 1 石が手元の DS に無く、ゲートを足すことになる |
| P2-c | EN を SET と同じ線にする | EN は静的、SET はパルス。リレー娘では兼ねられない | TMUX 変種では EN と SEL を 1 本で兼ねられる（§3.10） |

### 3.3 P4 リセット → セットの順序器（BBM）と**コイル駆動の結果（定量）**

#### 3.3.1 コイル電流（ユーザー依頼の定量）

1 ch あたり 2 コイルラッチ DPDT が 2 個（入力 L/R＋出力 L/R）→ **1 枚 8 個**、4 枚で **32 個のリセットコイル**。

| 品種（5 V 定格） | 1 コイルの電流（DS）／ 最悪〔計算: 抵抗 −10 %、5.1 V〕 | 最小パルス幅 | セット/リセット時間 | 出典 |
|---|---|---|---|---|
| **AZ850P2-5**（2 コイル、今の石） | 125 Ω → 40 mA 〔計算〕／ 45.3 mA | **DS に無い** | 2 / 1 ms typ | [bnd:L439–L443], [sw:L164, L169–L170] |
| AZ850P1-5（1 コイル） | 250 Ω → 20 mA 〔計算〕／ 22.7 mA | DS に無い | 2 / 1 ms typ | [bnd:L437–L438, L442] |
| G6KU-2（1 巻線ラッチ）5 V | 21.1 mA、237 Ω ／ 23.9 mA | **10 ms** | 3 / 3 ms max | [bnd:L465, L467–L468] |
| TQ2-L2-5V（PC 板、2 コイル） | 各 40 mA、125 Ω ／ 45.3 mA | **10 ms 以上を推奨** | 3 / 3 ms max | [bnd:L495, L501–L502] |
| TQ2SA-L2-5V（表面実装、2 コイル） | 各 28.1 mA、178 Ω ／ 31.8 mA | 同上 | 4 / 4 ms max | [bnd:L498, L501] |
| TQ2-L-5V（PC 板、1 コイル） | 20 mA、250 Ω ／ 22.7 mA | 同上 | 3 / 3 ms max | [bnd:L494] |
| TQ2SA-L-5V（表面実装、1 コイル） | 14 mA、357 Ω ／ 15.9 mA | 同上 | 4 / 4 ms max | [bnd:L497] |
| FTR-B3（1 コイル、**5 V 品は無い**、4.5 V） | 203 Ω → 22.2 mA @4.5 V 〔計算〕 | DS に無い（グラフのみ） | 3 / 3 ms max | [bnd:L541–L546] |

**同時に流れる電流**〔計算〕:

| 品種 | 1 ch（2 コイル） | 1 枚（8 コイル） | **4 枚同時（32 コイル）** |
|---|---|---|---|
| AZ850P2-5 / TQ2-L2-5V | 80 / 91 mA | 320 / **362 mA** | **1280 / 1450 mA** |
| TQ2SA-L2-5V | 56 / 64 mA | 225 / 254 mA | 899 / 1018 mA |
| AZ850P1-5 / TQ2-L-5V（1 コイル） | 40 / 45 mA | 160 / 181 mA | 640 / 726 mA |
| G6KU-2 | 42 / 48 mA | 169 / 191 mA | 675 / 765 mA |
| TQ2SA-L-5V（1 コイル） | 28 / 32 mA | 112 / 127 mA | 448 / 509 mA |

（公称 / 最悪。TBD62083A の電圧降下 0.2 V typ・0.325 V max @100 mA [sw:L215] で実際は少し減る）

比べる相手:
- **コイル電源の枝の PPTC `F202` は保持 0.4 A**（図の値 [SF pin F202]、型番 `RXEF040` [NOW:L222]。**トリップ時間の DS は未取得**＝短いパルスで切れないかは未確認）
- `BP5293-50` の最大出力電流 1000 mA [BP5293 p1, p3]。ベースラインの `L7805C` は短絡電流 0.75 A typ [L78 p14]
- `TBD62083A`: 1 回路 ON で 400 mA/ch、8 回路同時 ON は Ta = 85 °C・25 ms・Duty 10 % で FG 320 mA/ch・PG 390 mA/ch [sw:L209–L210]

**読み**: 2 コイル型で 32 個同時は 1.28〜1.45 A で**どの電源にも入らない**。1 枚ずつなら最悪 362 mA で PPTC 保持の 91 %、BP5293 の 36 %（L7805C の短絡電流 0.75 A typ の 48 %）〔計算〕。

#### 3.3.2 選択肢と、リセット → セットの時間への効き

パルス幅は **15 ms**〔仮定: G6K の最小 10 ms・TQ の推奨 10 ms 以上 [bnd:L468, L502] を下限とし 1.5 倍。AZ850 は DS に無い [bnd:L443]〕、リセットとセットの間の空きは **5 ms**〔仮定: ラッチ型のバウンス時間はどの DS にも無い [bnd:L554]。値があるのは非ラッチ G6K-2G の 0.2〜0.8 ms のヒストグラムだけ [bnd:L474]〕。

| 案 | 中身 | 同時電流（最悪） | リレーの手順の時間〔計算〕 | 部品 |
|---|---|---|---|---|
| R-a 同時全リセット | RESET を 1 本で全娘へ | 1450 mA（AZ850P2）/ 1018（TQ2SA-L2）/ 509（TQ2SA-L） | 15 + 5 + 15 = **35 ms** | 最少。ただし 2 コイル型では電源が足りない |
| **R-b 1 枚ずつ（推奨）** | 親の順序器が RESET_1→2→3→4 と 15 ms ずつ | **362 mA**（AZ850P2）/ 254（TQ2SA-L2） | 4×15 + 5 + 15 = **80 ms** | `SN74LVC1G123` ×4 の連鎖＋ダイオード 4 本（リセット中の判定） |
| R-c 1 ch ずつ | 16 段 | 91 mA | 16×15 + 5 + 15 = **260 ms** | 順序器が 16 段（カウンタ等）。利点は電源が小さくて済むことだけ |
| R-d 1 コイル型に替える | コイル電流が半分。**極性反転が要る**: 娘ごとに共通端（COM）と ch 端の両方にソース／シンクのハーフブリッジ（TBD62083A はシンク専用 [sw:L201]） | R-a で 726 mA（AZ850P1）/ 509（TQ2SA-L） | R-a と同じ 35 ms（最小幅は同じ 10 ms [bnd:L468, L502]） | 駆動 IC が 1 枚 2 個に増える（ソース側の石は**未選定・DS 未取得**） |
| R-e 4 極品で 1 ch 1 個に | コイル数が半分（1 枚 4 個） | R-a で 725 mA（AZ850P2 相当なら）〔計算〕 | 35 ms | **手元の DS に 4 極のラッチ信号リレーは無い**: AZ850・G6K・TQ・G5V-2・FTR-B3 はすべて DPDT／2 Form C [bnd:L421, L454, L479, L513, L529]。追加で取った **Panasonic DS リレーの現行カタログ（2026.7）も 1 Form C だけ** [Panasonic_DS p2–p3] → **裏の取れる候補が無いので案として立てない** |

**時間の効きの比較**: 切替 1 回の中で、リレーの手順以外に必ず入る待ちは、
- ch の LDO のソフトスタート: TPS7A49 で tSS = 1.4 × CNR [nF] ms → 10 nF で 14 ms [pow:L225]（TPS7A30 は 0.9 倍 [pow:L353]）
- **出力カップリングの整定**: 2.2 µF × 220 kΩ = τ 0.48 s 〔計算、[SF pin C601 R603]〕。音が出る前に 3τ ≈ 1.5 s 待つ 〔仮定〕。入力側は 1 µF × 100 kΩ = 0.1 s
- 枚が変わるときだけ: スロットのソフトスタート ≥ 26 ms [DCS:L176]

したがって **R-b で増える 45 ms は切替全体（約 1.6 s）の 3 % 程度**〔計算〕。聴き比べの切替時間を決めているのはリレーではなく**カップリングコンデンサの整定**。

#### 3.3.3 順序器の最小構成（R-b）

- `SN74LVC1G123` ×4 を連鎖: 段 k の Q の立ち下がり（パルスの終わり）→ 段 k+1 の A（立ち下がりでトリガ、B = High）。出力パルス幅は Rext·Cext で決まり、表値は Cext 0.1 µF・Rext 10 kΩ で 1〜1.1 ms [SN74LVC1G123 p7] → 15 ms には Cext 約 1.5 µF 〔推論: 表の比例。K は同 DS の Figure 5-6 で確認すること〕。Rext/Cext を GND・VCC に直結しない [p5]。**電源投入時に出力がグリッチしない**・CLR̅ でパルスを打ち切れる・Ioff [p1]
- 段 1 のトリガ: A ← RST_REQ̅（MCU。起動中は Hi-Z → **プルダウン**で Low）、B ← POR 監視の RESET̅（§3.4）。起動時は A = Low のまま B の立ち上がりで、通常時は B = High のまま A の立ち下がりで起動 〔推論: DS の 3 つのトリガ方法 [p1] の組み合わせ〕
- **リセット中の判定**（RST_BUSY̅）: 4 段の Q̅ をダイオード AND（プルアップ 1 本）→ SET 用ワンショットの CLR̅ へ。**リセット中は SET が出ない**＝TQ の「セットとリセットのコイルに同時に電圧を加えない」[bnd:L504] をハードで守る
- SET 用 `SN74LVC1G123` ×1: A ← SET_REQ̅、**B ← PWR_EN**（給電していなければトリガしない）、CLR̅ ← RST_BUSY̅、Q̅ → `CD74HC4514`#2 の E̅。**幅がハードで決まる**ので、ファームが止まってもコイルに連続通電しない 〔推論: エッジトリガ〕
- 出力の駆動: LVC の 3.3 V 出力で TBD62083A の入力（ON に 2.5 V 以上、入力電流 ≤ 0.1 mA [sw:L216, L219]）を直接。1 本の RESET_s は娘の 4 入力、SET は 1 入力

### 3.4 P5 電源投入時の全リセット

| 案 | 部品 | 効く DS の事実 | 備考 |
|---|---|---|---|
| **P5-a（推奨）** | `TPS3808G01`（可変、VIT 0.405 V [TPS3808 p3]）＋分圧で閾値 ≈ 4.2 V | RESET̅ はオープンドレイン、SENSE が VIT を超えてから遅延 td の間 Low [p4]。CT 開放で td 12 / 20 / 28 ms [p7]。VDD 1.7〜6.5 V [p5] | RESET̅ の**立ち上がり**で §3.3.3 の連鎖を起動。閾値 4.2 V は感動電圧 3.75 V [sw:L165] より上、L7805C の出力下限 4.75 V [L78 p14] より下 〔計算〕 |
| P5-b | `TPS3808G50`（固定 VIT 4.65 V [p3]、精度 ±2 %（3.3 V < VIT ≤ 5 V）[p5–p6]） | VIT の上限 4.74 V 〔計算〕と L7805C の下限 4.75 V の差が 0.01 V | L7805C と組むと解除しない恐れ。BP5293（4.9〜5.1 V [BP5293 p4]）となら可 |
| P5-c | RC＋シュミット | — | 部品は減るが閾値が定まらない。不採用 |

- 起動時の他の既定: PWR_EN・CH_ON・SET_REQ・RST_REQ は親の MCP の POR（全ピン入力＝Hi-Z [sw:L252]）の間、プル抵抗で「OFF・要求なし」に置く 〔推論〕
- **TQ と G6K は「リセットで出荷・衝撃で変わりうる・使う前に初期化」と明記** [bnd:L471, L506]（AZ850 には記載なし [bnd:L448]）。P5 はこれへの答え。ファームも起動後にもう一度全リセットを出す（§3.13）

### 3.5 P7 スロットの ±15 V スイッチ（ソフトスタート・電流制限）と P6 給電確認

要求〔[DCS:L176, L269, L285]〕: ソフトスタート ≥ 26 ms（(ii) n=4、RS6 の 80 %）、ソケット短絡を DC-DC の手前で止める。娘 1 枚の定常は (ii) で +15 V 20 mA 程度（ソケットの最悪 20 mA [DCS:L54]＋TMUX 分）。

#### +15 V 側

| 案 | 部品 | 効く DS の事実 | 判定 |
|---|---|---|---|
| **P7+-a（推奨）** | `TPS26600`（HTSSOP-16）＋ R_ILIM 120 kΩ ＋ C_dVdT 220 nF ＋ UVLO 分圧 ＋ SHDN プルダウン 33〜47 kΩ | 4.2〜60 V、電流制限 0.1〜2.23 A 可変 [TPS2660 p1]。R_ILIM 120 kΩ で I(OL) **0.085 / 0.1 / 0.115 A**、短絡時 I(SCL) 0.08 / 0.1 / 0.12 A [p7, p8]。R_ILIM の推奨 5.36〜120 kΩ [p6]。**内蔵 UVLO は立ち上がり 14.25 / 14.9 / 15.75 V** [p7] → 15 V の入力では解除されない恐れ → 外付け分圧（V(UVLOR) 1.175〜1.225 V [p7]）必須。SHDN は内部で 2〜3.4 V に上がる出力を持ち、0.4 V で −10 µA [p7]、閾値（下降）0.55〜0.94 V [p7]、推奨上限 4 V [p6]。tdVdT = 8×10³ × VIN × C(dVdT) [p21 式 2]。過負荷の応答は MODE で選ぶ（回路ブレーカ＋自動再試行／ラッチオフ、電流制限＋自動再試行／ラッチオフ）[p21–p22 Table 1]、ブレーカの FLT 遅延 4 ms、再試行 540 ms [p9]。SHDN↓ から FLT↓ まで 10 µs [p9]。IQ(ON) 190 / 300 / 390 µA、IQ(OFF) 11 / 20 / 33 µA [p7] | ○。**C_dVdT = 26 ms / (8×10³ × 15 V) = 217 nF → 220 nF で 26.4 ms**〔計算〕。そのときの突入 98.8 µF [DCS:L165] × 15 V / 26.4 ms = **56 mA** ＜ I(OL) min 85 mA（起動中に制限へ入らない）〔計算〕。SHDN のプルダウン: 10 µA × R ＜ 0.55 V → R ＜ 55 kΩ 〔計算〕。**FLT は「ON かつ故障なし」で High** → そのまま給電確認に使える |
| P7+-b | `TPS22810`（負荷スイッチ）＋ CT | VIN 2.7〜18 V、絶対最大 20 V [TPS22810 p1]、EN 閾値 1.13〜1.3 V [p5]、CT 27 nF で立ち上がり 5.46 ms（12 V）/ 8.23 ms（18 V）[p17 Table 2]、熱遮断あり・**電流制限の記載なし** [p1] | ×（電流制限が無い）。コイル電源のゲートには使える（§3.6 C2） |
| P7+-c | `TPS7A49` をスイッチ兼用 | EN high 2.1 V〜VIN [pow:L195]、電流制限 220 / 309 / 500 mA [pow:L189]、IOUT 150 mA [pow:L159] | ×（制限が RS6 の 200 mA より上。ソケット短絡を止めない [DCS:L269]） |
| P7+-d | ディスクリート（PMOS＋ゲート RC＋PNP の電流制限） | —（汎用品。DS は未取得） | △（制限を 30〜60 mA に置けるが精度は VBE の温度次第 〔推論〕） |

**ソケット短絡での RS6**〔計算〕: 親の定常 max 101.8 mA [DCS:L98] ＋ I(OL) max 115 mA ＝ 217 mA（108 %）が、ブレーカなら 4 ms で切れる（自動再試行なら 4 / 544 ms ≈ 0.7 % のデューティ）。これまでの「LDO の 220〜500 mA が素通しで 150〜301 %」[DCS:L269] から大きく下がる。ただし 100〜150 % は RS6 の OLP が働かない帯 [DCS:L278] なので、**ラッチオフの MODE を選ぶ**のが安全側 〔推論〕。

#### −15 V 側

| 案 | 部品 | 効く DS の事実 | 判定 |
|---|---|---|---|
| **P7−-a（推奨）** | ディスクリート: NMOS（−15 V の線、ソースが −15 V 側）、R_GS（既定 OFF）、ゲート–ソース間ツェナー、**PNP のレベルシフト**（エミッタ抵抗を SLOT_ON 線へ、ベースを GND → 線が 3.3 V のとき 〔(3.3−0.7) V / R_E〕 をゲートへ流す）、ゲート–ドレイン間 C でソフトスタート、ソースの検出抵抗＋NPN で電流制限（例 10 Ω で約 60 mA）、**−15 V_SW の検知**＝+3.3 V と −15 V_SW の間の 2 抵抗の中点＋GND へのショットキー（−15 V があると Low） | 汎用品（DS 未取得）。立ち上がり dV/dt ≈ I_gate / C_GD 〔推論〕→ 118 µA（R_E 22 kΩ）/ 220 nF で 26 ms 〔計算〕 | ○（部品 8〜10 個／口。**ベンチかシミュレーションで確かめること**） |
| P7−-b | `LM5067`＋NMOS＋R_S | 動作範囲 −9〜−80 V [LM5067 p1]。VCC は VEE から 13 V（12.35 / 13 / 13.65 V）の内蔵シャント [p6]、**VCC への電流の推奨は最小 2 mA** [p5]。UVLO/EN の閾値は VEE から 2.5 V 上 [p4]。電流制限 VCL 44 / 50 / 56 mV [p6]（R_S 1 Ω で 44〜56 mA）。PGD は VEE 基準のオープンドレイン [p4]。LM5067-1 はラッチオフ [p1] | △: **VEE = −15 V だと VCC の抵抗に掛かるのは 1.35〜2.65 V** 〔計算: 15 − VZ〕→ 2 mA には R ≤ 675 Ω。RS6 が −1 % の −14.85 V で 1.78 mA、クロスで −5 % なら 0.9 mA と推奨を割る 〔計算〕。加えて UVLO/EN と PGD のレベルシフトが P7−-a と同じだけ要る |
| P7−-c | `TPS7A30` をスイッチ兼用 | EN は正論理でも動く（VEN(+HI) 2〜15 V）[pow:L321] ＝レベルシフト不要。電流制限 220 / 330 / 500 mA [pow:L316]。ドロップアウト 216 mV @100 mA [pow:L314] | ×（制限が RS6 の 200 mA を守らない。出力が −15 V よりドロップアウトぶん浅くなる） |

**P6 給電確認**: スロットごとに「TPS2660 の FLT（オープンドレイン）」と「−15 V_SW の検知」をワイヤード AND して 1 本（SLOT_PG_k）〔推論〕→ 親の MCP の入力へ 4 本。親で取るので**娘の検知線（[NOW:L15]）は要らなくなる**。コネクタの接触まで確かめたいなら、空きピン 1 本で娘側から折り返す（§4）。

### 3.6 P8 コイル電源（常時）

| 案 | 部品 | 効く DS の事実 | 判定 |
|---|---|---|---|
| C1 今のまま | `BP5293-50`（PD 12 V から） | 出力 4.9 / 5.0 / 5.1 V、リプル 50 / 200 mVp-p（Io 500 mA）[BP5293 p4]、PWM 570 kHz typ、**軽負荷では SLLM でスイッチングを止める（間欠）** [p5]、最大 1 A [p3]、UVLO 6.4 V typ [p4] | △: 聴取中（コイル電流 0）は軽負荷側。その出力が全娘の `+5V_COIL` に配線され、娘の上で L/R の近くを通る [NOW:L110, L114] |
| **C3（推奨）** | `L7805C`（PD 12 V からのリニア）＋最小負荷 5 mA 用の抵抗 | VO 4.75〜5.25 V（IO 5 mA〜1 A、VI 7〜18 V）、Id max 8 mA、**最小負荷 5 mA**（脚注 a）、短絡電流 0.75 A typ、ドロップアウト 2 V typ @1 A [L78 p14 Table 10] | ○: スイッチングが無い。1 枚ぶんのリセット 362 mA のとき損失 (12 − 5) × 0.362 ≈ 2.5 W を 15 ms、4 枚で 60 ms 〔計算〕。待機は 12 V × (8 + 5) mA ≈ 0.16 W 〔計算〕。PPTC `F202` はそのまま前に置く |
| C2 ゲート | C1 か C3 の後ろに `TPS22810`（EN ＝ ファームの COIL_EN ∨ 起動時の窓） | EN 1.13〜1.3 V [TPS22810 p5]、QOD あり [p1] | △: 聴取中は娘の `+5V_COIL` が 0 V。ただし全リセットが「常時系統から」[固定事項] と言えるかは解釈が分かれる。部品と論理が増える |

### 3.7 D7 娘のコイル駆動と D5 リレー

- **`TBD62083A` ×1／枚**: 8 回路のシンク、各出力にクランプダイオード（カソードは COMMON）[sw:L201, L227]。入力は ON に 2.5 V（100 mA）、OFF は 0.6 V 以下 [sw:L216–L217]、入力電流 ≤ 0.1 mA [sw:L219]。**入力抵抗・プルダウンの値は DS に無い** [sw:L236] → 入力ごとに 100 kΩ で A_GND…ではなく **GND_COIL** へプルダウン（コネクタが外れても OFF）〔推論〕。過電流保護は内蔵しない [sw:L232]
- 割当: OUT1〜4 ＝ SET_ch1〜4（入力リレーと出力リレーの SET コイルを並列）、OUT5〜8 ＝ RESET_ch1〜4（同）。RESET_s は 4 入力を並列に 1 本で駆動 〔推論〕
- **AZ850P2 は SET コイルが 1(+)–5(−)、RESET コイルが 10(+)–6(−)** [AZ850 p2 図、自分で画像を確認]。＋端子が別なので、「SET コイルの＋だけを娘の切られた電源から取る」ことで、**電源の無い娘は物理的にセットできない**形にもできる（§7-D2 の付記。ベースラインは親のデコードで足りるとして採らない）〔推論〕
- **TQ を使うなら 4.5 V 品**: TQ の DS は「5 V のトランジスタ駆動では 4.5 V 品を推奨」「定格の ±5 % 以内で使う」[bnd:L499–L500]。TBD62083A の降下 0.2〜0.325 V（100 mA）[sw:L215] で 5 V 品は 93〜96 % になる 〔計算〕。**4.5 V 品のコイル値は boundary.md に無い**（5 V 品だけ）
- コイルの局所の溜め `C321`（100 µF）[SF pin C321] は残す（パルスの立ち上がりを娘の中で賄う）

### 3.8 D1/D2 娘の電源入口とダンパ

- 形は既存の議論に従う（本書では決め直さない）: NOW の RC ダンパ（22 µF MLCC＋直列 0.15 Ω、35〜45 µF）[NOW:L19–L20]、または [BPS] の (3)（娘の ± 給電に直列 0.33 Ω、ch LDO の CIN 10 µF）[BPS:L42–L46]
- 本構成での変化: スイッチが親にあるので、切ったスロットのコネクタは死んでいる。**[BPS] が (3) を推した理由の 1 つ（活線挿入で親が 3.2 V まで落ちる）[BPS:L48–L49] はソフトスタートと電流制限で消える**。残る理由は伝達関数（コネクタの L と娘のセラミックの共振）[BPS:L46] 〔推論〕
- RS6 の起動時に見える容量は親だけ（娘は既定 OFF）[DCS:L37]

### 3.9 D4 ch の電源（(ii)）と、(i) との比較（記録）

- **(ii) ベースライン**: ch ごとに `TPS7A49`（EN high 2.1 V〜VIN [pow:L195]、**EN–IN の絶対最大 +0.3 V** [pow:L146]）と `TPS7A30`（**EN–GND ±36 V** [pow:L280]、正論理の EN 2〜15 V [pow:L321]）。EN_{s,c} は親の `CD74HC4514` の 3.3 V 出力 → 娘で EN 保護（直列 R＋EN→IN ショットキー＋プルダウン）[NOW:L15]。例: 直列 10 kΩ・プルダウン 100 kΩ で EN ≈ 3.0 V ≥ 2.1 V 〔計算〕。正 LDO だけが EN 保護を要する（負 LDO は EN が正でも絶対最大の内側）〔推論: [pow:L146] と [pow:L280] の比較〕
- DC-DC の負荷（RS6、max・HP 歪み始め）: **+15 V 150.3 mA（75 %）、−15 V 101.9 mA（51 %）、合計 63 %**。typ・無音の −15 V 26.7 %（≥ 25 %）[DCS:L84, L220]。本構成で増える ±15 V の負荷は TPS2660 の IQ 0.4 mA 以下と −15 V 側の R_GS 程度 〔計算〕
- (i) を選ばない理由（記録）: RS6 で n = 2 は +15 V 85 %、n = 4 は 105 %（定格超過）[DCS:L92, L96]、かつ「厳密に 1 ch だけ生かす」[NOW:L9] に反する

### 3.10 D5/D6 ch の選択素子・境界、TMUX 変種

- **リレー娘（ベースライン）**: ch ごとに入力リレー（TONE_L/R → ch）と出力リレー（ch → AMP_SEL_L/R）。**このリレーが ch のバス境界**（ユーザー決定）。聴取中のコイル電流 0、境界の静電容量は開接点間 0.4 pF typ [sw:L184]
- **TMUX 変種（任意）**: ch ごとに `TMUX7612` 1 個（4 SPST [sw:L19] ＝ 入力 L/R＋出力 L/R）を娘の ±15 V_SW（LDO の前）に。SEL は**その ch の EN 線をそのまま**（SEL は内部プルダウン [sw:L20]、VIH 1.3 V [sw:L24]、VSEL は 0〜44 V 推奨・−0.5〜53 V 絶対最大 [sw:L43, L48]）。**TMUX7612 には電源断時の規定が無い** [bnd:L55] ので、娘の端に**境界リレー 2 個**（入力 DPDT・出力 DPDT、2 コイルラッチ）＋その駆動（TBD62083A の 2 回路、または小信号トランジスタ 2 個）。全リセットで効くのは 1 枚 2 コイル（最悪 91 mA）〔計算〕
- 聴取中に娘に流れる制御: リレー娘は EN 1 本の DC（EN 電流 0.02〜1 µA [pow:L194]）だけ。TMUX 変種はそれに加えて TMUX の電源電流（全 ON 435 / 480 µA、±16.5 V [sw:L62]）と SEL の DC

### 3.11 D8/P10 切り離した入力のバイアスとバスの DC

- オペアンプの入力: 既存の 100 kΩ（`R601` 型）で A_GND へ [SF pin R601] → **残す**。(ii) で電源の無い ch も 0 V に置かれる
- **入力リレーの ch 側の接点**（リレーと 1 µF の間）: 100 kΩ のブリーダを新設 〔推論〕。無いと、開いている間この節点が浮き、閉じたとき 1 µF の両端の差がそのまま段差になる。100 kΩ なら放電 τ = 1 µF × 200 kΩ = 0.2 s 〔計算〕、選択時の TONE の負荷は 100 kΩ ∥（100 kΩ＋1 µF）で PT2314E の最小負荷 5 kΩ [sw:L300] より十分重くない
- **TONE バス**: 親で `TONE_L/R` に 100 kΩ のプルダウンを新設 〔推論〕。今は DC の基準が無い [SF nets TONE_L]（PT2314E の出力の DC は 0.5 VDD [sw:L302] で、2.2 µF で切られている [SF pin C405]）
- 出力側: ch 側は 220 kΩ（`R603` 型）[SF pin R603]、バス側は `R1659` 100 kΩ [SF pin R1659] で両側とも決まっている → 足すもの無し

### 3.12 P9 線の出どころ — 娘の MCP を外す案と残す案（依頼の比較）

| 案 | 娘の上 | 親の上 | 聴取中に娘へ来る信号 | 構造的排他 | ジャンパ | 備考 |
|---|---|---|---|---|---|---|
| **M0（推奨）: 娘に MCP 無し、デコード全部親** | TBD62083A、リレー（変種は TMUX）だけ。**ロジック IC 0** | CD74HC238、CD74HC4514 ×2、LVC1G123 ×5、TPS3808、線の出どころ（親 MCP か Pico） | **EN 1 本の DC だけ** | ○（デコーダ 3 石が同じスロット線） | **不要** | ピンは n に比例（§4） |
| M1: 娘に MCP 無し、娘でデコード | Ioff 付きのデコーダ＋ゲート、その電源（切られた +15 V から小 LDO） | CD74HC238、順序器 | 静的な線（CH_A・CH_ON）だけ | ○（電源の無い娘のデコーダは出力しない。**Ioff が要る** [SN74LVC1G139 p1, p6]） | 不要 | 条件（Ioff＋イネーブル）を 1 石で満たす DS が手元に無い（§3.2）。娘に IC と電源が増える |
| I1: 娘ごとに I²C 拡張（v2） | MCP23017（`3V3` で常時給電 [SF nets 3V3]）、番地ジャンパ、**その後ろに 1 ch デコーダ**（MCP の出力はソフトなので [NOW:L15]） | CD74HC238、POR 用の RESET 線 | **I²C のクロック**: バスは PT2314E・UI の MCP と共有 [SF nets I2C_SDA]。トーン操作（PT2314E への書き込み）やエンコーダ読み出しのたびに全娘のコネクタへ SCL/SDA のエッジが来る | △（デコーダを足せば） | **要る**（番地は 3 bit、UI が 0x22 を使う → 娘 ≤ 6〜7 枚 [NOW:L47]） | MCP の POR は全ピン入力 [sw:L252] → 全出力にプルダウン。常時給電の MCP が電源の無い娘の EN/SEL を駆動 → EN 保護が必須。**MCP を娘の電源から給電すると、生きた I²C に電源の無い MCP がぶら下がる**（他ピンの絶対最大 VDD + 0.6 V [sw:L251]）。POR の全リセットは MCP では作れない（別線が要る） |
| I2: I²C 拡張を親に 1 個 | M0 と同じ | M0 ＋ MCP23017 ×1 | M0 と同じ | ○ | 不要 | M0 の「線の出どころ」をこれにする＝**ベースライン** |

**線の出どころ（M0 の中の選択）**: 親の論理が要る本数は、出力 8（SLOT_A0/A1、CH_A0/A1、PWR_EN、CH_ON̅、SET_REQ̅、RST_REQ̅）＋入力 5（SLOT_PG_1..4、RST_BUSY）＝ 13 〔計算〕。Pico の未接続ピン 11 本 [SF pin A1602] のうち GPIO は 7 本〔推論: Pico 2 のピン配置による。ボードの DS はリポジトリに無く未照合。33 は GND、37 は 3V3_EN、39 は VSYS、40 は VBUS〕→ 足りない。**親に MCP23017 を 1 個**（I²C は親の中だけ。書き込むのは切替のときだけ）。ワンショットがパルス幅を決めるので、SET/RST の要求も I²C の書き込みで出してよい 〔推論〕。

**クロックのある信号が聴取中に娘へ来ない案**: M0、M1、I2。I1 は来る（娘用に I²C を分けて聴取中は触らない、またはバススイッチで切る、というファームかハードの追加が要る）。

**ジャンパ**: M0・M1・I2 では娘の番地が無いので**ジャンパは要らない**。「娘 4 枚まで」の理由は消え、上限は §0.1 の末尾のとおり。

### 3.13 ファームの責務と切替の時間

1. **起動**: 親の MCP を設定（PWR_EN = 0、CH_ON̅ = 1、要求なし）→ ハードの POR リセットが終わったことを RST_BUSY で確認 → **もう一度 RST_REQ**（TQ/G6K の「使う前に初期化」[bnd:L471, L506]）→ PT2314E の初期化（電源投入後 50 ms は I²C 禁止 [sw:L316]）
2. **切替**（スロット a の ch x → スロット b の ch y）:
   1. ミュート（PT2314E のミュート 100 dB typ [sw:L313]）
   2. RST_REQ → RST_BUSY が解けるまで待つ（R-b で 60 ms）
   3. CH_ON̅ = 1（旧 ch の LDO OFF）
   4. a ≠ b なら: PWR_EN = 0 → SLOT を b に → PWR_EN = 1 → SLOT_PG_b を待つ（ソフトスタート 26 ms 以上）。**PG が来なければ PWR_EN = 0 に戻して故障表示**
   5. CH を y に → CH_ON̅ = 0 → LDO のソフトスタート（14 ms）＋**整定待ち**（出力カップリング τ 0.48 s の 3 倍 ≈ 1.5 s 〔仮定〕）
   6. SET_REQ（15 ms のパルスはハード）
   7. ミュート解除
   - 合計 ≈ 1.6〜1.7 s（枚が変わると +30 ms 程度）〔計算〕。律速は 5 の整定待ち
3. **禁止**: アドレス（SLOT/CH）はそのデコーダを無効にしている間しか変えない。PWR_EN を上げたまま SLOT を変えない
4. **監視**: 通電中に SLOT_PG が落ちたら（短絡・逆挿し）→ ミュート、全 OFF、表示。TPS2660 はブレーカで自分で切る [TPS2660 p9]、−15 V 側のディスクリートは電流制限のまま張り付くので**ファームが切る**（〔推論〕、−15 V で 60 mA × 15 V ≈ 0.9 W）
5. **I²C の方針**: 親の MCP へは切替のときだけ書く。PT2314E・UI の MCP は従来どおり

---

## 4. コネクタのピン数

### 4.1 スロットあたり

共通（どの案も）: **電源** +15 V_SW、−15 V_SW、A_GND ×2、+5V_COIL、GND_COIL ＝ 6。**音声** `J_ANA`（2×5）＝ TONE_L/R、AMP_SEL_L/R ＋ A_GND ×6 ＝ 10（今のまま [SF pin J_ANA301]）。

| 案 | 制御線（スロットあたり） | n = 1 | n = 2 | **n = 4** | 電源＋制御の合計（n = 4） |
|---|---|---:|---:|---:|---|
| **M0 リレー娘 (ii)**（ベースライン） | EN×n ＋ SET×n ＋ RESET | 3 | 5 | **9** | **15**（＋給電確認の折り返しを入れて 16）→ **今の 2×8 にちょうど入る** |
| M0 リレー娘 (i) | SET×n ＋ RESET | 2 | 3 | 5 | 11 |
| M0 TMUX 変種 (ii)/(i) | EN（＝SEL）×n ＋ 境界 SET ＋ 境界 RESET | 3 | 4 | 6 | 12 |
| M1（娘でデコード、(ii)） | CH_A（⌈log₂n⌉）＋ CH_ON ＋ SET ＋ RESET | 3 | 4 | 5 | 11（＋娘のロジックの電源は娘内で作る） |
| I1（娘に MCP） | SDA、SCL、3V3、D_GND ＋ RESET（POR 用） | 5 | 5 | 5 | 11（＋番地ジャンパ 3） |

### 4.2 親の側（4 スロット × n ch）

| 案 | 親からスロットへ出る制御線の総数 | n = 1 | n = 2 | **n = 4** | 親の論理への入力線（MCU 側） |
|---|---|---:|---:|---:|---|
| **M0 リレー娘 (ii)** | 4 × (2n + 1) | 12 | 20 | **36** | 出力 5 + ⌈log₂n⌉ + 1（CH_A・CH_ON）… n = 4 で 8、入力 5 |
| M0 リレー娘 (i) | 4 × (n + 1) | 8 | 12 | 20 | n = 4 で 7 |
| M0 TMUX 変種 | 4 × (n + 2) | 12 | 16 | 24 | n = 4 で 8 |
| M1 | バス共有 (⌈log₂n⌉ + 2) ＋ RESET_s × 4 | 6 | 7 | 8 | n = 4 で 8 |
| I1 | バス共有 4 ＋ RESET_s × 4 | 8 | 8 | 8 | I²C 2 ＋ 順序器の要求 |

（±15 V_SW はどの案でもスロットごとに 2 本 × 4 ＝ 8 本、スイッチの後ろから出る）

- M0 は線が多いが、**全部が静的か、切替のときだけのパルス**。バックプレーンの配線本数（36 本）は親の上の話で、娘の上のロジックと引き換え 〔推論〕
- **今の `J_PWR`（2×8）は 11〜16 が空き** [SF pin J_PWR301] → M0 (ii) の 16 本は同じフットプリントで入る（割当は変わる）

---

## 5. 今の回路図への対応（`sch_facts.py bom` の部品を分類）

分類の意味: **残す**＝新しい木でも同じ役 ／ **古い前提のためだけにある（外せる）**＝娘の MCP・番地・常時給電の前提でしか要らない ／ **置き換える**＝役は残るが部品か値かネットが変わる ／ **足りない**＝新しい木で要るが図に無い。

### 5.1 ルート `AudioV2Case`（59 個 [SF bom]）

| 部品（機能名） | 分類 | 理由（新しい制御の木との関係） |
|---|---|---|
| `U201` REC20K-2415DZ（±15 V DC-DC） | **置き換える** → RS6-1215D | 決定済み [NOW:L14]。(ii) で負荷が n に依らない [DCS:L33]。SIP8 の新フットプリント（Ø1.0 穴）[pow:L100] |
| `C205`/`C206`（DC-DC 入力 47 µF/0.1 µF） | 残す（値は見直し） | RS6-1215D には DS の EMC 推奨値が無い [pow:L85] |
| `F201` F2A 速断（DC-DC の入口） | **置き換える**（値） | REC20K の全能力（1.89 A）に合わせた値 [NOW:L160]。RS6 は 6 W / 87 % / 12 V で入力 ≈ 0.57 A 〔計算〕。RS6 の DS にヒューズの推奨は無い [pow:L108] |
| `C201`/`C202`、`C207`/`C208`（±15 V 出力 47 µF/0.1 µF） | 残す | DC-DC の起動時に見えるのは親だけ（57.2 µF）[DCS:L37]。+100 µF を足すかは未決（§7-D8） |
| `F203` PPTC 0.1 A、`U202` L7809CV、`C203`/`C204`（+9 V） | 残す | PT2314E の電源。+15 V だけに載る 35〜48 mA の負荷（PT2314E 30 / 40 mA [sw:L293]＋ L7809 の Iq ≤ 8 mA [pow:L445]）が DC-DC の +15 V を決めている [DCS:L103]。§7-D6 |
| `U402` PT2314E、`C401`〜`C412`、`R410`〜`R413`、`Q401`/`Q402`（トーン・I²C レベルシフト） | 残す | 音声の本線。制御の木とは I²C を共有するだけ（娘へは I²C を出さなくなる） |
| `U403` BP5293-50（`+5V_COIL`） | **置き換える** → L7805C | §3.6。聴取中は無負荷で SLLM、その出力が全娘へ行く |
| `F202` PPTC 0.4 A（コイルの枝）、`NT101`（GND_COIL–D_GND） | 残す | 1 枚ずつのリセット（最悪 362 mA）なら保持 0.4 A の内側 〔計算〕。トリップ時間は未確認 |
| `U501`、`R501`〜`R504`、`C501`〜`C506`（HP バッファ） | 残す | 制御の木と無関係（±15 V の負荷には入っている [DCS:L58]） |
| `J201`、`J202`、`J_IN401`、`J_HP501`、`J_LINE501`、`J_RAIL501`、`J_PNL*`（6 個） | 残す | 箱の入出力・パネル。無関係 |
| `J_ANA101`（スロットの音声 2×5） | 残す（**4 口に増やす**） | ピン割当はそのまま。ch のリレーが境界なので音声はバス共有でよい |
| `J_PWR101`（スロットの電源・制御 2×8） | **置き換える**（ピン割当、4 口） | ±15 V → スロットごとに切った ±15 V_SW。I²C・3V3・D_GND を外し、7〜16 を EN×4・SET×4・RESET・給電確認に |
| — | **足りない** | スロットの ±15 V スイッチ ×4 口（§3.5）、`CD74HC238`、`CD74HC4514` ×2、`SN74LVC1G123` ×5、`TPS3808G01`、親の `MCP23017`、TONE_L/R のプルダウン 100 kΩ ×2、SLOT_PG の合成 ×4、各種のプル抵抗、`J_ANA`/`J_PWR` の 2〜4 口目 |

**PT2314E＋L7809 の電源をどうするか（依頼）**:
- 今（+15 V → PPTC 0.1 A → L7809 → 9 V）のまま: +15 V の max・HP 歪み始め 150.3 mA（RS6 の 75 %）[DCS:L84]。**(ii) を選んだので余裕はある** → ベースラインでは変えない
- PD 12 V（`SW402` の後ろ）から 9 V の LDO で取る場合 〔計算〕: +15 V から 35 / 48 mA（typ / max）が消え、max・HP で **102.3 mA（51 %）**、typ・無音で 52.6 mA（26 %）。−15 V は変わらず 101.9 mA（51 %）・typ 26.7 % → **正負がほぼ対称**になり、RS6 のクロスレギュレーションの規定（25〜100 %）[pow:L64] の内側に両レールとも入る。**代償**: PT2314E の GND は `A_GND`（DGND ピンも足元で A_GND [NOW:L191]）なので、PD_12V から取った 30〜40 mA の帰りは `A_GND` → `NT1603` → `D_GND` → `NT1602` → `PD_GND` を通る [SF pin NT1602 NT1603]。ADC の LDO を PD へ移すときにグランドの木を付け替えたのと同じ種類の判断が要る [NOW:L10]。L7809C を 12 V 入力で使うのは試験条件の下限 11.5 V の近く [pow:L441] で、ドロップアウトは 1 A で 2 V typ [pow:L447] → 12 V から取るなら低ドロップアウトの LDO（例 TPS7A49 で 9 V、ヘッドルーム ≥ 1 V [pow:L231]）の方が素直 〔推論〕
- 使い道: (i) に戻す・娘を 5 枚以上にする・HP の上限まで見る、のどれかを将来やるときの余裕の源 〔推論〕

### 5.2 `AmpBankRelay`（20 個）

| 部品（機能名） | 分類 | 理由 |
|---|---|---|
| `K301`〜`K304` AZ850P2-5（ch の出力リレー） | 残す | ch の出力側の境界。NOW で固定 [NOW:L221] |
| `U321` TBD62083APG | 残す | 8 出力を SET×4・RESET×4 に。**VCC が無いので電源の無い娘でもリセットが効く**。1 出力に 2 コイル並列で 80〜91 mA 〔計算〕 |
| `C321` 100 µF / `C322` 100 nF（コイルの局所） | 残す | パルスの立ち上がり |
| `U_IO302` MCP23017、`C_IO302`、`R_ADDR_A0`〜`A2` | **外せる** | I²C と番地の前提でしか要らない（M0） |
| `C_BULK_P302`/`C_BULK_N302` 100 µF 35 V | **置き換える**（ダンパへ） | 電荷の溜めの役は無くなる [NOW:L19]。値と形は §3.8 |
| `J_ANA302` | 残す | |
| `J_PWR302` | **置き換える**（ピン割当） | §4 |
| `H311`〜`H314` | 残す | |
| — | **足りない** | **入力リレー ×4**（今は入力が TONE に直結 [SF nets TONE_L]）、ch の LDO 一式 ×4、EN 保護 ×4、TBD 入力のプルダウン ×8、入力ブリーダ ×8、ダンパ |

### 5.3 `AmpBankSwitch`（23 個）— TMUX 変種を残す場合

| 部品 | 分類 | 理由 |
|---|---|---|
| `U311`/`U312` TMUX7612（2 ch の出力 L/R ずつ） | **置き換える**（組み直し） | ch ごとに 1 個（入力 L/R＋出力 L/R）→ 4 個。ch の入力も切るため |
| `C311`〜`C318`（TMUX のデカップ 100 nF・1 µF） | 残す（個数は 4 個ぶんに） | DS 推奨 0.1 µF＋1 µF [sw:L141] |
| `U_IO301`、`C_IO301`、`S_ADDR_A0`〜`A2` | **外せる** | M0 |
| `C_BULK_P301`/`N301` | **置き換える**（ダンパへ） | 同上 |
| `J_ANA301` / `J_PWR301` / `H301`〜`H304` | 残す / 置き換える（ピン割当）/ 残す | |
| — | **足りない** | 娘の境界リレー 2（入力・出力）＋駆動、ch の LDO 一式 ×4、EN 保護 ×4 |

**変種をやめるなら、このシートは全部「外せる」**。

### 5.4 `AmpChannel`（17 個 × 8 インスタンス）

| 部品 | 分類 | 理由 |
|---|---|---|
| ソケット（`AMP601` 型）、入出力フィルム、ゲイン抵抗 0.1 %、47 Ω、入力 100 kΩ、出力 220 kΩ | 残す | ch の回路そのもの。入力 100 kΩ は切り離した入力のバイアス、出力 220 kΩ はリレーの ch 側の DC 基準（§3.11） |
| デカップ 100 nF（`C608`/`C609` 型）とソケットの V+/V− | **置き換える**（ネットだけ） | `+15V`/`-15V` → ch の LDO 出力（±12 V） |
| — | **足りない** | ch の LDO 一式（シートに入れるか娘のシートに入れるかは生成スクリプトの設計次第） |

### 5.5 NOW で「娘に足す」と決めた 3 つ [NOW:L15] の扱い

| 項目 | 新しい木での扱い |
|---|---|
| 娘ごとの 1 ch だけ ON できるデコーダ（既定 OFF） | **置き換える**: 親の `CD74HC4514`#1（E̅ のプルアップで既定 OFF）へ。娘には置かない |
| 正 LDO の EN 保護 | 残す（娘に置く）。EN は親から来るので必須 |
| ±15 V があることを Pico へ知らせる検知線 | **置き換える**: 親のスイッチで取る（SLOT_PG）。娘からの線は任意（コネクタの接触を確かめたいときの折り返し） |

### 5.6 範囲外のシート

`MeasureControl`・`FrontPanel` は本書の木に入らない。関係する事実だけ: Pico の空き GPIO は 7 本〔§3.12〕、UI の MCP（`U1610`）は GPB3〜7 の 5 本が空き [SF pin U1610] だがフロントパネル基板の上にあり、スロットへの線の出どころには向かない 〔推論〕。

---

## 6. 推奨ベースライン（まとめ）

```
PD 12 V ─ SW402 ─┬─ F201 ─ RS6-1215D ─ ±15 V（親: C201/C207、HP、PT2314E、INA1650）
                  │                       │
                  │                       ├─ スロット k（×4）: TPS26600（+、0.1 A・26 ms・ラッチオフ）
                  │                       │                    ＋ディスクリート（−、~60 mA・26 ms）
                  │                       │                    → ±15 V_SW_k → 娘 k: ダンパ → ch の LDO ×4（EN）
                  │                       │                                           → ソケット ±12 V
                  └─ F202 ─ L7805C ─ +5V_COIL（常時）─ 全娘の TBD62083A の COMMON／リレーの＋
親の論理（3.3 V）:
  MCP23017（親だけの I²C）→ SLOT_A0/A1, CH_A0/A1, PWR_EN, CH_ON̅, SET_REQ̅, RST_REQ̅
  CD74HC238 ── SLOT_ON_1..4 → 各スロットのスイッチ
  CD74HC4514#1（E̅=CH_ON̅）── EN_{s,c}（16）→ 娘の ch LDO の EN（EN 保護経由）
  CD74HC4514#2（E̅=SET ワンショット Q̅）── SET_{s,c}（16）→ 娘の TBD 入力
  TPS3808G01（+5V_COIL を監視）→ LVC1G123 ×4 の連鎖 ── RESET_1..4（15 ms ずつ順に）→ 娘の TBD 入力
                                   └ RST_BUSY̅（ダイオード AND）→ SET ワンショットの CLR̅
  SLOT_PG_1..4（FLT ∧ −15 V 検知）→ MCP23017
娘（リレー、4 ch）: TBD62083A ×1、AZ850P2-5 ×8、ch の LDO 一式 ×4、EN 保護、プルダウン、ブリーダ。ロジック IC 0
```

いちばん強い理由（機能ごと）は §0.1 の表。全体を 1 行で言うと: **排他・順序・パルス幅・起動時のリセットを親のハードに集め、娘を「電源が無ければ完全に死んでいる基板」にする**。これで、聴取中に娘に来るのは選んだ ch の EN の DC 1 本だけになる。

---

## 7. ユーザーに残る決定と、それぞれに要るデータ

| # | 決めること | 選択肢と本書の含意 | 要るデータ |
|---|---|---|---|
| D1 | TMUX 娘の変種を残すか | 残すなら: ch ごとに TMUX7612 1 個（4 個／枚）＋娘の境界リレー 2＋駆動。制御線は 1 口 6 本（§4）。聴取中に娘に TMUX の電源電流と SEL の DC がある。やめるなら `AmpBankSwitch` は全部外せる | 耳の比較に TMUX を入れる意味（v1/v2 の実測: TMUX の H3 −115.5 dB [NOW:L226]）の重み |
| D2 | リレーの品種 | AZ850P2-5 のまま（40 mA、最小幅が DS に無い）／**TQ2SA-L2-4.5V**（表面実装で 5 V 品 28.1 mA、10 ms 推奨・同時通電禁止・出荷リセットが明記。**4.5 V 品のコイル値は未取得**）／1 コイル型（電流半分、ハーフブリッジが要る） | TQ の 4.5 V 品のコイル表、AZ850 のバウンス時間（どの DS にも無い [bnd:L554]→ ベンチ）、手持ち在庫 |
| D2' | （付記）SET コイルの＋を娘の切られた電源から取るか | AZ850P2 は SET と RESET の＋が別ピン [AZ850 p2 図] → 電源の無い娘は物理的にセット不能にできる。代わりに娘に 5 V を作る部品が要る | — |
| D3 | リセットの順次化 | **1 枚ずつ（推奨、最悪 362 mA、手順 80 ms）**／同時（1.45 A を出せるコイル電源が要る、35 ms）／1 ch ずつ（91 mA、260 ms） | PPTC `RXEF040` のトリップ時間（DS 未取得）、コイル電源の選択（D5） |
| D4 | −15 V のスイッチ | **ディスクリート（推奨）**／LM5067（−15 V では VCC の推奨電流の端） | ディスクリートの ngspice（ソフトスタートの直線性、電流制限の温度）か、LM5067 を −14.25〜−15.75 V で動かしたベンチ |
| D5 | コイル電源 | **L7805C（推奨、スイッチング無し）**／BP5293 のまま／ゲート（TPS22810） | BP5293 の SLLM 間欠のときの `+5V_COIL` の波形（娘の上での結合）を測るなら、今の基板で測れる |
| D6 | PT2314E の電源 | +15 V のまま（(ii) なら RS6 75 %）／PD 12 V から（+15 V 51 %、正負対称。グランドの木の判断が要る） | PD_12V から取ったときの帰り電流の経路（`NT1602`/`NT1603` の置き場所） |
| D7 | 親の線の出どころ | **親に MCP23017（推奨）**／Pico 直（7 本しかないので n ≤ 2 か PG をマルチプレクサで 1 本に） | — |
| D8 | 親のバルク +100 µF | RS6 なら残してよい [DCS:L325] | 娘 1 枚だけが載る網での [BPS] の AC 掃引のやり直し [DCS:L325] |
| D9 | ダンパの形 | NOW の RC ダンパ／[BPS] (3) の直列 0.33 Ω。本構成では活線挿入の論点が消える（§3.8） | 同上 |
| D10 | SET 前の整定待ち | 出力カップリング τ 0.48 s。3τ の 1.5 s は〔仮定〕 | ch を ON してからの `CH_OUT` の DC の実測（リレーを閉じる前） |
| D11 | 給電確認を取る場所 | 親（SLOT_PG、推奨）／娘から折り返し（コネクタの接触まで分かる、1 ピン） | — |
| D12 | 5 枚以上にするか | ジャンパの制約は消えた。1 石の `CD74HC4514` は 4 枚×4 ch まで。5 枚目からはデコーダ 1 組とスイッチ 1 組を足す。DC-DC は (ii) なので変わらない | 聴き比べたい石の数（NOW は 10 個 [NOW:L32]。4 ch × 3 枚で 12） |

### 確かめられなかったこと

- `SN74LVC1G123` で 15 ms を出す Rext・Cext（表は 1 ms の行までで、K の図で確かめる必要がある）
- PPTC `RXEF040` のトリップ時間（DS 未取得。Littelfuse のサイトは 403）
- ラッチ型リレーのバウンス時間（どの DS にも無い）と、AZ850 の最小パルス幅（DS に無い）
- 4 極のラッチ信号リレーの DS（手元に無い。Panasonic DS は 1 Form C のみ）
- `TQ2SA-L2-4.5V` のコイル値（boundary.md は 5 V 品だけ）
- ディスクリートの −15 V スイッチ（汎用品で DS を取っていない。シミュレーションかベンチ）
- Pico 2 のボードのピン配置（GPIO 7 本の数え方）。ボードの DS はリポジトリに無い
- boundary.md は**未照合**（照合エージェントが走っている）。本書の [bnd:…] は照合後に変わりうる

---
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
