indare/pcb_work/AudioV2.1/review/arch_zero_base_review.md

# 査読（否定側）: `AudioV2.1/review/arch_zero_base.md`

- 作成: 2026-09-25（査読エージェント）。**リポジトリのファイルは変更していない**。出力はこのファイルだけ
- 方法: `AudioV2.1/datasheets/arch/` と `AudioV2.1/datasheets/` の DS を `pdftotext -layout` で全文を検索し、判定に効くページは `pdftoppm -r 150` で描画して目で確認した（TPS2660 p18 の機能ブロック図、LM5067 p13、TPS22810 p13、AZ850 p2、TPS7A49 p12、TPS7A30 p14）。ユーザー要件は `AudioV2.1/NOW.md` と依頼文から取った
- 記号: 〔計算〕＝DS の数値どうしの算術／〔推論〕＝DS に書いていない判断／〔未照合〕＝`ds_facts/boundary.md` 由来（照合中）
- **査読の途中でユーザーの決定が入った**（コーディネータ経由、2026-09-25）: v2.1 は**娘 1 種類**（ch ごとのリレーは作らない）。1 段目＝娘ごとのラッチングリレー境界（音声 4 本、DPDT 2 個／枚）＋娘の ±15 V を電源 IC で切る（発振器・チャージポンプ無し）＋レール良好でだけ境界をセット、2 段目＝娘の中は TMUX7612、選んだ ch だけ LDO の EN で給電、EN の論理は娘の切られたレールから給電、切替中は GND へのミュート。**§1〜§5 は元の提案（ch ごとのリレー）への査読として残し、新しい軸での扱いは §6 にまとめた。§6 が優先する**

---

## 0. 結論（先に）

### 0.1 新要件（電源経路の IC に内部発振器・チャージポンプが無いこと）で提案は**不合格**

| 部品 | DS の事実 | 判定 |
|---|---|---|
| **TPS26600**（提案 #7 の +15 V スロットスイッチ） | 機能ブロック図に **"Charge Pump"** のブロックがあり、その出力 CP が Gate Control Logic を経て内蔵の 150 mΩ の FET のゲートへ行く [TPS2660 p18、描画して確認]。**周波数は DS に書かれていない**（全文検索で kHz / MHz / oscillat が 0 件） | **×** 要件を満たさない。周波数で「音声帯域より十分高い」と言い逃れる材料も DS には無い |
| TPS22810（提案で「コイル電源のゲートに使える」とした） | 本文 "Integrated control logic, driver, **charge pump**, and output discharge FET" [TPS22810 p12]、ブロック図に "Charge Pump" [p13]。周波数の記載なし | **×** |
| LM5067（提案では △） | ゲートは VCC（VEE から 13 V の内蔵ツェナーシャント）から **52 µA の定電流**で上げる。ブロック図にチャージポンプも発振器も無い [LM5067 p13、描画して確認]。TIMER は外付け C を定電流で充放電するだけで、LM5067-2 の再試行だけが故障時に TIMER を 8 回往復させる [p6, p13] | **○**（LM5067-1＝ラッチオフ品なら故障時の往復も無い） |
| TPS7A49 / TPS7A30（ch の LDO） | どちらもバイポーラの LDO。ブロック図は Enable・UVLO・電流制限・熱遮断・誤差増幅・パス素子だけ [TPS7A49 p12、TPS7A30 p14] | ○ |
| BP5293-50（現行のコイル電源） | 570 kHz typ の内部発振器 [BP5293 p3, p5] | 提案はすでに L7805C へ替えている → この点は要件と整合 |

**一般則〔推論〕**: 正レール（+15 V）の上側に N-FET を置く一体型 eFuse／負荷スイッチは、ゲートを入力より上げるために内部チャージポンプを持つのが普通で（TPS2660・TPS22810 とも該当）、このクラスはまるごと候補から外れる。+15 V 側に要件を満たす既製 IC は**手元の DS には無い**。§3 に要る仕様を書いた。
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
