indare/pcb_work/tmp_asfl1_ref/crop_A.png

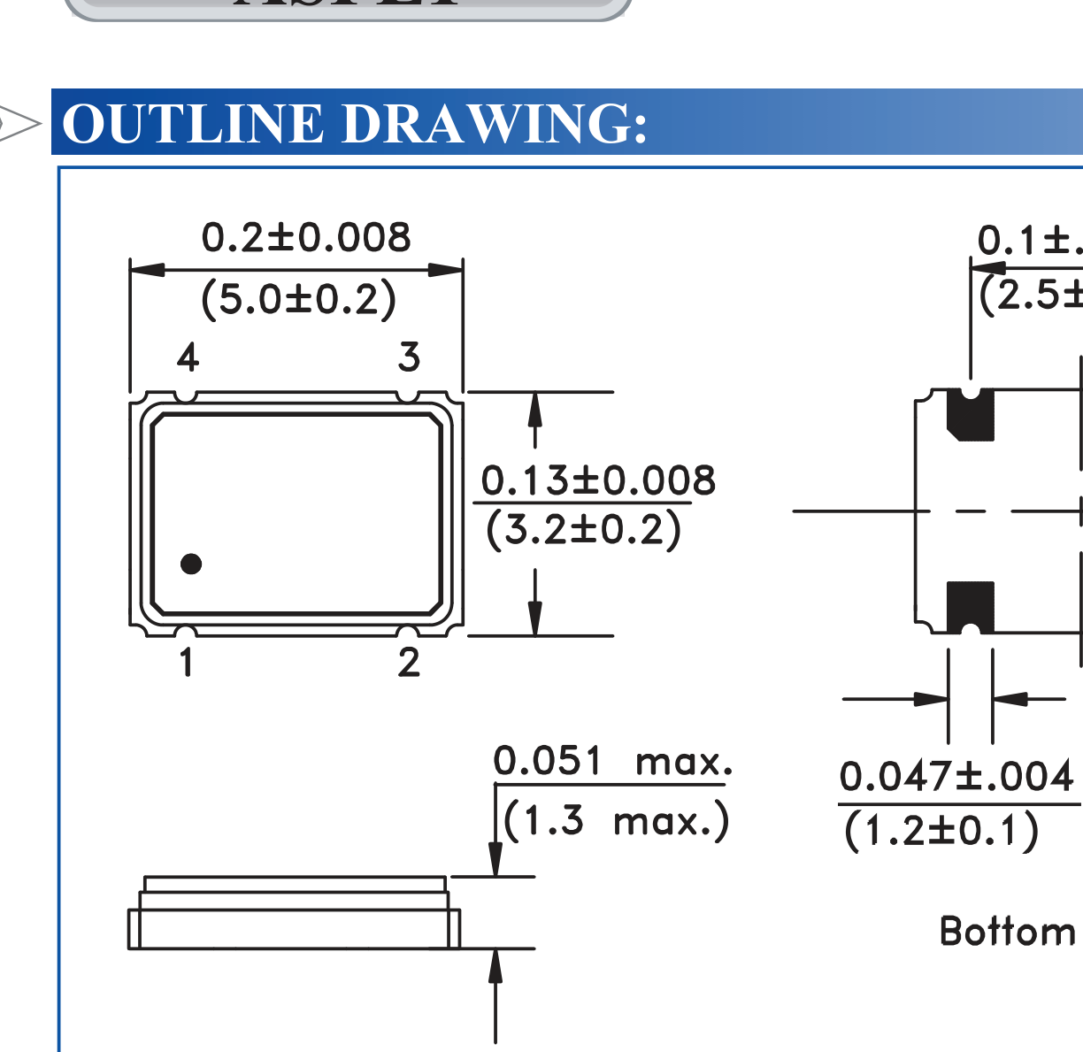
tmp_asfl1_ref/crop_A.png
