indare/pcb_work/tmp_asfl1_ref/crop_B.png

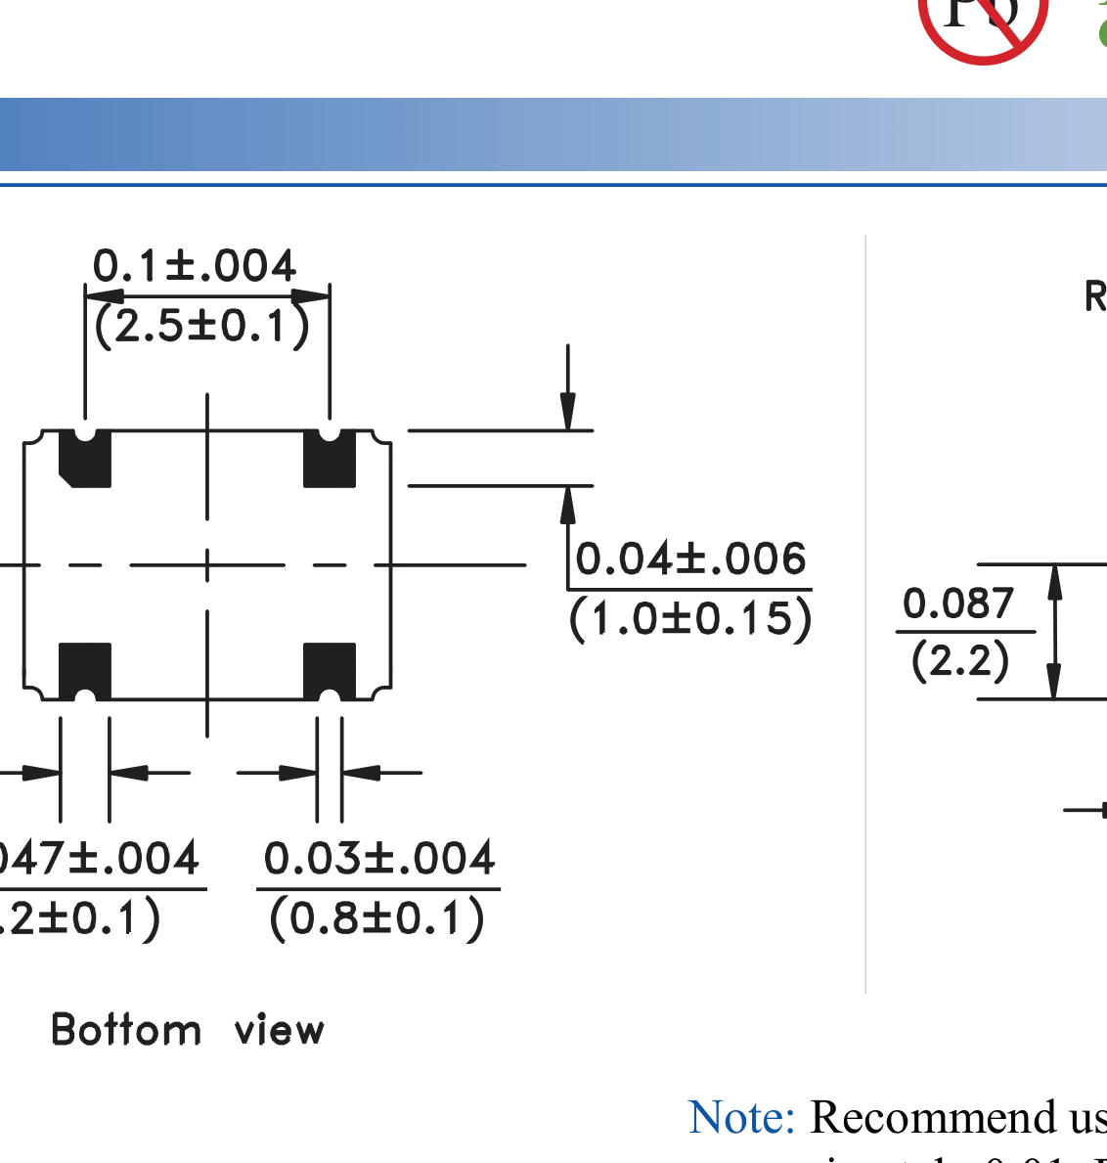
tmp_asfl1_ref/crop_B.png
