indare/pcb_work/tmp_asfl1_ref/outline_crop.png

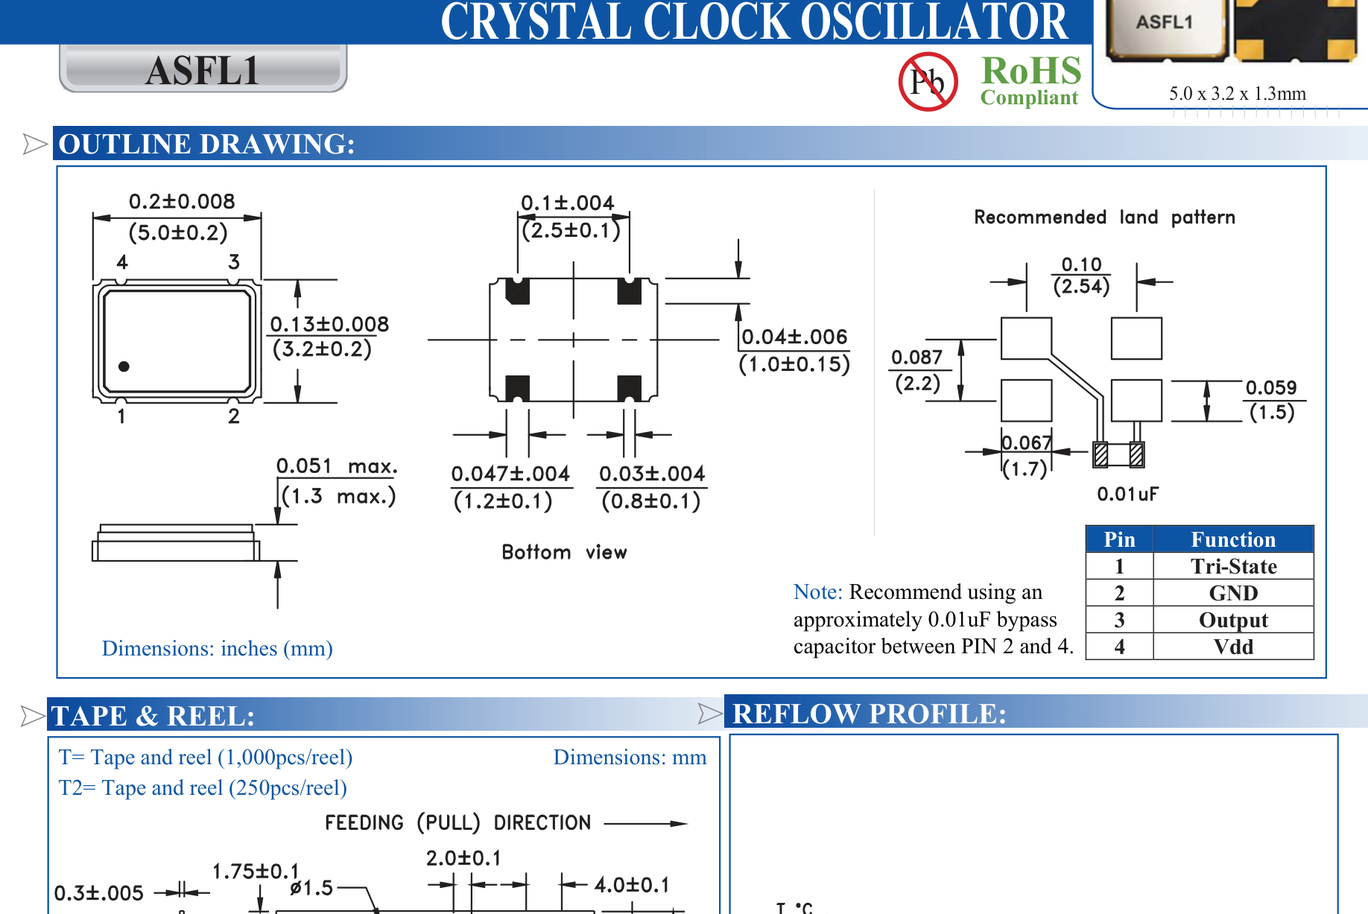
tmp_asfl1_ref/outline_crop.png
