indare/pcb_work/tmp_asfl1_ref/outline_hi.png

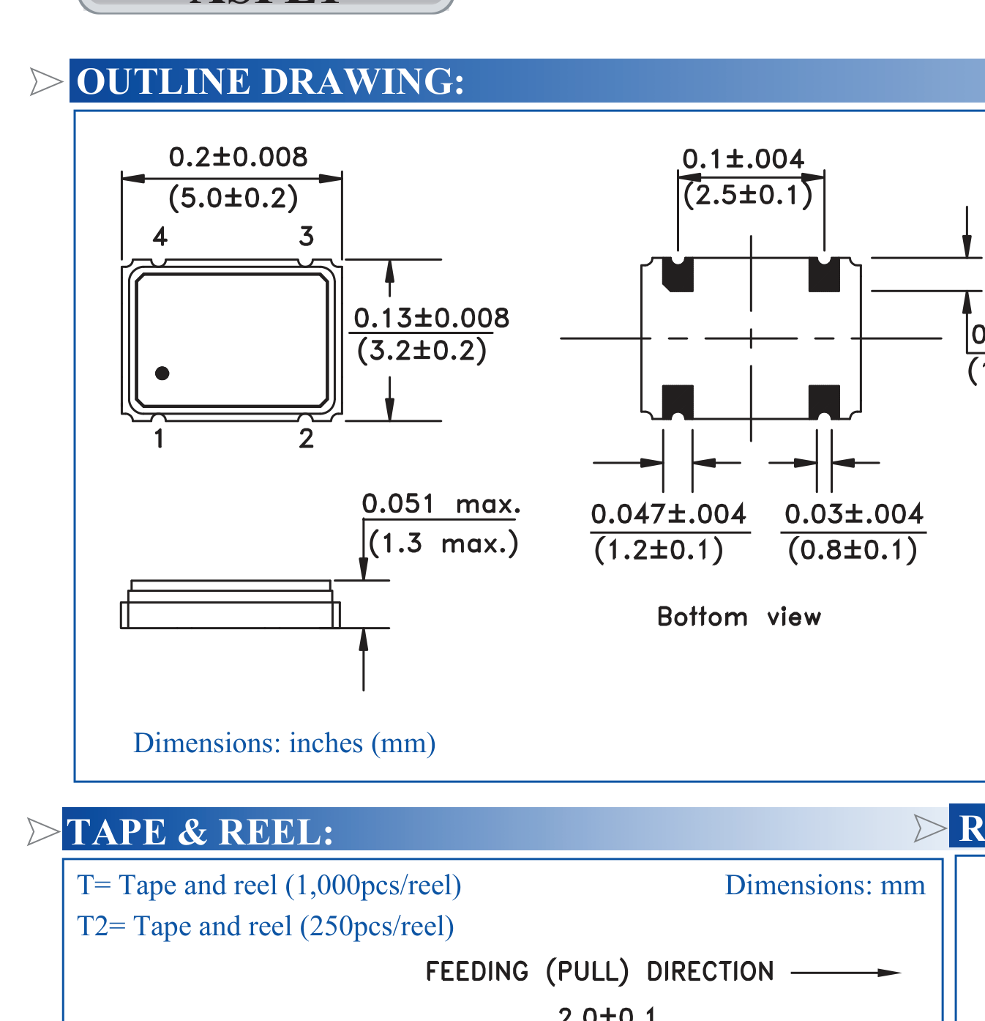
tmp_asfl1_ref/outline_hi.png
