indare/pcb_work/tmp_asfl1_ref/pintable_hi.png

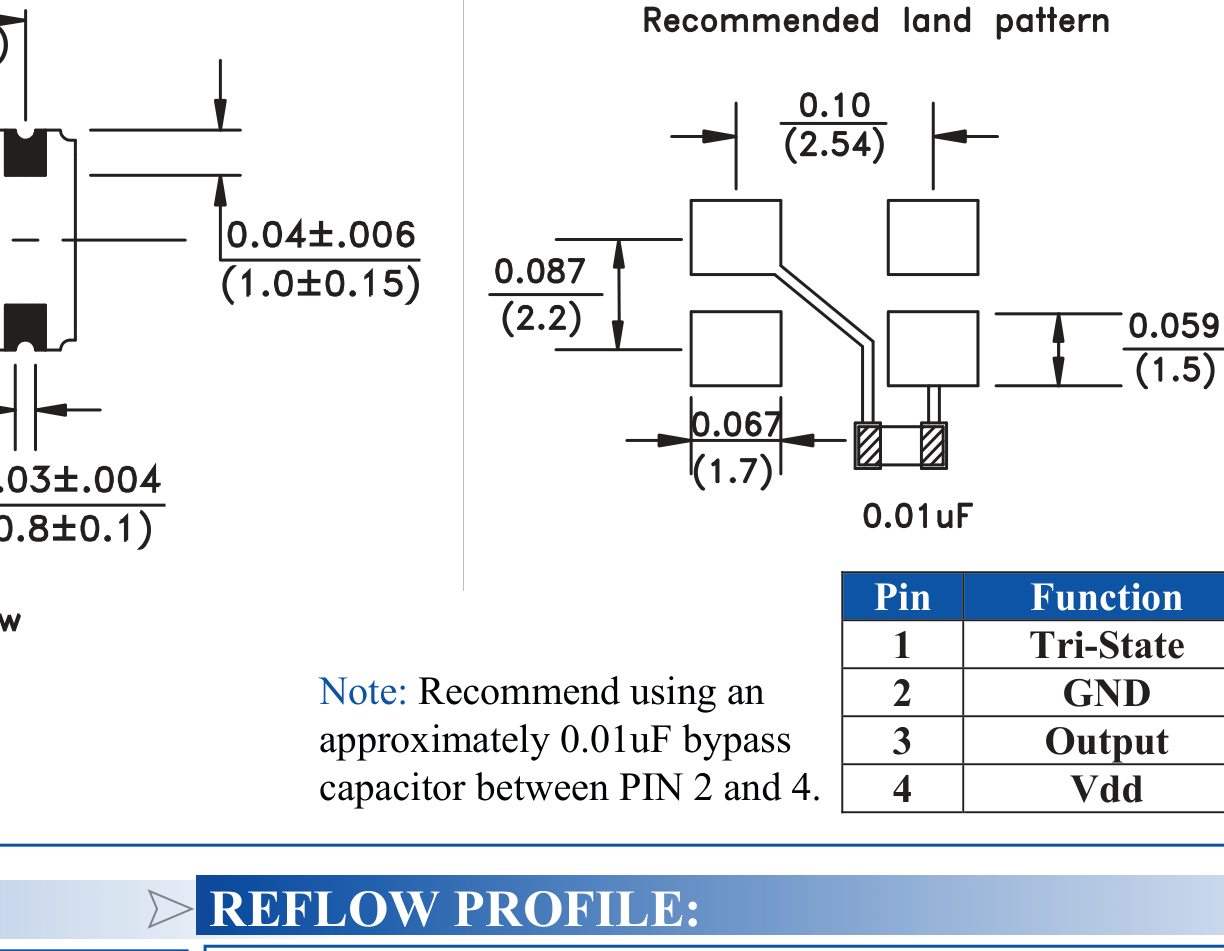
tmp_asfl1_ref/pintable_hi.png
