indare/pcb_work/tmp_lt1763_ref/akizuki_6.jpg

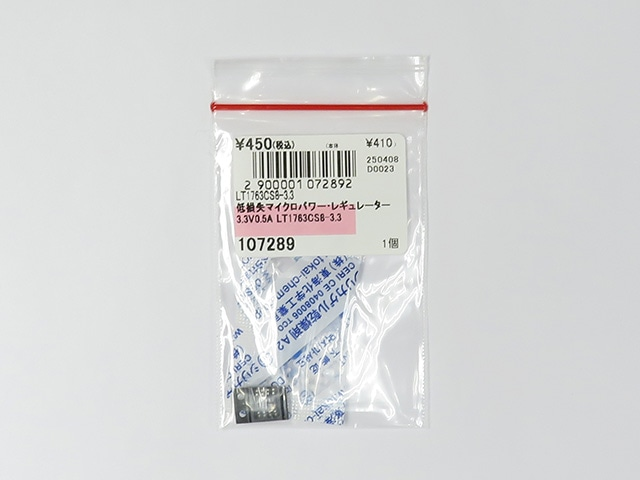
tmp_lt1763_ref/akizuki_6.jpg
