indare/pcb_work/tmp_lt1763_ref/lcsc_cs8_front.jpg

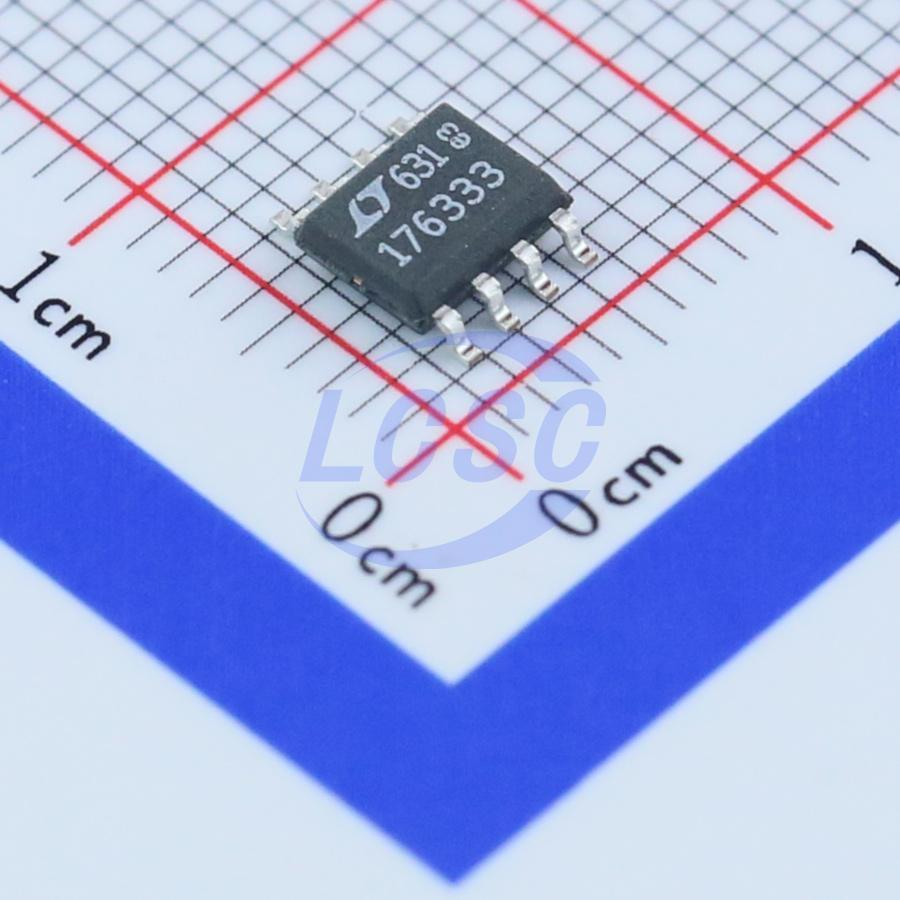
tmp_lt1763_ref/lcsc_cs8_front.jpg
