indare/pcb_work/Audio/MeasurementADC_ORDER.md

# MeasurementADC 発注リスト（共立寄せ / 秋月補完）

**次号の Ref 付き BOM は `MeasurementADC_BOM.md`（2026-08-21）。** このファイルは初号調達の履歴。

調査日: **2026-07-17**（手持ち: Pico2・WAVESHARE-29318・端子・Picoソケット候補・タクマン47Ω/10k・中華33Ω/100k）  
対象: `MeasurementADC1804_Module` 1台分  

**ステータス: 初号オーダー終了（2026-07-17）／追加1点（2026-07-26）** — 当時の BOM は調達完了。LCD ロードスイッチ置換に伴い **U710 XC8107AC20MR-G のみ追加発注**。次号の不足分は `MeasurementADC_BOM.md`。

> ⚠ **この文書の Ref は 2026-07 当時のもので、現行回路図とずれている。** 次号は `MeasurementADC_BOM.md` を正とすること。
>
> | この文書 | 現行回路図 | 部品 |
> |---|---|---|
> | U708 | **U709** | TPS3808G33DBVR（+3V3_A 監視・マーキング AVO） |
> | U709 | **U710** | TPS3808G50DBVR（+5V_A 監視・マーキング AVN） |
> | U710 | **U708** | XC8107AC20MR-G（LCD ロードスイッチ） |
>
> **予備の在庫状況（2026-08-14）**: 監視 IC は各2個（実装1＋予備1）発注していたが、
> **G50（AVN）の予備は初号機の U710 載せ替えで使い切った。** その U710 も出力 L 固定で
> ピン1をリフト中なので、+5V_A 監視を復旧するなら G50 を新規手配する必要がある。
> G33（AVO）の予備は未使用。経緯は `MeasurementADC_BRINGUP.md`。  

方針: 共立・マルツ・秋月で**コア部品は発注確定**。デカップ積セラは**千石で購入済**。  
**Pico2・LCD・スクリュー端子・ヘッダ・タクマン47Ω/10k・中華33Ω/100kは手持ち。**  
MCW03 専用化用の予備基板あり。

---

## 送料（共立エレショップ）

サイト表記: **1回のご注文 税込 7,500円以上で送料無料**  
（※「5,000円」ではなく **7,500円**）

未満時の目安: ネコポス 310円 / 宅配（本州など）550円。

---

## 手持ち（発注不要）

| Ref | 品名 | メモ |
|---|---|---|
| A702 | Raspberry Pi Pico 2 | 手持ち |
| LCD | WAVESHARE-29318 | 手持ち |
| J | スクリュー端子台 | 手持ちあり → 秋月で買わない |
| Pico実装 | 20P メスピンヘッダ | **手持ち確認済**（40Pメスから切る） |
| LCD実装 | 1×15 オスピンヘッダ | **手持ち確認済**（40Pオスから切る） |
| R713–R716 | タクマン 47Ω 1% 1/4W | 手持ち。FP=`R_Axial_DIN0309_L9.0mm_D3.2mm_P12.70mm_Horizontal`（ADC入力直列） |
| R719 | タクマン 10kΩ 1% 1/4W | 手持ち。同上 FP（OD pullup） |
| R717 | 100kΩ 1/4W（中華セット） | 手持ち。FP=`R_Axial_DIN0411_L9.9mm_D3.6mm_P12.70mm_Horizontal`。**U710(XC8107) の CE プルダウン**（2026-07-26 変更。旧: Q701 ゲート直列） |
| R718 | **33Ω** 1/4W（中華セット） | **手持ち確認済**。同上 FP（MCLK 12.288MHz 直列）。THT可だがSMDの方が理想 |

---

## 千石電商: 購入済（2026-07-17・秋葉原本店）

| コード | 品名 | 型番 | 単価 | 数 | 小計 | Ref |
|---|---|---|---|---|---|---|
| EEHD-5YZP | ムラタ 積セラ 0.1µF | RDER71H104K0K1H03B | ¥32 | **40** | ¥1,280 | C701 他 100nF ×18（+予備） |
| EEHD-4ZFF | ムラタ 積セラ 0.01µF | RDER71H103K0K1H03B | ¥32 | **30** | ¥960 | C725/726/731/732 ×4（+予備） |

**千石小計 ≒ ¥2,240**

- 50V X7R ±10%、リード間隔 **P5.0mm**。FP=`Library:C_Murata_RDE_L4.0mm_W3.5mm_T2.5mm_P5.00mm`（L4.0×W3.5×T2.5 max / F=5 / W1=6。上面視は L×T。3D=`Library.3dshapes/…step`）
- 必要数は 100nF×18 / 10nF×4。残りは予備・他基板用。

---

## 共立: 発注確定（2026-07-17）

| コード | 品名 | 型番 | 数 | 小計 | Ref |
|---|---|---|---|---|---|
| M1S412 | SoundPlus 超低ノイズ デュアルOPA | OPA1656ID | 4 | ¥2,640 | U701–U703 |
| C7E412 | ステレオADC 独立実験基板 | ADC1804_F | 1 | ¥2,682 | A701 |
| Q5M411 | OPA1652 DIP化モジュール | OPA1652AID-DIP | 4 | ¥4,840 | **AMP501**（AdcBuffer、1+予備） |
| 3573061 | ABRACON 発振器 12.288MHz | ASFL1-12.288MHZ-EC-T | 2 | ¥804 | Y701（1+予備） |

**共立合計 ≒ ¥10,966**

> **注**: Q5M411（OPA1652AID-DIP）は **AdcBuffer AMP501** の実装品（DIP-8 ソケット）。MeasurementADC の U701–U703 は別石 **OPA1656ID（SOP8）**。OPA1612 は使わない（10 kΩ 級では電流ノイズが不利）。

---

## オペアンプ決定: OPA1656（確定・発注済み）

`U701–U703` は **OPA1656**（回路図の Value/FP 反映済み）。

- 理由: 現行 3.3kΩ / 4.7kΩ 網ではバイポーラ入力の電流ノイズが効きやすい。FET 入力の OPA1656 が物差し用途に合う。
- ADA4075-2 検討は取り下げ。
- 共立 [M1S412](https://eleshop.jp/shop/g/gM1S412/) ×4 **購入済み**。
---

## 秋月: 発注確定（2026-07-17）

送料: **税込 ¥11,000 未満は佐川¥550 / ヤマト¥600** → 今回は送料払い。

| # | コード | 品名 | 単価 | 数 | 小計 | Ref |
|---|---|---|---|---|---|---|
| 1 | 131750 | MBC2596-01 | ¥1,900 | 2 | ¥3,800 | U705 |
| 2 | 111188 | BP5293-50 | ¥240 | 2 | ¥480 | U704 |
| 3 | 107289 | LT1763CS8-3.3 | ¥450 | 2 | ¥900 | U706 |
| 4 | 107290 | LT1763CS8-5 | ¥440 | 2 | ¥880 | U707 |
| 5 | 117897 | ルビコン PX 10µF50V | ¥10 | 10 | ¥100 | C703/C704 |
| 6 | 116868 | ハイブリッド 47µF63V PZJ | ¥80 | 10 | ¥800 | C714 |
| 7 | 108294 | OS-CON 22µF35V | ¥60 | 10 | ¥600 | C735 |
| 8 | 117338 | 10µF50V B 3216（10個入） | ¥250 | **2パック** | ¥500 | LDO IN/OUT 等 |

**秋月小計 ≒ ¥8,060 + 送料¥550〜600**

### 選定メモ

- 電源モジュールは各 **実装1 + FP計測/予備1**。適正。
- 受動は必要数より多め（10µF×10、47µF×10、22µF×10、セラミック20個）。単価が安いので在庫として妥当。
- ターミナル・Picoソケットは**手持ち**のため秋月では未購入。Pico用20Pメス／LCD用1×15オスは **40Pヘッダ手持ちから切断**で確保。
- R713–R716（47Ω）・R719（10k）は**タクマン1/4W手持ち**。SMDではなく THT（DIN0309 P12.7）に変更済み。追加購入不要。
- ±15V 共有レール: C703/C704 は **10µF のまま**（専用MCW03化するなら余裕は増えるが、容量はそのままでOK）。

> **±15V 共有**: PowerModule は **DKMW20F-15**（±660mA、Cout **650µF/出力**、1″×1″）。TMR 6-1223（±200mA / SIP-8）は電流の次点。Amp 島バルク 100µF は任意。旧 MCW03（47µF）では Amp 100µF が仕様外。計算: `PowerModule_TEC3_REDESIGN.md`。

---

## Tayda Electronics 調査（2026-07-17）

URL: https://www.taydaelectronics.com/  
結論: **秋月カートの本命部品はほぼ無い。** 補助部品だけならあり得るが、日本向け送料を考えると秋月継続が現実的。

### 無い（今回の必須）

| 部品 | Tayda |
|---|---|
| OPA1656 / OPA1652 | なし（NE5532 / LM833 等の汎用のみ） |
| LT1763CS8-3.3 / 5 | なし |
| BP5293-50 | なし |
| TPS3808G33 / G50 | なし |
| AO3401A | なし（近い Pch SOT-23 はあり） |
| ASFL1-12.288 | なし |

### ある（参考・代替候補）

| 用途 | Tayda 品 | 単価目安 | 在庫感 | URL | メモ |
|---|---|---|---|---|---|
| U705 代替 | LM2596S DC-DC module | **$1.20** | カート可 | https://www.taydaelectronics.com/lm2596s-dc-dc-step-down-power-supply-module.html | MBC2596 と同系統だが **外形・ピン配置が別**。FP 作り直し必須。ADC 前段には秋月 MBC2596 の方が確実 |
| C703/C704 | **10µF50V PSS 高分子** | **$0.10** | カート可 | https://www.taydaelectronics.com/10uf-50v-105c-pss-radial-polymer-aluminum-electrolytic-capacitor.html | 回路指定どおりの 10µF50V。秋月に無いので魅力的だが、**単品で取り寄せるほどではない** |
| C703 代替 | 100µF50V PSS | $0.20 | カート可 | https://www.taydaelectronics.com/100uf-50v-105c-pss-radial-polymer-aluminum-electrolytic-capacitor.html | 容量過大気味 |
| Q701 代替 | SI2301CDS Pch SOT-23 | $0.30 | — | https://www.taydaelectronics.com/si2301cds-t1-ge3-p-channel-power-mosfet-sot-23.html | AO3401 代替候補。試作は省略可 |
| 0.1% 抵抗 | 4.7k 1/4W 0.1%（10本入） | ~$0.09/本 | カート可 | https://www.taydaelectronics.com/10-x-resistor-4-7-k-ohm-1-4w-0-1-metal-film-pkg-of-10.html | **スルーホール**。基板は 1206 想定なら不向き。3.3k 0.1% は見当たらず |

### 方針

- **電源（MBC2596 / BP5293 / LT1763）→ 秋月のまま**
- Tayda は「国際注文をまとめるとき」の補助（10µF50V 高分子・端子・雑材）向き
- OPA / 発振器 / 監視IC は Tayda では解決しない

---

## マルツ: 発注確定（2026-07-17）

秋月に無い部品。DigiKey 提携のマルツ経由。税抜。

| Ref | 品名 | 型番 | 単価 | 数 | 小計 |
|---|---|---|---|---|---|
| ~~Q701~~ | ~~MOSFET P-CH 30V 4A SOT-23~~ | ~~AO3401A~~ | ¥122.86 | 2 | ¥246 |
| U708 | 監視IC 3.3V SOT-23-6 | TPS3808G33DBVR | ¥438.58 | 2 | ¥878 |
| U709 | 監視IC 5V SOT-23-6 | TPS3808G50DBVR | ¥438.58 | 2 | ¥878 |
| R709–R712 | 1kΩ 0.1% 1206 | RG3216P-1001-B-T1 | ¥49.58 | 10 | ¥496 |
| R701–R704 | 4.7kΩ 0.1% 1206 | RG3216P-4701-B-T1 | ¥49.58 | 10 | ¥496 |
| R705–R708 | 3.3kΩ 0.1% 1206 | RG3216P-3301-B-T5 | ¥49.58 | 10 | ¥496 |
| C717–C720 | 1.8nF C0G 1206（車載） | CGA5H4C0G2J182J115AA | ¥122 | 10 | ¥1,220 |

**マルツ小計（税抜）≒ ¥4,710**

### 選定メモ

- 抵抗・1.8nF は実装4 + 予備で **各10個**。20個は過剰のため削減。
- 半導体は各2（実装1 + 予備1）。SOT-23/-6 は実装失敗しやすいので適正。
- **Q701 AO3401A は不使用になった（2026-07-26）**。3.3V GPIO で 5V レールを切れないため U710 XC8107 に置換。発注済みの AO3401A ×2 は在庫として保管。
- `RG3216P-3301-B-T5` はメーカー荷姿がリールだが、マルツは **1個単位切り売り**で可。
- 1.8nF は一般品 C3216 でも同等性能だが、差額¥4/個のため車載 CGA5 を採用（耐クラック余裕）。
- 定格 630V はオーバースペックだが C0G なので問題なし。

---

## 秋月: 追加発注（2026-07-26） — LCD ロードスイッチ置換

`Q701` AO3401A は Pico の 3.3V High で 5V レールを切れないため、**U710 XC8107AC20MR-G**（Torex, SOT-25）に置換。

| # | コード | 品名 | 単価 | 数 | 小計 | Ref |
|---|---|---|---|---|---|---|
| 1 | [131334](https://akizukidenshi.com/catalog/g/g131334/) | 高機能パワースイッチ XC8107AC20MR-G | ¥60 | 2 | ¥120 | U710（実装1+予備1） |

**追加小計 ≒ ¥120**（在庫: 通販1,376個・秋葉原店21・八潮店11 / 2026-07-26 時点）

### 選定理由（TPS22919 との比較）

| 項目 | XC8107AC20MR-G | TPS22919 |
|---|---|---|
| 国内在庫 | 秋月に単品在庫あり ¥60 | 秋月・マルツになし。DigiKey Japan に 70,842個 ¥39〜 |
| CE しきい値 | VCEH **1.5V min**（VIN=5.5V）→ 3.3V GPIO で直接 ON | ON pin 低しきい値、Smart Pull Down 内蔵 |
| パッケージ | SOT-25（0.95mm ピッチ）＝手はんだ容易 | SC70-6（0.65mm ピッチ） |
| 保護 | 電流制限 2.40A typ・短絡 1.20A・逆流防止・TSD・UVLO・FLG | 自己保護（短絡）＋熱遮断 |
| ソフトスタート | 0.6ms typ | Controlled rise time |

- **注意**: CE に内部プルダウンが無い（CE 電流 ±0.1µA、データシートは「CE をオープンにするな」と明記）。`R717` 100k を CE→`D_GND` のプルダウンに転用して解決（手持ち・追加購入なし）。
- 電流制限 2.40A typ は LCD 負荷（〜200mA）に対して緩く、実質は**短絡保護＋ソフトスタート＋逆流防止**が効く。細かい制限が欲しい場合は 0.5A 品（制限 0.90A typ）だが秋月在庫は 2.0A 品のみ。
- `C740`(CIN) / `C739`(CL) は**購入済みの 10µF50V 3216（秋月 117338, 2パック20個）を流用** → 追加購入なし。データシート推奨は 1.0µF 以上。

---

## メモ

- **オーダー終了（2026-07-17）／追加1点（2026-07-26）**: 共立・秋月・マルツ・千石・手持ちで BOM コンプリート。追加は XC8107 のみ。  
- **MBC2596-01 FP（2026-07-23）**: 実測で `Library:MBC2596-01_TAEJIN_43x21mm` 作成・U705 割当済（角から3.5mm、穴≈φ1.3）。  
- **ADC1804_F FP（2026-07-26）**: 実測で `Library:ADC1804_F_KYOHRITSU_56x33mm` 作成・A701 割当済。親は 2.54 メスソケット推奨（モジュールは同梱オスヘッダ）。CN5F OVFL/OVFR は NC（未配線）。  
- 基板オペアンプは **OPA1656ID（SOIC-8・共立 M1S412×4）** 発注済み。  
- 共立 **OPA1652 DIP化モジュール（Q5M411）×4** は **AdcBuffer AMP501** 実装（1+予備）。MeasurementADC の SOP は OPA1656 のまま。  
- ADA4075-2 は検討後取り下げ。  
- 秋月送料無料は **¥11,000**。今回は送料払い推奨。  
- Tayda は必須部品が揃わないため、今回は **秋月優先**。  
- マルツ（精密抵抗・監視IC・MOSFET・1.8nF）は確定済み。  
- 秋月（電源・バルク・セラミック）は確定済み（小計 ≒¥8,060 + 送料）。  
- 千石（0.1µF×40 / 0.01µF×30）購入済。  
- 次工程: PCB 配置（ADC1804_F FP 済）。
