indare/pcb_work/Audio/MeasurementADC_BOM.md

# MeasurementADC 次号 BOM

日付: **2026-08-21**  
正: `MeasurementADC1804_Module.kicad_sch`（rev 0.4 以降の FP・極性）。1 台分。  
初号の発注履歴は `MeasurementADC_ORDER.md`（そちらの Ref は 2026-07 時点で、現行と一致しない）。

数量の「+予備」は手はんだ欠け用。コア IC は初号で予備を買済みのものが多い。

---

## 在庫で足りる（新規不要）

| Ref | 値 / 型 | FP | 在庫 |
|---|---|---|---|
| A701 | ADC1804_F | 共立モジュール | 共立 C7E412 |
| A702 | Pico 2 | Pico THT | 手持ち |
| LCDDisplay701 | WAVESHARE-29318 | 1×15 ピンヘッダ | 手持ち |
| U701–U703 | OPA1656ID | SOIC-8 | 共立 M1S412 ×4 |
| U704 | BP5293-50 | SIP-3 | 秋月 111188 ×2 |
| U705 | MBC2596-01 | 43×21 mm | 秋月 131750 ×2 |
| U706 | LT1763CS8-3.3 | SOIC-8 | 秋月 107289 ×2 |
| U707 | LT1763CS8-5 | SOIC-8 | 秋月 107290 ×2 |
| U708 | XC8107AC20MR-G | SOT-23-5 | 秋月 131334 ×2 |
| Y701 | ASFL1-12.288MHZ-EC-T | 5.0×3.2 | 共立 3573061 ×2 |
| R701–R704 | 4.7 kΩ 0.1% | 1206 | マルツ RG3216P-4701 ×10 |
| R705–R708 | 3.3 kΩ 0.1% | 1206 | マルツ RG3216P-3301 ×10 |
| R709–R712, R720 | 1 kΩ 0.1% | 1206 | マルツ RG3216P-1001 ×10（5 本使う） |
| C713–C716 | 1.8 nF C0G | 1206 | マルツ CGA5H4C0G2J182 ×10 |
| C703, C704 | 10 µF 50 V 極性 | ラジアル D5 P2.0 | 秋月 117897 PX ×10 |
| C723, C726 | 47 µF（15 V は 35 V 以上、5 V は 16 V 以上） | ラジアル D8 P3.5 | 秋月 116868 47 µF 63 V PZJ ×10 |
| C734 | 22 µF 16 V 以上 | ラジアル D6.3 P2.5 | 秋月 108294 OS-CON 22 µF 35 V ×10 |
| C724, C728, C731, C732, C737, C738, C739 | 10 µF 積セラ（15 V 入口は 25 V 以上） | 1206 / 3216 | 秋月 117338 10 µF 50 V 3216 ×20 |
| J701, J702 | 2P 端子 | P5.08 | 手持ち |
| J703 | 3P 端子 | P5.08 | 手持ち |
| Pico / LCD ヘッダ | 20P メス、1×15 オス | 2.54 | 手持ち（40P から切る） |
| NT701, NT702 | ネットタイ | SMD Pad 2.0 | 銅のみ（部品なし） |
| TP701 | ADC_MCLK | Pad D1.5 | 銅のみ |

TPS3808 G33/G50、AO3401A、千石 RDE 100 nF/10 nF、タクマン THT、中華 THT 抵抗は **次号では使わない**（初号・他基板・予備）。

---

## 新規発注（次号で足りない）

実装数は 1 台分。買う数は欠け用込み。

| Ref | 値 | FP | 実装 | 買う目安 | メモ |
|---|---|---|---|---|---|
| C701, C702, C705, C706, C711, C712, C717–C722, C725, C727, C729, C730, C733, C740, C741, C743 | 100 nF 50 V X7R | 1206 | 20 | 30〜50 | 千石 RDE はランドが違う。秋月/千石の **3216 チップ** |
| C735, C736, C742 | 10 nF 50 V X7R | 1206 | 3 | 10 | LT1763 BYP×2 + ASFL1。データシート BYP 上限 10 nF |
| C707–C710 | 10 µF 25 V **無極性** | ラジアル D5 P2.0（H7 想定） | 4 | 10 | 音声結合。極性 PX は使わない |
| R713–R716 | 47 Ω 1% | 1206 | 4 | 10 | タクマン THT は載せない |
| R718 | 33 Ω 1% | 1206 | 1 | 10 | MCLK 直列 |
| R719 | 10 kΩ 1% | 1206 | 1 | 10 | `ADC_nRST` プルアップ |
| R717 | 100 kΩ 1% | 1206 | 1 | 10 | U708 CE プルダウン |
| U709 | **TPS3307-33D** | SOIC-8 | 1 | 2 | TPS3808 の代替。マルツ / Digi-Key |
| D701 | RB160M-30 相当 | SOD-123 | 1 | 2 | +5V_D → Pico VSYS。Vf 低めの 30 V 1 A ショットキ |
| F701 | ヒューズ | 現状 THT 軸（要選定） | 1 | 2 | 15 V 入口。定格は実装電流〜0.5 A 想定なら 1 A 遅断など。FP は次号でヒューズホルダに変えてもよい |

---

## コンデンサ早見（役割）

| 役割 | Ref | 種類 |
|---|---|---|
| 溜め・極性電解 | C703, C704, C723, C726, C734 | ラジアル極性 |
| 音声結合 | C707–C710 | 無極性ラジアル |
| LDO / スイッチ直下 10 µF | C724, C728, C731, C732, C737–C739 | 1206 積セラ |
| バイパス 100 nF / 10 nF | 上記 100 nF 20 + 10 nF 3 | 1206 積セラ |
| LPF | C713–C716 | 1206 C0G |

---

## 抵抗早見

すべて **1206**。THT 抵抗は回路図上なし。

| Ref | 値 | 精度 |
|---|---|---|
| R701–R704 | 4.7 kΩ | 0.1%（在庫） |
| R705–R708 | 3.3 kΩ | 0.1%（在庫） |
| R709–R712, R720 | 1 kΩ | 0.1%（在庫） |
| R713–R716 | 47 Ω | 1% で可（新規） |
| R717 | 100 kΩ | 1%（新規） |
| R718 | 33 Ω | 1%（新規） |
| R719 | 10 kΩ | 1%（新規） |
