indare/pcb_work/AudioV2.1/scripts/build_daughter.py

#!/usr/bin/env python3
"""娘基板（4ch）を2種つくる — B3a（スイッチ版）と B3b（リレー版）。

1枚は **AmpCh ×4**（`TMUX7612` ×2 を使い切る / リレーは ×4 とドライバ1個）。
母板スロットは 3 口。番地は娘の A0/A1/A2 ジャンパ（縦積み向け。UI 0x22 を避け
0x20 / 0x21 / 0x23 / 0x24 / 0x25 / 0x26）。同じスイッチ版を最大 6 段まで積める。
D9 のとおりリレー版とも混ぜられる。`AmpChannel` は D22 で両版共通。違うのは切替段だけ。

結線は**ピン先のラベル**で行う（ワイヤは引かない）。`AmpBank` も `ControlPanel` も
同じ流儀で、ネットリストで検証できる。

    python3 AudioV2.1/scripts/build_daughter.py --dry-run
"""

from __future__ import annotations

import argparse
import contextlib
import re
import sys
import uuid
from pathlib import Path

ROOT = Path(__file__).resolve().parents[1]
sys.path.insert(0, str(ROOT / "scripts"))

import generate_kicad_scaffold as scaffold  # noqa: E402
import sch_edit  # noqa: E402
import sch_helpers  # noqa: E402
import sch_import  # noqa: E402
from build_motherboard import _merge_lib_symbols  # noqa: E402
from build_motherboard import ROOT_PATH  # noqa: E402
from build_motherboard import SLOT_ANA_NETS, SLOT_PWR_NETS  # noqa: E402
from generate_kicad_scaffold import PARENT, sheet_block  # noqa: E402
from sch_helpers import embed_lib_symbols, symbol_inst_v10  # noqa: E402

_seq = 0
_NS = uuid.UUID("b2000013-0013-4013-8013-000000000013")


_fixed: list[list] = []   # [[接頭辞, 番号], ...]。fixed_uids() の間だけ使う


def uid() -> str:
    if _fixed:
        _fixed[-1][1] += 1
        return str(uuid.uuid5(_NS, f"{_fixed[-1][0]}/{_fixed[-1][1]}"))
    global _seq
    _seq += 1
    return str(uuid.uuid5(_NS, f"daughter/{_seq}"))


@contextlib.contextmanager
def fixed_uids(prefix: str):
    """後から足す部品の UUID を通し番号から切り離す。

    `uid()` は通し番号なので、途中に部品を足すと**そこから後ろ（Relay 版まで）の UUID が全部ずれる**。
    PCB の部品は回路図のシンボル UUID（KIID パス）で結ばれているので、ずれると次の再生成で
    PCB との対応が切れる。後から足すものはこの中で作り、既存の番号を進めない。
    """
    _fixed.append([prefix, 0])
    try:
        yield
    finally:
        _fixed.pop()


# --- 版ごとの定義 -------------------------------------------------------
SWITCH, RELAY = "switch", "relay"
N_CH = 4  # 1 枚あたり。TMUX は 1 IC = 2ch なので偶数。スロットは母板側で 3 口

VARIANT = {
    SWITCH: dict(
        name="AmpBankSwitch",
        file_uuid="b2000013-0013-4013-8013-000000000013",
        inst_uuid="a1000011-0011-4011-8011-000000000011",   # 旧 AmpBank の枠を再利用
        chan_uuids=[f"a10000{20+i}-00{20+i}-40{20+i}-80{20+i}-0000000000{20+i}" for i in range(N_CH)],
        chan_refs=[6, 7, 8, 9],          # 参照の百の位（6xx..9xx）
        suffix="301",
        slot=1,
        # KiCad はページ番号を階層の浅い順に振る。ルート=1、その直下の
        # MeasureControl / AmpBankSwitch / AmpBankRelay が 2/3/4、その次の段が 5 から。
        page_base=5,
    ),
    RELAY: dict(
        name="AmpBankRelay",
        file_uuid="b2000014-0014-4014-8014-000000000014",
        inst_uuid="a1000013-0013-4013-8013-000000000013",
        chan_uuids=[f"a10000{30+i}-00{30+i}-40{30+i}-80{30+i}-0000000000{30+i}" for i in range(N_CH)],
        chan_refs=[11, 12, 13, 14],
        suffix="302",
        slot=2,
        page_base=9,                     # AmpBankSwitch の 4 枚（5..8）の次
    ),
}

# --- D18 のヘッダ（娘基板側の受け）--------------------------------------
# ⚠ 割当の正は build_motherboard 側（D-k）。ここで literal を持たない。
# 母板とはコネクタ対でも繋がっているので、ピン番号がズレても ERC にも
# ネットリストにも出ず、基板が出来上がってから分かる。
ANA_NETS = dict(SLOT_ANA_NETS)
# pin 11..16 は N.C.（旧 ADDR/SEL）。番地は娘ジャンパ、SEL は娘 MCP（スイッチ）/ 無し（リレー）。
PWR_NETS = dict(SLOT_PWR_NETS)
# スイッチ版もコネクタ割当はリレーと同じ（SEL はコネクタに出さない）。
SWITCH_PWR_NETS = dict(SLOT_PWR_NETS)

# --- MCP23017 -----------------------------------------------------------
# スイッチ版は 1ch=1ビット（4本）、リレー版は 1ch=2ビット（SET/RESET で 8本）。
# 番地は縦積み向けに娘上の A0/A1/A2 ジャンパ（ADDR_A*）。スロットからは来ない。
MCP = "Interface_Expansion:MCP23017x-x-SP"
MCP_COMMON = {"13": "I2C_SDA", "12": "I2C_SCL",
              "15": "ADDR_A0", "16": "ADDR_A1", "17": "ADDR_A2",
              "18": "3V3", "9": "3V3", "10": "D_GND"}        # ~RESET / VDD / VSS
GPA = ["21", "22", "23", "24", "25", "26", "27", "28"]        # GPA0..GPA7
GPB = ["1", "2", "3", "4", "5", "6", "7", "8"]               # GPB0..GPB7
MCP_NC_ALWAYS = ["11", "14", "19", "20"]                     # NC / INTB / INTA
ADDR_JUMPER = "Jumper:SolderJumper_3_Bridged12"
ADDR_JUMPER_FP = "Jumper:SolderJumper-3_P1.3mm_Bridged12_Pad1.0x1.5mm_NumberLabels"
# ジャンパ: pin1=D_GND / pin2=ADDR_Ax / pin3=3V3。参照は版で分ける（S_ADDR_* / R_ADDR_*）。
# 座標の正は現行 sch（縦一列）。
ADDR_JUMPER_AT = {
    SWITCH: {
        "A0": (160.02, 187.96),
        "A1": (160.02, 199.39),
        "A2": (160.02, 210.82),
    },
    RELAY: {
        "A0": (157.48, 189.23),
        "A1": (157.48, 201.93),
        "A2": (157.48, 214.63),
    },
}
# 回路図・PCB シルク共有の番地早見（A2/A1/A0。Bridged12=GND=0、2-3 で 1。UI 0x22 は使わない）
ADDR_JUMPER_NOTE = (
    "I2C ADDR A2/A1/A0\\n"
    "0/0/0=0x20 0/0/1=0x21\\n"
    "0/1/1=0x23 1/0/0=0x24\\n"
    "1/0/1=0x25 1/1/0=0x26\\n"
    "skip 0x22  12=0 23=1"
)

TMUX = "AudioV2:TMUX7612"
C0603 = "Capacitor_SMD:C_0603_1608Metric_Pad1.08x0.95mm_HandSolder"
# 案C（2026-09-11、2026-09-13 更新）: PCB 配置に合わせてピンを組み直す。
# - PCB 上の TMUX は **270°**（KiCad）: 北辺=ピン1–8＝CH{a}、南辺=ピン9–16＝CH{b}
#   （ピン1側を Amp 0°＝ch1/ch3 に向ける）
# - S=後続（各ch出力→フィルム）。D=共通バス AMP_SEL（同一ネットで短絡してよいのは D 同士）
# - SEL: ch{a}=SEL1+SEL4、ch{b}=SEL2+SEL3
# - L/R: 南北とも基板上 L西 R東（偶数 DIP も 0°。旧・南入れ替え／180° は廃止）
TMUX_MAP = {
    # CH{a} ピン1–8（270°の北）
    "6": "CH{a}_OUT_L",   # S4 西寄り → フィルム
    "3": "CH{a}_OUT_R",   # S1 東寄り → フィルム
    "7": "AMP_SEL_L",     # D4
    "2": "AMP_SEL_R",     # D1
    "8": "SEL_CH{a}",     # SEL4
    "1": "SEL_CH{a}",     # SEL1
    # CH{b} ピン9–16（270°の南）※北と同じ列（西=L、東=R）
    "11": "CH{b}_OUT_L",  # S3 西 → フィルム
    "14": "CH{b}_OUT_R",  # S2 東寄り相当 → フィルム
    "10": "AMP_SEL_L",    # D3
    "15": "AMP_SEL_R",    # D2
    "16": "SEL_CH{b}",    # SEL2
    "9": "SEL_CH{b}",     # SEL3
    "13": "+15V",
    "4": "-15V",
    "5": "A_GND",
}

RELAY_SYM = "Relay:AZ850P2-x"
# AZ850P2 DS（端子側・reset 図示）:
#   SET コイル = 1(+)–5(−)、RESET コイル = 10(+)–6(−)
#   reset 状態の接点 = 3–4 / 8–7。SET パルスで 3–2 / 8–9 へ遷移。
#
# ネット名は DS どおり pin5=SETC / pin6=RSTC。
# バス（AMP_SEL）は reset 側の 4/7 に置き、SET 側 2/9 は開放（現行 sch・PCB）。
# → 選択＝RSTC パルス、切断＝SETC パルス。FW はこれに合わせる（「SET＝選ぶ」ならビット入替）。
#
# ⚠ 接点は **ch 出力を COM に、共通バスを投側に**入れる。逆（バスを COM）にすると
#    非選択 ch が共通バスを自分の反対接点へ落としてしまう。
RELAY_MAP = {"1": "+5V_COIL", "5": "CH{n}_SETC", "10": "+5V_COIL", "6": "CH{n}_RSTC",
             "3": "CH{n}_OUT_R", "4": "AMP_SEL_R",
             "8": "CH{n}_OUT_L", "7": "AMP_SEL_L"}
RELAY_NC = ["2", "9"]
# 石は AZ850P2-5 に固定（2026-09-09）。TQ2-L2 は接点 NC/NO 番号が違いうるので挿さない。
RELAY_DESC = ("双コイル・ラッチングリレー。AZ850P2-5 固定（2026-09-09）。"
              "コイルは DS どおり SET=1–5=SETC / RESET=10–6=RSTC。"
              "接点は COM=3/8、reset 側 4/7=AMP_SEL、SET 側 2/9 開放。"
              "選択は RSTC パルス（バスが reset 側のため）。"
              "⚠ 外形（FRT5）が同じ TQ2-L2 などは COM/NC/NO が同じとは限らない。AZ850P2-5 以外を挿さない。")

# ⚠ ULN2803A ではなく TBD62083APG（ピン互換のドロップイン）を使う。
#    §2.7-3 で「ULN2803 のダーリントンが約 1V 落とすので 40℃ 超で AZ850 の
#    Must Operate 3.75V を満たさない」と検算済み。TBD62083APG は DMOS で
#    RON 3.25Ω max、コイル 1 個（125Ω ≒ 40mA）なら降下 0.13V。
#    シンボルはピン互換の ULN2803A を流用し、Value で区別する。
DRV = "Transistor_Array:ULN2803A"
DRV_VALUE = "TBD62083APG"
# ドライバ1個で 8 出力。4ch×2コイル=8本なので **1個で足りる**。
DRV_IN = ["1", "2", "3", "4", "5", "6", "7", "8"]
DRV_OUT = ["18", "17", "16", "15", "14", "13", "12", "11"]   # I1->O1(18) ... I8->O8(11)

CHAN_PINS = [("TONE_L", "input", "L"), ("TONE_R", "input", "L"),
             ("+15V", "input", "L"), ("-15V", "input", "L"), ("A_GND", "bidirectional", "L"),
             ("OUT_L", "output", "R"), ("OUT_R", "output", "R")]

HIER_BASE = [("TONE_L", "input"), ("TONE_R", "input"),
             ("AMP_SEL_L", "output"), ("AMP_SEL_R", "output"),
             ("+15V", "input"), ("-15V", "input"), ("A_GND", "bidirectional")]
# SEL は娘 MCP→TMUX の内部ネット（親シートピンには出さない）。I²C/3V3/D_GND は両版共通。
HIER_DIGITAL = [
    ("I2C_SDA", "bidirectional"), ("I2C_SCL", "bidirectional"),
    ("D_GND", "input"), ("3V3", "input"),
]
HIER_SWITCH_EXTRA = list(HIER_DIGITAL)
HIER_RELAY_EXTRA = list(HIER_DIGITAL) + [
    ("+5V_COIL", "input"), ("GND_COIL", "bidirectional"),
]


def _label(name: str, x: float, y: float, left: bool) -> str:
    rot, just = (180, "right") if left else (0, "left")
    return (f'\t(label "{name}"\n\t\t(at {x} {y} {rot})\n\t\t(effects\n\t\t\t(font\n'
            f'\t\t\t\t(size 1.27 1.27)\n\t\t\t)\n\t\t\t(justify {just} bottom)\n\t\t)\n'
            f'\t\t(uuid "{uid()}")\n\t)\n')


def _nc(x: float, y: float) -> str:
    return f'\t(no_connect\n\t\t(at {x} {y})\n\t\t(uuid "{uid()}")\n\t)\n'


class Builder:
    def __init__(self, variant: str) -> None:
        self.v = variant
        self.cfg = VARIANT[variant]
        # 2026-09-09: 母板中間階層を廃止。パスは /親/娘基板。
        self.path = f"{ROOT_PATH}/{self.cfg['inst_uuid']}"
        self.els: list[sch_import.Element] = []
        self.libs: list[str] = []

    # --- 部品を置いて、ピン先にラベルを撒く ---
    def place(self, lib: str, ref: str, value: str, x: float, y: float,
              nets: dict[str, str], nc: list[str] | None = None,
              footprint: str = "", rot: int = 0, description: str = "") -> None:
        el = sch_import.Element(
            "symbol", symbol_inst_v10(lib, ref, value, x, y, rot, self.path,
                                      footprint=footprint, description=description),
            ref, None, (x, y))
        self.els.append(el)
        if lib not in self.libs:
            self.libs.append(lib)
        pin_order = list(sch_edit.lib_pins(lib).keys())
        tips = dict(zip(pin_order, sch_edit.symbol_tips(el)))
        for num, net in nets.items():
            tx, ty = tips[str(num)]
            self.els.append(sch_import.Element(
                "label", _label(net, tx, ty, tx < x), None, net, (tx, ty)))
        for num in (nc or []):
            tx, ty = tips[str(num)]
            self.els.append(sch_import.Element("no_connect", _nc(tx, ty), None, None, (tx, ty)))

    def cap(self, ref: str, value: str, x: float, y: float, hi: str, lo: str,
            polarized: bool = False, footprint: str = "") -> None:
        lib = "Device:C_Polarized" if polarized else "Device:C"
        fp = footprint or ("Capacitor_SMD:CP_Elec_10x12.6" if polarized else
                           "Capacitor_SMD:C_1206_3216Metric_Pad1.33x1.80mm_HandSolder")
        el = sch_import.Element(
            "symbol", symbol_inst_v10(lib, ref, value, x, y, 0, self.path, footprint=fp),
            ref, None, (x, y))
        self.els.append(el)
        if lib not in self.libs:
            self.libs.append(lib)
        top, bot = sorted(sch_edit.symbol_tips(el), key=lambda p: p[1])
        for (px, py), net in ((top, hi), (bot, lo)):
            self.els.append(sch_import.Element(
                "label", _label(net, px, py, False), None, net, (px, py)))

    def build(self) -> str:
        c = self.cfg
        sfx = c["suffix"]
        # --- AmpChannel ×N_CH ---
        for j, cu in enumerate(c["chan_uuids"]):
            sx, sy = 38.1, 25.4 + j * 35.56
            pins = []
            for k, (nm, kind, side) in enumerate(CHAN_PINS):
                lefts = [p for p in CHAN_PINS if p[2] == "L"]
                if side == "L":
                    px, py = sx, sy + 5.08 + lefts.index((nm, kind, side)) * 5.08
                else:
                    rights = [p for p in CHAN_PINS if p[2] == "R"]
                    px, py = sx + 76.2, sy + 5.08 + rights.index((nm, kind, side)) * 5.08
                pins.append((nm, kind, px, py, 180 if side == "L" else 0))
                net = nm if side == "L" else f"CH{j+1}_{nm}"
                self.els.append(sch_import.Element(
                    "label", _label(net, px, py, side == "L"), None, net, (px, py)))
            saved, scaffold.uid = scaffold.uid, uid
            try:
                blk = sheet_block(cu, f"AmpCh{j+1}", "AmpChannel.kicad_sch",
                                  sx, sy, 76.2, 30.48, pins,
                                  str(c["page_base"] + j), parent_path=self.path)
            finally:
                scaffold.uid = saved
            self.els.append(sch_import.Element("sheet", blk, None, f"AmpCh{j+1}", (sx, sy)))

        # --- MCP23017 + ADDR ジャンパ（両版）---
        # Switch: GPB0..3 = SEL_CH1..4（GPA 未使用）。Relay: GPA に SET/RST。
        mcp = dict(MCP_COMMON)
        if self.v == SWITCH:
            for i, ch in enumerate(range(1, N_CH + 1)):
                mcp[GPB[i]] = f"SEL_CH{ch}"
            nc = GPA + GPB[N_CH:] + MCP_NC_ALWAYS
            addr_prefix = "S_ADDR"
        else:
            # DIP 0° で U321 を右に置くと、MCP 右列 28→20 と ULN 左列 1→9 が
            # 2.54 mm ピッチで向かい合う。I1=SET→SETC、I2=RST→RSTC（DS どおり）。
            for i, ch in enumerate(range(1, N_CH + 1)):
                mcp[GPA[7 - i * 2]] = f"CH{ch}_SET"
                mcp[GPA[6 - i * 2]] = f"CH{ch}_RST"
            nc = GPB + MCP_NC_ALWAYS
            addr_prefix = "R_ADDR"
        self.place(MCP, f"U_IO{sfx}", "MCP23017", 200.66, 213.36, mcp, nc,
                   footprint="Package_DIP:DIP-28_W7.62mm")
        self.cap(f"C_IO{sfx}", "100nF", 236.22, 213.36, "3V3", "D_GND", footprint=C0603)
        for bit, (jx, jy) in ADDR_JUMPER_AT[self.v].items():
            self.place(ADDR_JUMPER, f"{addr_prefix}_{bit}", f"ADDR {bit}",
                       jx, jy,
                       {"1": "D_GND", "2": f"ADDR_{bit}", "3": "3V3"},
                       footprint=ADDR_JUMPER_FP)
        self.els.append(sch_import.Element(
            "text",
            f'\t(text "{ADDR_JUMPER_NOTE}"\n'
            '\t\t(exclude_from_sim no)\n'
            '\t\t(at 152.4 175.26 0)\n'
            '\t\t(effects\n'
            '\t\t\t(font\n'
            '\t\t\t\t(size 1.27 1.27)\n'
            '\t\t\t)\n'
            '\t\t\t(justify left bottom)\n'
            '\t\t)\n'
            f'\t\t(uuid "{uid()}")\n'
            '\t)\n',
            None, None, (152.4, 175.26)))
        self.cap(f"C_BULK_P{sfx}", "100uF 35V", 251.46, 213.36, "+15V", "A_GND", True)
        self.cap(f"C_BULK_N{sfx}", "100uF 35V", 266.7, 213.36, "A_GND", "-15V", True)

        # --- 切替段 ---
        if self.v == SWITCH:
            for i, (a, b) in enumerate([(1, 2), (3, 4)]):
                ref = f"U{311+i}"
                nets = {num: tmpl.format(a=a, b=b) for num, tmpl in TMUX_MAP.items()}
                self.place(TMUX, ref, "TMUX7612", 150.0 + i * 63.5, 290.0, nets, ["12"],
                           footprint="Package_SO:TSSOP-16_4.4x5mm_P0.65mm")
                # 100 nF は 0603 にして TMUX 本体直下の裏へ（2026-09-24。パッド列の内側にビアを出し、ピンの足元で受ける）
                self.cap(f"C{311+i*2}", "100nF", 130.0 + i * 63.5, 315.0, "+15V", "A_GND", footprint=C0603)
                self.cap(f"C{312+i*2}", "100nF", 137.62 + i * 63.5, 315.0, "A_GND", "-15V", footprint=C0603)
                # 2026-09-24: DS p34 推奨の 1 µF（0.1 µF と両方。小さい方をピン直近）。
                # 決定は v2 の DECISIONS「TMUX7612 に 1 µF / 50 V / X7R を追加（スイッチ版のみ）」。
                # サイズは 0603（ユーザー指示。ピンに寄せられ ESL も下がる）。⚠ 50 V X7R の 0603 は
                # 15 V の DC バイアスで実効容量が大きく落ちる — 発注時に DC バイアス特性で選ぶ
                with fixed_uids(f"tmux_1u/{ref}"):
                    for k, (hi, lo) in enumerate((("+15V", "A_GND"), ("A_GND", "-15V"))):
                        self.cap(f"C{315+i*2+k}", "1uF 50V X7R", 114.76 + k * 7.62 + i * 63.5, 315.0,
                                 hi, lo, footprint=C0603)
        else:
            for n in range(1, N_CH + 1):
                self.place(RELAY_SYM, f"K{300+n}", "AZ850P2-5",
                           150.0 + (n - 1) * 45.72, 290.0,
                           {k: v.format(n=n) for k, v in RELAY_MAP.items()}, RELAY_NC,
                           # FP は v1 実績の FRT5。⚠ 外形が同じ TQ2-L2 は接点ピンの割り当てが
                           #    違う（2026-09-09 査読）ので「互換」ではない。石は AZ850P2-5 に固定
                           footprint="Relay_THT:Relay_DPDT_FRT5",
                           description=RELAY_DESC)
            nets = {"9": "GND_COIL", "10": "+5V_COIL"}
            # I1/O18=SET/SETC→リレー pin5、I2/O17=RST/RSTC→リレー pin6（DS どおり）
            for k, ch in enumerate(range(1, N_CH + 1)):
                nets[DRV_IN[k * 2]] = f"CH{ch}_SET"
                nets[DRV_IN[k * 2 + 1]] = f"CH{ch}_RST"
                nets[DRV_OUT[k * 2]] = f"CH{ch}_SETC"
                nets[DRV_OUT[k * 2 + 1]] = f"CH{ch}_RSTC"
            self.place(DRV, "U321", DRV_VALUE, 150.0, 340.0, nets, None,
                       footprint="Package_DIP:DIP-18_W7.62mm")
            self.cap("C321", "100uF 25V", 320.0, 340.0, "+5V_COIL", "GND_COIL", True)
            self.cap("C322", "100nF", 335.0, 340.0, "+5V_COIL", "GND_COIL", footprint=C0603)

        # --- D18 のヘッダ（娘基板側のオス。ピン長は FP に出ない発注属性）---
        # A5 案a: ロングテール約11mm で基板間15mm。J_ANA は金メッキ（音声）。
        self.place("Connector_Generic:Conn_02x05_Odd_Even", f"J_ANA{sfx}",
                   f"SLOT ANA (D18)", 340.36, 60.96, ANA_NETS,
                   footprint="Connector_PinHeader_2.54mm:PinHeader_2x05_P2.54mm_Vertical",
                   description="基板間15mm用ロングテール（約11mm）・金メッキ。母板ソケットと対（A5案a）")
        pwr = SWITCH_PWR_NETS if self.v == SWITCH else PWR_NETS
        used = set(pwr)
        self.place("Connector_Generic:Conn_02x08_Odd_Even", f"J_PWR{sfx}",
                   f"SLOT PWR/CTRL (D18)", 340.36, 116.84, pwr,
                   [str(pin) for pin in range(1, 17) if pin not in used],
                   footprint="Connector_PinHeader_2.54mm:PinHeader_2x08_P2.54mm_Vertical",
                   description="基板間15mm用ロングテール（約11mm）。母板ソケットと対（A5案a）")

        # --- 取付穴（A2: M3 φ3.2 を四隅、端から 5.0 mm）---
        # ピンが無いのでネットは持たない。v1 と同じく回路図にシンボルを置いて
        # PCB とフットプリントの対応を取る（board 側だけに足すと parity が崩れる）。
        # ⚠ 穴の実座標は外形に依存するので PCB が正。ここは「4個あること」だけ。
        for i in range(4):
            self.place("Mechanical:MountingHole",
                       f"H{300 + (c['slot'] - 1) * 10 + i + 1}", "M3",
                       340.36 + i * 12.7, 160.02, {},
                       footprint="MountingHole:MountingHole_3.2mm_M3")

        # --- 階層ピン ---
        hier = HIER_BASE + (HIER_RELAY_EXTRA if self.v == RELAY else HIER_SWITCH_EXTRA)
        saved, scaffold.uid = scaffold.uid, uid
        try:
            for i, (nm, shape) in enumerate(hier):
                hx, hy = 419.1, 40.64 + i * 7.62
                self.els.append(sch_import.Element(
                    "hierarchical_label", scaffold.hier_label(nm, shape, hx, hy, 0),
                    None, nm, (hx, hy)))
                self.els.append(sch_import.Element(
                    "label", _label(nm, hx, hy, False), None, nm, (hx, hy)))
        finally:
            scaffold.uid = saved

        lib = _merge_lib_symbols([embed_lib_symbols(self.libs)])
        header = (f'\n\t(version 20260306)\n\t(generator "eeschema")\n'
                  f'\t(generator_version "10.0")\n\t(uuid "{c["file_uuid"]}")\n'
                  f'\t(paper "A2")\n{lib}')
        footer = '\t(sheet_instances\n\t\t(path "/"\n\t\t\t(page "1")\n\t\t)\n\t)\n'
        return "(kicad_sch" + header + "".join(e.text for e in self.els) + footer + ")\n"


def rewrite_ampchannel_instances() -> tuple[str, list[str]]:
    """`AmpChannel` の instances を新しい3階層のパスへ張り替える。

    パスは `/親/娘基板/ch` の3段。生成シートはスイッチ＋リレーの 4×2 = 8 パス
    （物理スロット3口目は同じ `AmpBankSwitch` を挿すだけで、別ファイルは持たない）。
    参照は **娘基板1 が 6xx..9xx、娘基板2 が 11xx..14xx**。
    """
    s = sch_import.load(ROOT / "AmpChannel.kicad_sch")
    sw, rl = VARIANT[SWITCH], VARIANT[RELAY]
    order = [(sw["inst_uuid"], u) for u in sw["chan_uuids"]] + \
            [(rl["inst_uuid"], u) for u in rl["chan_uuids"]]
    path_base = ROOT_PATH   # 2026-09-09: 母板中間階層を廃止
    notes: list[str] = []
    for i, e in enumerate(s.elements):
        if e.kind != "symbol":
            continue
        m = re.search(r'\(path "[^"]+"\n\t+\(reference "([A-Za-z_#]+)(\d+)"\)\n\t+\(unit (\d+)\)',
                      e.text)
        if not m:
            continue
        prefix, num, unit = m.group(1), int(m.group(2)), m.group(3)
        base = num % 100 + 600 if num >= 600 else num       # 6xx を基準に揃える
        blocks = []
        for k, (bank, chan) in enumerate(order):
            blocks.append(
                f'\t\t\t\t(path "{path_base}/{bank}/{chan}"\n'
                f'\t\t\t\t\t(reference "{prefix}{base + 100 * k}")\n'
                f"\t\t\t\t\t(unit {unit})\n\t\t\t\t)")
        new_inst = ('(instances\n\t\t\t(project "AudioV2Case"\n'
                    + "\n".join(blocks) + "\n\t\t\t)\n\t\t)")
        start = e.text.index("(instances")
        end = e.text.rindex("\t\t)\n\t)\n")
        s.elements[i] = sch_import.Element(
            e.kind, e.text[:start] + new_inst + "\n\t)\n", e.ref, e.name, e.at)
        notes.append(f"{prefix}{base} -> {prefix}{base}..{prefix}{base + 900}")
    return s.render(), notes


PARENT_SHEETS = [
    (SWITCH, (80.0, 150.0), (35.56, 114.3)),
    (RELAY, (160.0, 150.0), (35.56, 114.3)),
]

# 親側でシートピンに置くラベル。娘基板の階層ピン名をそのまま使うと**両スロットが
# 同じネットに合流してしまう**ものを、ここで差し替える。
#   - ADDR0/ADDR1 は廃止（縦積みは娘ジャンパ）。残っているのは記録用の旧表。
#   - +5V_COIL / GND_COIL は母板側と同名（2026-09-04 に母板を +5V -> +5V_COIL へ
#     揃えたので恒等。以前は母板が +5V で名前が食い違っていた）
PARENT_NET = {
    SWITCH: {},
    RELAY: {"+5V_COIL": "+5V_COIL", "GND_COIL": "GND_COIL"},
}


def patch_parent() -> str:
    """⚠ 2026-09-04 以降は使わない。娘基板は母板の子になり、シートを置くのは
    build_motherboard.py の CHILD_SHEETS。残してあるのは経緯の記録のため。"""
    p = sch_import.load(ROOT / "AudioV2Case.kicad_sch")
    drop_names = {"AmpBank"} | {VARIANT[v]["name"] for v, _, _ in PARENT_SHEETS}
    drop_pins: set[tuple[float, float]] = set()
    kept = []
    for el in p.elements:
        if el.kind == "sheet" and el.name in drop_names:
            for m in re.finditer(r'\(pin "[^"]+" \w+\n\t\t\t\(at (-?[\d.]+) (-?[\d.]+)', el.text):
                drop_pins.add((round(float(m.group(1)), 2), round(float(m.group(2)), 2)))
            continue
        kept.append(el)
    kept = [e for e in kept if not (e.kind == "label" and e.at
                                    and (round(e.at[0], 2), round(e.at[1], 2)) in drop_pins)]

    saved, scaffold.uid = scaffold.uid, uid
    try:
        for v, (sx, sy), (w, h) in PARENT_SHEETS:
            cfg = VARIANT[v]
            hier = HIER_BASE + (HIER_RELAY_EXTRA if v == RELAY else HIER_SWITCH_EXTRA)
            pins = []
            li = ri = 0
            for nm, shape in hier:
                left = shape != "output"
                if left:
                    px, py = sx, sy + 7.62 + li * 7.62
                    li += 1
                else:
                    px, py = sx + w, sy + 7.62 + ri * 7.62
                    ri += 1
                pins.append((nm, shape, px, py, 180 if left else 0))
                net = PARENT_NET[v].get(nm, nm)
                kept.append(sch_import.Element(
                    "label", _label(net, px, py, left), None, net, (px, py)))
            kept.append(sch_import.Element(
                "sheet",
                sheet_block(cfg["inst_uuid"], cfg["name"], f"{cfg['name']}.kicad_sch",
                            sx, sy, w, h, pins, "1"),
                None, cfg["name"], (sx, sy)))
    finally:
        scaffold.uid = saved

    p.elements = kept
    # 娘基板2枚ぶん増えたので用紙を A3 へ（既存シートの座標は動かさない）
    p.header = [h.replace('(paper "A4")', '(paper "A3")') for h in p.header]
    return p.render()


def main() -> int:
    ap = argparse.ArgumentParser()
    ap.add_argument("--dry-run", action="store_true")
    a = ap.parse_args()
    # symbol_inst_v10 / pin_uuid_block は sch_helpers.new_uid()（uuid4 = 乱数）を
    # 使う。ここを差し替えないと再実行でシンボルの uuid が毎回変わり、
    # 「冪等・再実行でバイト一致」（CLAUDE.md）が成立しない。
    # 下の3箇所で scaffold.uid は個別に差し替えているが、片方だけでは足りない
    # （同じ罠の実測は build_motherboard.daughter_slots() の注記にある）。
    # ここは生成全体を覆うので、build() / rewrite_ampchannel_instances() /
    # patch_parent() のすべてが決定的な uid() を通る。
    saved_new_uid, sch_helpers.new_uid = sch_helpers.new_uid, uid
    try:
        return _build_all(a)
    finally:
        sch_helpers.new_uid = saved_new_uid


def _build_all(a) -> int:
    outs = {}
    for v in (SWITCH, RELAY):
        b = Builder(v)
        outs[VARIANT[v]["name"]] = b.build()
        print(f"{VARIANT[v]['name']}: 部品 "
              f"{len([e for e in b.els if e.kind=='symbol'])} / "
              f"シート {len([e for e in b.els if e.kind=='sheet'])} / "
              f"ラベル {len([e for e in b.els if e.kind=='label'])} / "
              f"階層ピン {len([e for e in b.els if e.kind=='hierarchical_label'])}")
    chan, notes = rewrite_ampchannel_instances()
    print("AmpChannel の参照:", ", ".join(notes[:3]), f"… 計 {len(notes)} 部品")
    # 2026-09-04: 娘基板は母板の子になったので、親は触らない。
    # シートを置くのは build_motherboard.py（CHILD_SHEETS）。
    parent = ""
    if a.dry_run:
        return 0
    written = []
    for name, text in outs.items():
        if len(text) < 1000:          # 空や欠けたものを書き込まない安全弁
            raise SystemExit(f"{name}: 生成結果が短すぎる（{len(text)} bytes）")
        sch_helpers.write_sch(ROOT / f"{name}.kicad_sch", text)
        written.append(ROOT / f"{name}.kicad_sch")
        print(f"書き出し: AudioV2.1/{name}.kicad_sch ({len(text)} bytes)")
    sch_helpers.write_sch(ROOT / "AmpChannel.kicad_sch", chan)
    written.append(ROOT / "AmpChannel.kicad_sch")
    print("書き換え: AmpChannel.kicad_sch（親は build_motherboard.py が扱う）")
    sch_helpers.canonicalize_sch(written)
    print(f"正準化: {len(written)} 枚を kicad-cli sch upgrade に通した")
    return 0


if __name__ == "__main__":
    raise SystemExit(main())
